naizhao/Pilot-Kit-Box-ESP32-P4/hardware/expansion-board-v4/SELECTIVE_PLACEMENT-zh_CN.md

# V4.5 选择性贴装 / 互斥件总表

英文版：[`SELECTIVE_PLACEMENT.md`](SELECTIVE_PLACEMENT.md)

> 这块板上有若干位号**不是照着 BOM 全贴就对**：有的分版本、有的三选一、
> 有的要看实测、有的平时贴但测天线时要取下。规则原先散在
> `VARIANTS.md`、`ASSEMBLY.md` 和原理图里，集中到这一份。
>
> 这些规则在生成制造文件时有断言把关，贴错会让构建直接失败。
> 文档会过时，断言不会。

本板当前配置：**带电源版（powered）**。

位号在板上的位置：[ASSEMBLY_MAP-V4.6.pdf](ASSEMBLY_MAP-V4.6.pdf)（公开版）、
`internal/装配图-本轮打板-V4.6-zh_CN.pdf`（多标本轮要自己补贴的件）。
两份都按本表的判据生成，与这张表同源。

---

## ① 电源变体 —— 两组逻辑相反 🔴 贴错会烧板

同一块 PCB 出两个版本，**这一组是全表唯一"贴错就烧板"的**：

| | 电源部分（28 个位号） | `R7` `R8`（5.1kΩ CC 下拉） |
|---|---|---|
| **带电源版**（本板） | ✅ 全贴 | ❌ **绝不能贴** |
| 不带电源版 | ❌ 全不贴 | ✅ 必须贴 |

**电源部分**：`U18` `U19` `U20` `L16` `L17` `J9` `RT1` `C70`~`C80` `R37`~`R46`

**为什么会烧**：USB-C 要被主机识别，CC 脚必须有 Rd。带电源版由 CH224K(`U18`)
内部提供；此时再并上外部 5.1k，**CC 阻值被拉低 → PD 协商误判 → 可能请求
9V/12V 灌进按 5V 设计的板子**。反过来，不带电源版没有 CH224K，
若 `R7`/`R8` 也不贴则 CC 悬空——**电脑完全不认，RP2040 固件刷不进去**。

> 板上 `R7`/`R8` 周围印了丝印框，标注 **`NO-PWR VER`** ——
> **框内的件只有不带电源版才贴**。

这一组里有两条选型/装配约束，配料和贴装时都要照顾到：

| 位号 | 约束 |
|---|---|
| `L16` `L17` | 功率电感，**只按电感值配料会拿到 Isat 不够的**——`L16` 要 ≥5A、`L17` 要 ≥4A |
| `J9` `RT1` | 在 **B 面**（`RT1` 是 NTC，必须贴到能测电池温度的位置）|

---

## ② 1090 天线通路 —— 三选一

信号从天线到接收链要经过一个二选一的切换点，有三种实现，**最多只能贴一个**：

| 位号 | 作用 | 贴了之后 |
|---|---|---|
| **`U16`** | 射频开关 SPDT（XA17-G4K）| 软件切换外接/板载，**默认方案** |
| `R24` | 0R 旁路 → 固定走**外接**天线 | 短接 `SW1_J2`↔`SW1_J1`，绕过开关 |
| `R25` | 0R 旁路 → 固定走**板载 IFA** | 短接 `SW1_J3`↔`SW1_J1`，绕过开关 |

```
                    ┌── SW1_J2 ──[C30]── ANT1090_EXT ── J6 / D2 / L14   外接
接收链 ──[C54]── SW1_J1 ──(U16)
                    └── SW1_J3 ──[C53]── IFA_MATCH ── ZS1/ZP2/J7 ── ANT1  板载
                         ↑R25 旁路        ↑R24 旁路接的是 SW1_J2
```

**同时贴的后果**：
- `R24` + `R25` → **外接天线和板载 IFA 直接短路并联**，阻抗全乱
- `U16` + 任一旁路 → 开关的一个端口被短接到公共端，切换失效且可能损坏开关

**默认方案：贴 `U16`，`R24`/`R25` 保持 DNP。**
两个旁路位是留给「不要开关、固定走某一路」的改法，正常不贴。

---

## ③ GNSS 天线通路 —— 只有开关，无旁路

| 位号 | 作用 |
|---|---|
| **`U17`** | 射频开关 SPDT，切换外接 / 内置 patch |
| `J2` | 外接口（经尾线转 SMA）|
| `J8` | 内置 patch 口 |

```
GNSS 前端 ──[C57]── SW2_J1 ──(U17)──┬── SW2_J2 ──[C58]── J2  外接
                                    └── SW2_J3 ──[C59]── J8  内置patch
```

**与 1090 侧的区别：GNSS 侧没有旁路电阻**，不贴 `U17` 就没有任何通路。
**`U17` 装配时必须贴上**，否则 GNSS 完全收不到信号。

**有源天线偏置：** 两路都是有源天线，各有一个偏置 Tee（开关 RF 口不能过直流）。PMOS 源极接模块的 `VCC_RF`(U7.14)，不是 3V3_GNSS LDO 轨——模块据此感知天线电流并输出 `ANTENNA OK/OPEN/SHORT`。

---

## ④ IFA π 型匹配网络 —— 调谐用，不是互斥

| 位号 | 位置 | 默认 | 说明 |
|---|---|---|---|
| `ZS1` | 串联 | **0R**（直通）| `ANT1090_IFA` ↔ `IFA_MATCH` |
| `ZP1` | 并联·天线侧 | **DNP** | `ANT1090_IFA` ↔ GND |
| `ZP2` | 并联·电台侧 | **DNP** | `IFA_MATCH` ↔ GND |

三个可任意组合成 L 型 / π 型，**值由实测定**，不存在互斥。
默认 `ZS1=0R` + `ZP1/ZP2=DNP` 只是一条直通线，**不代表已调谐**。

首轮扫描起点（来自六层 rev2 的 HFSS）：`ZS1=3.6nH`、`ZP2=3.3pF`、`ZP1=DNP`，
手头备 3.6/3.9pF，最终值由装壳后 VNA 定。

---

## ⑤ 经`J7`测量时的条件性后级隔离

`C53`（100pF）串在 `IFA_MATCH` ↔ `SW1_J3` 之间，是板载 IFA 通往射频开关的耦合电容。

必要条件是`C53`后方电气断路。V4.0实测板虽然已贴`C53`，但U17等后级元件未贴，
没有形成负载通路，所以不影响读数。只有后级已经贴通的板才需要拆`C53`或用其它方式隔离。

---

## ⑥ 0R 跳线 —— 默认贴，留作调试断点

| 位号 | 连接 | 用途 |
|---|---|---|
| `R21` | `AD8313_VOUT` ↔ `RF_DET_OUT` | 检波输出→分压网络，断开可单独测 AD8313 |
| `R22` | `ANT_SEL_1090_A` ↔ `V1` | 1090 开关控制线，断开可手动置位 |
| `R23` | `ANT_SEL_1090_B` ↔ `V2` | 同上 |

这三个**默认贴 0R**，不是 DNP，也不互斥。

---

## ⑦ 本来就没有器件的位号

| 位号 | 说明 |
|---|---|
| `ANT1` | 板载 IFA，就是 PCB 铜箔本身 |
| `SW2` | BOOTSEL 焊盘跳线，用镊子短接，**不占贴片面** |
| `H1`~`H4` | M2.5 安装孔（⌀2.7mm NPTH）|
| `FID1`~`FID3` | 光学基准点（简化贴装工艺用不上，保留给需要它的贴装线）|

---

## 这些规则有机器把关

上面每一条在生成制造文件时都有断言把关：变体贴错、互斥件同时贴上、分类
漏掉某个位号，构建直接失败而不是出一份看着正常的 BOM。`release/` 里的
BOM/CPL 是通过了这些检查才落盘的。

所以照这份表核对实物即可；表本身与制造文件同源，不会各说各话。
