naizhao/Pilot-Kit-Box-ESP32-P4/hardware/expansion-board-v4/VARIANTS-zh_CN.md

# V4.5 两个版本：带电源 / 不带电源

英文版：[`VARIANTS.md`](VARIANTS.md)

> 2026-08-23。本文件是**变体设计的唯一基准**，ASSEMBLY-zh_CN.md
> 的选贴规则也以这里为准。

## 1. 划分原则

不是「不贴几个件」，而是**两套各自完整的供电系统**：

| | F 面 | B 面 |
|---|---|---|
| **不带电源版** | 全部传感器 + RP2040 + CC1312R + 射频链 + 三颗 LDO | **零贴装件** |
| **带电源版** | 同上 | J4(USB-C PD) + CH224K + SY6970 + SY7069 + L16/L17 + J9 电池座 + 阻容 |

不带电源版**连电池座都不装**——供电、电量信息全部走微雪主板（`VCC_5V` 从 J1 pin1/pin3 进来，
喂 U1/U2/U3 三颗 LDO）。`VCC_5V` 这条网络是双向的，带电源版由 SY7069 输出反灌 J1，
不带电源版由 J1 输入，同一根走线两种方向，不需要任何跳线或改板。

## 2. 为什么要分：成本在 SMT 面数，不在元件费

嘉立创 SMT 在线计价实测（板 10.00×6.20 cm，5 片，2026-08-23）。
下表用**相对倍数**表示，绝对报价会随时间和批量变化，下单前请自行询价：

| 方案 | 贴片层 | 可选档位 | 相对成本 |
|---|---|---|---|
| 带电源版（697 焊点 / 38 种） | 双面 | **只能标准型** | **2.43×**（基准的 2.43 倍）|
| 不带电源版（598 焊点 / 32 种），**仍双面** | 双面 | 只能标准型 | 2.30× |
| 不带电源版（602 焊点 / 33 种），**单面** | 单面 | **经济型** | **1.00×（基准）** |
| 同上走标准型 | 单面 | 标准型 | 1.57× |

费用构成（这才是关键——差额几乎全在固定费，不在焊点数）：

```
                 双面标准型   单面经济型
工程费              高          低      ← 差额主要来源
钢网费              有          无      ← 单面免钢网费
贴片焊点费          ≈           ≈       ← 两者基本相同
换料费(整盘后)      ≈           ≈
```

**两条结论**：

1. **省钱全靠解锁经济型**——嘉立创的「双面贴片暂不支持经济型」是硬门槛。
   单面即使走标准型也只省一半，走经济型才吃到全部差额。
2. **不做到单面，分版本几乎白做**——双面的两个版本只差 5%，省下的焊点费
   被固定的工程费 + 钢网费吃掉了。

## 3. 什么算「一个贴装面」

判据是**这一面有没有需要机器贴装的器件**，不是「有没有铜」：

| | 占面数 | 说明 |
|---|---|---|
| SW2（SolderJumper 焊盘跳线） | **不占** | 不贴任何料，无工序、无钢网、无过炉 |
| 通孔件（若 J9 改弯针） | **不占** | 计在「插件」栏（手工焊点费 ¥2 + 手工工程费 ¥20，固定） |
| J4 (USB-C，16 个 SMD 触点) | **占** | 只要它在 B 面，这一面就是贴装面 |
| 电源那 28 个 SMD | 占 | 带电源版必然双面 |

所以 SW2 留 B 面对成本零影响，不必为它做任何调整。

## 4. 【已实施 2026-08-23】单面可用怎么做到的

产品原则：**单面可用是保底，双面更优**。所以不带电源版的 B 面必须**零贴装件**。

做了三件事：

| 改动 | 原因 |
|---|---|
| **J4 (USB-C) → F 面右板边** (144.63, 73.00) | 留 B 面的话不带电源版还是双面，只省 ¥35 等于白做。courtyard 右沿贴齐板边 150，开口仍朝 +X（与微雪 H1 同侧）。`USB_DP/DM` 连的 R9/R10 本来就在 F 面 x117，搬过去走线反而更短 |
| **新增 R7/R8（5.1k CC 下拉）→ F 面**，紧邻 J4 2.2mm | 不带电源版没有 CH224K，CC 悬空则主机根本不认设备（USB-C 规范要求 device 端呈现 Rd）。**与 CH224K 二选一**：带电源版不贴 |
| R37 从 (138.80,69.84) 挪到 (137.75,70.75) | J4 的通孔安装脚穿到 B 面，落进了 R37 的 courtyard。顺带把它到 CFG1 脚的距离从 2.97mm 缩到 2.56mm |

**验收：不带电源版的 B 面贴装件 = 0**（只剩 SW2 焊盘跳线和 TP 类不占面数的东西）。

代刷方案（原 §4 方案 A）已否决，理由见 §5——GPIO24/25 是 USB Serial/JTAG 不能做 host，
切换要烧不可逆 eFuse。不冒险，J4 保留。

## 5. 查证记录：为什么 GPIO24/25 不能用

**曾经的错误方案**：把 RP2040 的 USB 接到 J1 的 pin23/21，让 P4 做 host 代刷。
查 ESP32-P4 datasheet 后**否决**：

| USB 外设 | 默认引脚 | 能否 host | J3 是否引出 |
|---|---|---|---|
| **USB Serial/JTAG** | **GPIO24 / 25** | ❌ 纯 device | ✅ pin23/21 |
| USB 2.0 **Full-Speed OTG** | **GPIO26 / 27** | ✅ | ❌ **没引出** |
| USB 2.0 High-Speed OTG | 专用脚 49/50 | ✅ | ✅ pin27/25（与 H2 同网） |

- 微雪 J3-23/21 引出的 GPIO24/25 是 **USB Serial/JTAG**，固定 device，不能做 host
- OTG FS 默认在 GPIO26/27，**J3 上没有这两个脚**
- 要把 OTG FS 切到 GPIO24/25 得烧 eFuse `USB_PHY_SEL`——**一次性不可逆，且烧完 P4 的 USB-JTAG 就废了**，而微雪板已出厂，不是我们能控制的

**只剩 HS 那组（J3-27/25）**，但它与 H2 的 USB-C 口同网，且载板 USB-A（RTL-SDR 方案）
也走这条线，三方只能选一个。

## 6. 为什么 C6 要手工 UART 刷，而 RP2040 不用

这个问题决定了「代刷」到底靠不靠谱，答案是**两者的机制完全不同**：

**C6（见 `docs/hardware/c6_slave_firmware-zh_CN.md`）**要外接 USB-UART 接 P1 排针、
IO9 短地、esptool 写 flash。两个原因：

1. **硬件**：微雪把 C6 的 UART 引到独立的 P1 排针，没接到 P4 的 GPIO，P4 够不着
2. **鸡生蛋**：P4↔C6 走 ESP-Hosted over SDIO，而 SDIO 要通，前提是 C6 里已经跑着
   hosted 固件。空白 C6 没固件 → SDIO 不通 → 只能走 ROM 的 UART bootloader，
   而那需要外部工具握手。所以**首次**必须手工，之后才能 OTA。

**RP2040 没有这个问题**：BOOTSEL 固化在 ROM 里，空片上电（或短接 QSPI_SS）直接
变成一个 USB MSC U 盘，不需要预装任何固件、不需要握手协议。这是架构性差异，
不是配置问题。

## 7. 换主板后（如 RK3506）代刷还成立吗

代刷只依赖一条：**上级有 USB host + 能挂载 MSC**。

| 换成 | 能否代刷 |
|---|---|
| RK3506 等 ARM Linux SoC | ✅ 比 P4 还简单，`mount` + `cp x.uf2` |
| 树莓派 CM / 任何 Linux/Android 主板 | ✅ |
| 纯 MCU 且无 USB host | ❌ |

Pilot Kit 要跑 Flutter UI，主控只会越换越强，这条风险低。且 J1 是 2.54mm 排针，
**任何时候都能从排针飞两根线接 USB 转接头直连电脑**，不需要板上有 USB 座，
不占任何 SMT 面数——这是不依赖上级板的兜底路径。

## 8. R7/R8（5.1k CC 下拉）是必需的选贴件

一度以为不需要——那是建立在「不带电源版没有 J4」的假设上。但按 §4，J4 两个版本
都要贴（否则没法刷 RP2040 固件），所以 CC 就必须有 Rd：

| | R7/R8 | CH224K |
|---|---|---|
| 带电源版 | ❌ 不贴 | ✅ 贴，内部自带 Rd |
| 不带电源版 | ✅ **必贴** | ❌ 不贴 |

**两者互斥**：同时贴会让 CC 阻值错乱、干扰 PD 通信（CH224 手册 §6.1 的 Type-C
母口参考电路里 CC 就是直连芯片、没有外部下拉）。
