naizhao/Pilot-Kit-Box-ESP32-P4/docs/ux/box-4.3-ux-spec-zh_CN.md

# Pilot Kit Box · 4.3″ 触摸屏 UX 规格

英文版：[`box-4.3-ux-spec.md`](box-4.3-ux-spec.md)

**状态**：已定稿（2026-07-27）· **v2.1 修订 2026-08-02**
**适用固件分支**：`v4`
**视觉稿**：[`box-4.3-ux-spec.html`](box-4.3-ux-spec.html) —— 按真实毫米绘制，浏览器直接打开，
含显示器校准工具。**已同步到 v2.1**，两份说法一致；不一致时以本文件与代码为准。

版面真源在 `firmware/main/nav_grid_page.h` 的常量区——本文件描述意图，那边是数。

---

## 1. 背景

迁移前基线是 2.4″ 320×240 SPI 屏 + 四个物理按钮；当前硬件已经切换到
微雪 ESP32-P4-WIFI6-Touch-LCD-4.3（480×800 原生竖屏，PPA 逆时针
270°、等效顺时针 90° 后按 **800×480 横屏**使用，GT911 电容触摸）。
控制器支持五点，但当前固件只读取第一触点。

最终目标屏为 5″ 800×480 半反半透（同分辨率），本规格可 1:1 迁移。

### 产品定位（决定所有取舍）

一台设备服务两类用户：

| 用户 | 场景 |
|---|---|
| **爱好者** | 地面观测周边飞机 → 空中录制 + 看姿态 → 落地分享 |
| **飞行员** | 机载备份仪表（**应对 Garmin 高温死机**）+ 交通避撞 + TF 卡记录 + GDL90 喂 App |

共同主页面为「PFD + 下部雷达半透明 overlay」。

---

## 2. ⚠️ 物理尺寸约束（最高优先级）

| 屏 | 分辨率 | 物理尺寸 | 像素密度 | 16px 汉字实际高 |
|---|---|---|---|---|
| 旧 2.4″ | 320×240 | 48.8 × 36.6 mm | 6.56 px/mm · 167 PPI | 2.44 mm |
| **新 4.3″** | 800×480 | **93.7 × 56.2 mm** | **8.54 px/mm · 217 PPI** | 1.87 mm ⚠ |
| 终 5″ | 800×480 | 108.9 × 65.3 mm | 7.35 px/mm · 187 PPI | 2.18 mm |

**4.3″ 横屏物理尺寸约等于一张信用卡（85.6 × 54 mm）。**

> **分辨率提升只带来清晰度，不带来空间。**
> 新屏 217 PPI 比旧屏 167 PPI 还高 30% —— 同样像素数在新屏上**物理更小**。

### 字号阶梯（硬约束）

| 级别 | 物理 | 4.3″ | 5″ | 用途 |
|---|---|---|---|---|
| XL | 5.0 mm | 43 px | 37 px | PFD 当前值 |
| L | 3.5 mm | 30 px | 26 px | 页面标题 |
| **M** | **3.0 mm** | **26 px** | **22 px** | **正文主力** |
| S | 2.5 mm | 21 px | 18 px | 标签 / 单位（**顶栏状态栏走 M 档**，见 §5.1）|
| XS | 2.1 mm | 18 px | 16 px | **硬下限**，仅极次要 |

**低于 18 px（2.1 mm）的字号一律禁止出现。** 旧屏 8×8 汉字（1.22 mm）在新屏对应仅 10 px，永久废弃。

### 各页面容量（按 4.3″ 实测字高定）

| 页面 | 容量 |
|---|---|
| 空管看板 | **7 列 × 7 行**（机型、SQK 入详情） |
| 雷达右栏 | **4 张卡** |
| 诊断卡片 | **每卡 1 行核心值**（详情另开页） |
| 设置页 | **7 行满屏**，第 8 项需滚动 |

---

## 3. 交互模型

### 3.1 物理按键：全部取消

- deep sleep 功能取消（实测休眠功耗降不下来，无实用价值）
- 四个按钮（TARE/MODE/UP/DOWN）全部删除，`button_task.c` 退休
- 板载 POWER 键为**硬件电源开关**（接电源管理 IC，非 GPIO，软件不可读）
- **软件层面 100% 触摸输入**

释放 GPIO：外设需求从 10 根降至 6 根（IMU INT/RST ×2、BARO_INT ×1、GPS ×3）。

### 3.2 FAB + 全屏导航网格

| 一级页面 | 二级页面 |
|---|---|
| FAB = **☰** 点击打开全屏导航网格 | FAB = **←** 点击返回 |

#### 为什么不是横向 dock

一条从 FAB 那侧滑出的横向 dock（导航页签 ×94 px｜分隔线｜动作区「调平」）在
800×480 上**排不下**：

```
7 个页签 × 94 ＋ 分隔 8 ＋ 动作区 94 = 761 px
FAB 两侧留白之后的可用宽度          = 720 px      → 溢出 41 px
```

第 8 项进不来，而页签已经窄到 94 px——再缩就跌破 44 px 触摸下限，换行则宣告
这个形态不成立。因此采用**全屏导航网格**（版面真源 `sim/proto-navgrid/proto.c`）。
若有人再提议「点 FAB 弹一条横向工具条」，先把上面那三行宽度账算一遍。

#### 网格版面（`nav_grid_page.c`）

| 区 | 几何 | 内容 |
|---|---|---|
| 顶栏 | y 0–48，**不遮罩** | 露出**底页自己的**顶栏（底页是 PFD 时即 §5.1 那条状态栏：星数 / 目标数 / REC / 温度 / 蓝牙 / 电量，菜单期间也要能看状态）|
| 网格 | y 48–360，4 列 × 2 行，格 **200 × 156** | 每格：64 px 图标 + M 档标签 |
| 分页点 | y 368，12 px | 仅状态指示，**不可点** |
| 动作条 | y 392–480，高 **88 px**，三等分 | 调平（警示橙）｜屏幕亮度｜关闭 |

- **两页**：第 1 页 7 项（PFD / 交通 / 地图 / 列表 / 搜索 / 记录 / 工具）+ 1 格余量；
  第 2 页 3 项（诊断 / 设置 / 关于）。切分点是**常用度不是塞满**——飞行中最常按的
  几个不该为了凑满一页而往后挪。
- **格子位置钉死，末页不居中**：位置随项数浮动的话，同一功能在两页上落在不同
  坐标，手指记不住位置——而记得住位置正是网格相对列表的全部优势。
- **未实现的「记录」「工具」置灰占位**，不从版面拿掉：将来补上时版面一个数都不用改。
  点了不弹提示，置灰视觉本身就是信号。
- **底页压暗 9%**（不是纯黑遮罩）：地平线的明暗分界仍能隐约辨出，飞行员不会在
  菜单打开的这两秒里失去姿态参照；但白底黑字的高度带 / 速度带不再能读出内容。
- **打开即藏 FAB**：网格铺满全屏且命中判定排在 LVGL 之前，FAB 留着就是"自己点不动、
  又盖住底下的格"，而且它可拖动，挡住哪一格不可预测。出口写在屏上（动作条「关闭」）。

**三条退路**（无物理按键，任何一条失效都还剩两条）：
① 动作条「关闭」　② 第 1 页继续右滑　③ 6 s 无操作自动收起

> 初值沿用 dock 的 5 s（图的是不打破既有手感），2026-08-02 真机走查后调到 **6 s**：
> 网格两页十项比 dock 内容多，翻页才看得全，5 s 不够看完就被收走。
> 真源是 `nav_grid_page.c` 的 `NAV_IDLE_MS`，这个值只能上机试，不要在桌面上推。

**手势**：左右滑动翻页，阈值 60 px（≈7 mm）且横向位移须 > 2× 纵向；过阈值**当场翻**
不等松手；一次长滑可连续翻多页。「调平」沿用长按 1 s 才生效（短按只提示）。

#### FAB 可拖动 + 位置记忆（与 Pilot Kit App 手感一致）

- 长按 **200 ms** 进入拖动态（避免与点击冲突），FAB 半透明 + 亮边 + 阴影加重
  （**不能用 transform_scale**：会让 LVGL 走 TRANSFORM layer，64 KB 池分配不出整块
  buffer，单线程 LVGL 会死在忙等里）
- 拖动实时跟手，垂直位置自由
- 松手后**水平吸附至最近的左 / 右边缘**，不允许悬停中间遮挡内容
- 位置持久化至 NVS：`fab_side`(L/R) + `fab_y`(0~100%)
- 网格是全屏的，**不随 FAB 那一侧翻转**（dock 时代才需要反向铺开）
- 校准向导页不显示 FAB

### 3.3 手势

| 手势 | 作用 |
|---|---|
| 单指垂直滑动 | 列表滚动（雷达右栏、看板、设置、诊断详情） |
| 单指水平滑动 | 导航网格翻页（阈值 60 px 且横向 > 2× 纵向） |
| 右滑 | 二级页面返回；导航网格第 1 页则关闭 |
| 下滑 | 关闭详情抽屉 |

---

## 4. 导航结构与返回规则

> **无物理按键 = 没有系统级返回。** 二级页面若不设计返回，用户进去即出不来。
> 以下路径实现时必须逐条覆盖。

### 4.1 页面分类

| 类型 | 成员 | 特性 |
|---|---|---|
| **一级页面**（7） | PFD / 交通雷达 / 地图 / 空管看板 / 诊断 / 设置 / 关于 | 互相平级，仅通过 **FAB → 全屏导航网格**切换 |
| **模态层**（铺满全屏，压在某一页之上） | 导航网格 / 搜索 / 机场详情 / 键盘编辑器 | 不是 `pk_ui_mode_t` 的一站；打开即藏 FAB，出口写在自己屏上；优先级由 `pk_ui_modal_top()` 单点决定 |
| **二级页面**（全屏替换） | 诊断 → 子系统详情 ×8 | FAB 变 ←，顶栏出现「← 诊断」，此时 FAB 不再是菜单键 |
| **覆盖层**（不替换一级） | 目标详情抽屉 / 格式化确认 / 校准向导 / Toast | 各自带关闭 + 点外部关闭 |

> 一级页面从 6 涨到 7（地图页），并且还有「记录」「工具」两个占位——横向 dock
> 装不下这个数，正是 §3.2 换成网格的直接原因。网格再加项只是多一页，不再有
> 「排不下」这回事。

### 4.2 返回路径

| 所在位置 | 返回方式（任一可用） | 返回目标 |
|---|---|---|
| 一级页面 | —（顶层） | — |
| 子系统详情页 | ① 顶栏「← 诊断」② FAB（此时为 ←）③ 右滑 | 诊断总览 |
| 目标详情抽屉 | ① 「关闭」② 点上方列表区 ③ 下滑 | 看板页（保留选中行） |
| 格式化确认框 | ① 「取消」② 点遮罩 ③ **5 s 超时自动取消** | 设置页 |
| 校准向导 | ① 「稍后再说」② acc≥2 自动退出 | 进入前的页面 |

**特例**：目标详情抽屉的「绑定为本机」是**跨层跳转** —— 执行后关闭抽屉并**直接跳转 PFD**
（让飞行员立刻看到以新 own-ship 为基准的地平线），不返回看板页。

### 4.3 原则

- **层级最多 2 层，不做返回栈**。二级页面只能从诊断进入，返回目标唯一确定。
- **FAB 位置固定不变**，用户只需记住"右下角圆钮"一个位置。

---

## 5. 页面规格

### 5.1 PFD 主页

```
顶栏      48 px   HDG 082° ｜ (卫)17 (机)6 (●)REC (温)88°C ｜ (蓝) (电)100%
主区     292 px   速度带 100 ｜ 姿态区 600 ｜ 高度带 100
底部 HSI 140 px   罗盘 + 交通目标叠加
```

- 速度带下方换算区：km/h + mph（沿用现有设计）
- 高度带下方换算区：VS + m/s（GS/VS 不再单独占角落文字位）
- **姿态区刻意留空**，不加航迹矢量 / 坡度 / G 值等（半反半透屏元素越少越读得出）

#### 顶栏（状态栏）—— 真源 `pfd_statusbar.c` / `pfd_layout.h`

早期版式是 `HDG · ●GPS ●REC ●BLE 🔋 · ADSB 计数` 这样的圆点 + 字母缩写。
**已作废**：圆点只说得出"有/没有"，说不出"几颗星""几架飞机"，而
`ADSB`／`REC` 这类缩写在 26 px 上一项就吃掉 60~90 px。现在中段与右段全部
图标化，图标提供语义、数字提供读数（孤立的 `100%` 看不出是电量还是亮度）。

图标取自 **Material Symbols Rounded**（Google，Apache-2.0），经
`firmware/scripts/gen_pfd_icons.py` 生成 **30 × 30 px、4bpp 灰度**字形表
（`pfd_icon_font.h`），与文字**共用同一条 alpha 混合路径**（`pk_aa_blit_4bpp`），
边缘处理完全一致。FILL 轴按图标取舍：卫星 / 目标 / 录制 / 温度 / 蓝牙取实心
（小尺寸下比线框立得住），**电池取轮廓**（填成实心就看不出电量了）。

顶栏文字是 **M 档（26 px）**，不是 S 档。

| 段 | 槽位（自左向右） | 图标（Material 名） | 内容与颜色 | 数据来源 |
|---|---|---|---|---|
| **左**（常驻） | HDG | 无，青色 `HDG` 文字标签 | `082°` 绿；无航向 `---°` 灰 | `pk_own_heading_resolve()`：ADS-B 绑定机 > IMU yaw > GPS track（≥2 kt） |
| 中 | 卫星 | `satellite_alt` | 星数 绿；无 fix `NO FIX` **红** | `pk_gps_get()` |
| 中 | ADS-B 目标数 | `connecting_airports`（画的是**两架**飞机，要的是"周围有 N 架"的复数语义） | 计数 绿 | `aircraft_state_snapshot()`，60 s 新鲜窗 |
| 中 | 录制 | `fiber_manual_record` | `REC` 红，**仅正在写记录时出现** | `rec_active` |
| 中 | 温度 | `thermometer_alert`（温度计 + 感叹号，比通用三角贴切） | `88°C` 警示橙，**仅超温时出现** | `pk_soc_temp_get()`，见下 |
| **右**（常驻） | 蓝牙 | `bluetooth` | **只有图标、没有文字**（符号本身即可表意），青；未连接则整枚不画 | `ble_gatt_is_connected()` |
| **右**（常驻） | 电量 | `battery_android_*` | 百分比，见下 | `pk_batt_get()` |

几何（`pfd_layout.h`）：条高 48 · 左边距 12 · 右边距 16 · 图标与其数值间隙 2 ·
组内间隙 8（`PFD_BAR_GAP_LABEL`）· 词组之间 16（`PFD_BAR_GAP_WORD`）。

**降级规则**（不是"藏起来"，是整项丢弃）：

- 中段优先级 **GPS > ADSB > REC > TEMP**，依据是"不知道会出事"的程度；
  装不下就从最低优先级那端逐项丢，**GPS 永不丢**。320 屏中段只放得下一项、
  800 屏放得下四项，靠这套规则自适应，不为每种屏手算坐标。
- **左端 HDG 与右端蓝牙 / 电量不参与降级** —— 后两者是「设备自身」的状态而非
  「飞行」的状态。
- 右段按**最坏宽度**（两个图标 + `100%`）预留，蓝牙断开时中段不平移；
  但中段自身是在剩余空间里**居中**的，所以 REC / 温度出现或消失时中段会整体
  重新居中。

**全空态**（实拍 `images/empty-4.3-pfd.png`）：`HDG ---°`（灰）·
卫星图标 + `NO FIX`（红）· 目标图标 + `0`（绿）· **没有** REC / 温度 / 蓝牙 ·
电量照常显示（电池焊在板上，没有"没接"这一说）。

**电量的两个特殊态**：

- 图标是 `battery_android` 系列的 **alert → _0…_6 → full 九档连续刻度**，
  `step = (pct×8+50)/100` 一次线性映射，**形态本身就是读数**。此前的
  `battery_horiz_*` 只有三档，20% 与 4% 会渲染成同一个空壳、只能靠颜色区分。
  末档取 `full` 而不是 `_6`：`_6` 内部还留着一条黑，拿它当 100% 会一直显示成
  "还差一格"。
- 颜色：常态**白**（航电惯例白 = 正常/仅供参考，绿留给需要主动确认有效的读数：
  航向、星数、目标数）· `<25%` 警示橙 · **`≤6%` 红，并同时换成 alert 图标**
  （阈值正是九档刻度里 alert 那一档的覆盖范围，变红与换图标同时发生，
  不各走各的）。实拍 `images/ui-4.3-battery-low.png`。
- **充电**：改播 `battery_android_frame_1…6 → frame_full` 的**逐帧动画** ——
  静态闪电只说明"接了电"，动画才说明"电真的在进"。每帧 300 ms、整周期 2.1 s
  （座舱里任何接近 1 Hz 的动效都会被余光当成告警去抓一下注意力，而充电是最
  不需要被注意的状态）；相位由 `uptime_ms` 算而非数渲染帧，固件与模拟器帧率
  不同也快慢一致。充电时颜色**一律白**：正在回升的低电量不是需要处置的异常，
  涂红只会制造假警报。实拍 `images/ui-4.3-charging.png`。

**温度**：读的是 **SoC 结温**（`soc_temp.c`，1 Hz 采样），不是 BMP388 那颗测
座舱环境温度的传感器 —— 暴晒时二者能差二三十度，「设备自己在过热」是另一回事。
阈值 `CONFIG_PK_SOC_TEMP_WARN_C`，当前 **85 ℃ 触发 / 78 ℃ 解除**（7 ℃ 滞回，
免得那一格出现又消失、把飞行员训练成忽略它）。实拍里显示的 78 ℃ 是模拟器强制
点亮这一格的 mock 值（`sim/main.c`），不是真机的触发点。

**演示模式**：顶栏最右端常驻一枚 96 × 32 的 DEMO 徽标（画在 LVGL 控件层），
所有右对齐内容统一走 `pk_ui_topbar_right_limit()` 退让，中段跟着一起退 ——
顶栏本来就有一套"装不下就按优先级丢"的机制，把新的可用宽度告诉它就够了。
实拍 `images/demo-4.3-pfd.png`。

**这条状态栏只有 PFD 页有。** 其余整屏页面各画各的顶栏（同高 48 px、
标题同为 M 档）：交通 = 标题 + HDG + 目标数 + 朝向/量程；空管看板 = 标题 +
目标数 + 排序说明 + RESET（非默认排序才出现）；地图 = 标题 + 右上角瓦片层级 `Z12`；
设置 / 诊断 / 关于**只有左上角一个标题**；诊断子系统详情页顶上是 LVGL 的
`← 诊断` backbar，子系统名画在内容区第一行（`diag_page.c :: draw_detail_header`）；
罗盘校准向导是全屏页，**没有顶栏**。导航网格与 Toast 压在当前页之上，
露出的是**底页自己的**顶栏。

### 5.2 交通雷达页

- 左雷达 520 px（距离环 6/13/20 NM，本机居中），右栏 280 px 放 4 张卡片可滚动
- **本机符号：飞机俯视剪影**（黄色，6.5 mm）
  - 机头朝上模式：机头恒指屏幕上方
  - 正北朝上模式：按当前航向旋转
  - 由设置页「地图朝向」切换
- **目标符号：飞机俯视剪影**（3.8 mm），**按各自 ADS-B track 航向旋转**
  —— 一眼可辨迎面 / 同向，此信息三角形无法表达
- 右栏卡片：方位八向箭头 + 呼号 + 距离 + 高度（带升降率）+ 速度
- 量程由雷达右下角 +/− 两枚按钮切换（**不做双指捏合**：量程只有
  三四档，用不上捏合的连续性，而戴手套、颠簸时双指手势最容易做废）

### 5.3 空管看板页

7 列 × 7 行，行高 48 px，字号 21 px，可垂直滚动。

| 列 | 方位 | 呼号 | 距离 | 高度 | 升降 | 速度 | 航向 |

红底 = 威胁。点击行 → 详情抽屉（高 230 px，保留上方 2 行可见），
抽屉内补全被砍列：机型 / SQK / ICAO / 航司 / 国籍。

### 5.4 设置页

行高 64 px，控件按钮高 38 px。

| # | 项 | 控件 |
|---|---|---|
| 1 | 语言 | 分段（中文 / EN） |
| 2 | QNH | 步进器（− / 值 / +） |
| 3 | 地图朝向 | 分段（机头上 / 正北上） |
| 4 | 雷达量程 | 分段（10 / 20 / 40） |
| 5 | **屏幕亮度** | 分段（低 / 中 / 高 / 自动）**新增·必需**（原 UP/DOWN 键调节） |
| 6 | **日间/夜间配色** | 分段**新增**（为半反半透屏铺路） |
| 7 | 记录存储 | 分段（Flash / SD 卡） |
| 8 | 格式化 SD | 危险按钮（**需滚动可见**） |

格式化保留现有**两步确认状态机**：首次点击变「再点确认 5s」，超时复位；无卡 / 正写时置灰。

### 5.5 诊断页

2 × 4 卡片，每卡 10.8 mm 高，仅显示**标题 + 一行核心值**。
八格固定：IMU / BARO / GPS / SDR / BLE / LOG / CLK / **SYS**。

**SYS 卡为新增**，含芯片温度 —— 产品定位是"Garmin 高温死机时的备份"，
自身温度必须可见。超温时 **PFD 顶栏中段多出一格「温度计图标 + 结温」**
（警示橙，不是红；红在本项目里留给 `NO FIX` / `REC` / 低电这类"已经出事"）。
阈值 `CONFIG_PK_SOC_TEMP_WARN_C`：当前 **85 ℃ 触发 / 78 ℃ 解除**（见
`soc_temp.c`，7 ℃ 滞回）。

**点卡片进入子系统详情页**，详情必须保留 `diag_page.c` 现有全部深度，尤其：

- **GPS**：fix/HDOP、可见星、天线状态、经纬度、**每星座独立一行的 SNR 柱状图**
  （排查 no-fix 的命门 —— 不能只盯 `fix=0`，要看 SNR 和天线）
- **IMU**：cal N/3 + roll/pitch/yaw + 采样率
- **BARO**：hPa / alt / VS / 温度 / QNH / IIR 系数

### 5.6 关于页

**纯静态身份**：logo / 版本 / 构建时间 / 依赖版本（IDF、LVGL）/ 硬件**型号**（不带在线状态灯）+ 二维码。

所有 ✓ 状态、校准精度、实时数值**一律归诊断页**，两页零重复。

### 5.7 罗盘校准向导

自动进入（acc=0 持续）/ 自动退出（acc≥2 持续），沿用现有逻辑。

**新增「稍后再说」按钮** —— 原靠 MODE 键关闭，按键删除后若不补此按钮，
用户在磁干扰环境下会被**永久卡在本页**。点击后本次开机不再自动弹出（重启复位）。
本页不显示 FAB。

> 「稍后再说」关掉自动弹出之后，必须留一条**手动入口**，
> 否则用户后来想校准时无路可走（自动闸门要等 acc 真的上过 2 才复位）。
> 入口做在**设置页倒数第二行「罗盘校准」**：左边是项名，右边的值框显示当前
> 精度 `质量 n / 3`（一眼判断该不该点），点击进入本页。
> 走 `pk_ui_cal_wizard_enter()` 而不是通用的切页函数——它同时把自动弹出的闸门
> 重新武装，"用户主动来校准"这件事必须能覆盖之前那次「稍后再说」。
> **不进导航网格**：那张表列的是页面，校准是一次动作。

---

## 6. 术语：TARE → LEVEL / 调平

`TARE` 源自称重业"去皮"，飞行员不熟悉。该功能实为 **caging**
（即传统陀螺仪"把罗盘拨杆往外拔"的动作），现有实现也只 cage 横滚/俯仰、航向解耦。

**采用**：英文 `LEVEL`，中文「**调平**」（Dynon SkyView 即用 Level）。

### 四态交互

| 态 | 行为 |
|---|---|
| ① 待机 | 全屏导航网格的动作条左格显示「调平」（警示橙）|
| ② **短按** | **不执行动作**，弹 Toast「长按 1 秒调平地平仪」，1.5 s 后消失（`ui_state.c` 的 `UI_TOAST_DURATION_US`；实现是显示/隐藏，没有淡出动画） |
| ③ 按住 | 橙色填充从左向右走满 1 s，松手或滑出按钮即取消（填充同帧消失） |
| ④ 完成 | 那一格绿闪 200 ms（标签反白成底色）+ Toast 确认，闪完网格自动关闭 |

② 为必需 —— 否则用户点一下没反应会认为按钮失灵。

**③ 的填充色**是 `COL_ACT` 压到 35% 的同色底（`nav_grid_page.c` 的
`COL_ACT_FILL`），不是另一个色相：填充是背景、橙色标签是前景，同色系才读成
「这一格自己在充满」。这一档对标签 5.5:1、对动作条底色 2.0:1，是"字不被吃掉"
与"进度看得出来"两头夹出来的。**不做插值/缓动**——网格打开时约 6 FPS
（真机实测），1 s 只有 6 帧，每帧按当前时刻直接算宽度即可。

**④ 的 200 ms** 是这块屏上"至少能保住一帧、又不至于读成卡顿"的下限。绿档
（`COL_OK`）调色板里原本没有，座舱里绿 = 正常/确认，与 `COL_ACT` 的橙 = 需注意
必须拉开，所以不能拿现成色改亮度凑。关闭网格因此比执行调平晚 200 ms：
`nav_grid_page.c` 的既有规矩是「关闭一律等松手」（手指还按着就清 `s_active`
的话，剩余帧会落到底页，底页是地图时会被判成新按下并跳进机场详情页）；
绿闪把关闭再往后推到 `render()` 结算，手指此时已离屏，不与那条规矩冲突。

---

## 7. 技术架构：迁移至 LVGL v9

### 7.1 决策依据

新 UX 需要可滚动列表、详情抽屉、分段控件、步进器、FAB 展开动画、手势识别 —— 
纯自绘 framebuffer 需从零手写惯性滚动、动画插值、事件命中测试。

LVGL v9 全部内建，且 `esp_lvgl_adapter` 提供 PPA 旋转与防撕裂
（正是本次需重写的渲染管线）。微雪 BSP 与同类厂商例程均基于 LVGL v9。

### 7.2 现有代码复用情况

| 元素 | LVGL 实现 | 现有代码 |
|---|---|---|
| PFD 姿态仪 | `lv_canvas` | ✅ `pfd_attitude.c` |
| 速度带 / 高度带 | `lv_canvas` | ✅ `pfd_tape.c` / `pfd_speed_tape.c` |
| HSI + 交通叠加 | `lv_canvas` | ✅ `pfd_hsi.c` / `pfd_hsi_traffic.c` |
| 交通雷达 | `lv_canvas` | ✅ `traffic_page.c` / `traffic_geom.c` |
| GPS SNR 柱状图 | `lv_canvas` | ✅ `draw_snr_row()` |
| 校准 8 字动画 | `lv_canvas` + `lv_timer` | ✅ `cal_wizard.c` 双纽线 |
| QNH 步进 / 格式化确认 / 调平 / Toast | `lv_button` / `lv_msgbox` / `lv_bar` | ✅ 逻辑层全部复用 |
| 顶栏状态栏 | **不用 LVGL**，直接画 framebuffer | ✅ `pfd_statusbar.c` + `pfd_statusbar_icons.c` |
| FAB / 返回栏（← 诊断）/ Toast / DEMO 徽标 | LVGL 控件树 | 新增 |
| 导航网格 / 搜索 / 机场详情 / 键盘 | **不用 LVGL**，直接画 framebuffer | 新增（见下）|
| **字体** | `lv_font_conv` 子集，5 档字号 | ❌ **5 套自研字体（200 KB）退休** |

**核心 PFD 绘制资产零重写** —— 它们本就是"往 buffer 写像素"，改为写入 `lv_canvas` 的 buffer 即可。

> **全屏模态层为什么不用 LVGL 对象树**（2026-08-02 实测）：一层全屏需要
> 800×480×2 = 768 KB 的绘制表面，而 `CONFIG_LV_MEM_SIZE_KILOBYTES=64` —— LVGL 堆
> 总共只有 64 KB，分配不出这么大一块 layer；失败时 `lv_draw.c` 在 `LV_OS_NONE` 下
> 是**裸忙等**，单线程 LVGL 当场死锁（长按 FAB 死机那次就是同一个坑）。
> 所以导航网格 / 搜索 / 机场详情 / 键盘一律直接在 RGB565 framebuffer 上手绘，
> LVGL 只留给 FAB、返回栏、Toast、DEMO 标识这几个小控件。

### 7.3 字体系统

早期 320×240 时代曾有 5 套并存、共约 200 KB 的自研字体——这不是设计选择，
是小屏逼出的妥协（`pfd_font_aa.h` 注释即言明为规避 "gray antialiasing
fringes or TTF hinting artifacts"）。连同各自的生成脚本与渲染器，现已全部
删除，统一为两套：

- `pfd_font.c`（5×7 ASCII 位图）：仅用于 1~2 字符的极小标注
- `pfd_aa_font.c`（`gen_pfd_aa_font.py` 生成，TTF 派生）：中西文同一份、四档抗锯齿

- 统一 `lv_font_conv` 生成，按字号阶梯出 5 档
- **i18n catalog 子集机制保留**（`i18n_catalog.py` → `gen_i18n_assets.py`），
  新增中文词条必须走此流程，否则渲染为 `?`
- 本次新增待入表词条：`调平`、`长按 1 秒调平地平仪`、`稍后再说`、`屏幕亮度`、`配色`、`日间`、`夜间`

---

## 8. 硬件迁移要点

### 8.1 引脚映射（40PIN 排针）

微雪 4.3 官方 BSP 已确认与现有硬件的关键一致性：

| 功能 | 4.3 板 | 现有 P4-WIFI6 | |
|---|---|---|---|
| I2C | GPIO7/8 | GPIO7/8 | ✅ 相同 |
| C6 SDIO | GPIO14-19 | GPIO14-19 | ✅ 相同 |
| C6 reset | GPIO54 | GPIO54 | ✅ 相同 |
| microSD | GPIO39-44 | GPIO39-44 | ✅ 相同 |
| LCD 背光 / RST | GPIO26 / GPIO27 | （TARE 键 / BARO_INT） | ⚠️ **冲突** |

**外设改接方案**（排针实际引出 22 个自由 GPIO，需求 6 个，余量充足）：

```
I2C0（IMU/BMP388）   SCL/SDA 引脚      不变
IMU INT / RST        GPIO34 / GPIO28
BARO_INT             GPIO31           （原 GPIO27 被 LCD RST 占用）
GPS P4 RX / P4 TX / PPS  GPIO51 / 49 / 50 （P4 视角；均为 Rev1.2 4.3″ 迁移后值）
RTL-SDR              排针 DP/DM       = P4 专用 USB 2.0 HS PHY
```

### 8.2 扩展板

主板已含屏、触摸、电源管理、锂电接口、RTC、USB、microSD。
自绘 PCB 从"完整载板"降级为**外设扩展板**：GPS + IMU + BMP388 + 1090 MHz IFA 天线 + 40PIN 排母。

- 主板侧为**贴片排母**（2×20 / 2.54 mm / 塑高 3.5 mm）→ 扩展板用**公排针**
- 元件建议朝外布置（GPS 陶瓷天线与 IFA 天线不被主板与屏幕遮挡）
- **必须用 M2.5 铜柱锁固**：贴片排母机械强度有限，而设备处于持续振动环境
- 建议仅在实际使用的 pin 位装针，降低插拔力

---

## 9. 待办（不影响架构，实现阶段推进）

- **半反半透日间模式配色** —— 目标屏反射态对比度仅 7:1、色域 16.5%，红/黄可能难以分辨，
  威胁等级需改为「形状 + 亮度」编码，需出第二套配色，**等实物到手实测后定**
- Toast 样式细节 / 启动画面 / 爱好者「地面观测模式」入口
- 5″ 半反半透屏为 **TN 面板**（视角 θL60/θR50/θU60/θD60 @CR>2），
  整机安装角度必须正对飞行员，右侧视角仅 50°
- 目标屏工作温度上限 70 ℃，座舱暴晒存在超温风险，需评估宽温版本

---

## 附：预览校准

视觉稿 `box-4.3-ux-spec.html` 全部按**毫米**绘制。CSS 规范固定
`1 mm = 3.7795 CSS px`（96 px/inch），与真实显示器 DPI 无关 ——
**高分屏上不校准会显示为实际的 38%~75%**。

打开后首屏用信用卡（85.6 × 54.0 mm）实测校准，结果存 `localStorage`；
亦可用 URL 参数 `?cal=2.3` 或修改文件内 `DEFAULT_CAL` 固定。

**实施时以像素值为准**（26 px / 48 px / 56 px 等），毫米仅用于人眼校验尺度感。

> 设计者显示器：3008 × 1692 逻辑分辨率（2026-07-27 记录）
