naizhao/Pilot-Kit-Box-ESP32-P4/docs/configuration-zh_CN.md

# 配置参考

英文版：[`configuration.md`](configuration.md)

本文档列出 Pilot Kit Box 固件**所有用户可能需要调整的 sdkconfig 配置**，按主题分组，并解释每个选项的影响。如果你只是想"开机即可"，按 [`docs/BUILD.md`](BUILD.md) 走默认值即可——本文档是给想做定制的人看的。

> 📍 **改配置的入口**：
> ```bash
> cd firmware
> idf.py menuconfig
> ```
> 终端 UI 会出来，方向键导航，`/` 搜索，`?` 查每个选项的帮助。
>
> 改完保存退出后，重新 `idf.py build` 即可。
>
> **永久化默认值**：如果你想让某个改动跟着 git 提交（让所有协作者都用同一配置），把对应 `CONFIG_*=...` 行加到 `firmware/sdkconfig.defaults`。`sdkconfig` 文件**不进 git**（在 `.gitignore` 里），每个人本地可以自由覆盖。

---

## 目录

1. [**扩展板板系 (v3 / v4)**](#1-扩展板板系-v3--v4)
2. [硬件目标 (P4 silicon revision)](#2-硬件目标-p4-silicon-revision)
3. [分区表与 Flash](#3-分区表与-flash)
4. [ADS-B 接收链路（RP2040 扩展板）](#4-ads-b-接收链路rp2040-扩展板)
5. [蓝牙 / BLE / ESP-Hosted](#5-蓝牙--ble--esp-hosted)
6. [Own-ship 绑定](#6-own-ship-绑定)
7. [存储 / LittleFS / MicroSD](#7-存储--littlefs--microsd)
8. [显示 / ST7701 MIPI-DSI](#8-显示--st7701-mipi-dsi)
9. [IMU / BNO085](#9-imu--bno085)
10. [触摸与电源](#10-触摸与电源)
11. [日志输出](#11-日志输出)
12. [FreeRTOS 调度](#12-freertos-调度)
13. [编译优化](#13-编译优化)
14. [改完配置之后](#14-改完配置之后)
15. [想加新配置项](#15-想加新配置项)

---

## 1. 扩展板板系 (v3 / v4)

| 配置项 | 默认 | 说明 |
|---|---|---|
| `CONFIG_PK_BOARD_PROFILE_V4` | `y` | 为 **v4 板系**编译（当前默认） |
| `CONFIG_PK_BOARD_PROFILE_V3` | `n` | 为 **v3 板系**编译 |

> **选的是板系，不是修订号。** `v3` / `v4`（将来还有 `v5`）指扩展板板系；
> `V3.9` / `V4.3` 只是这两个板系当前的修订。修订滚动不需要改固件——
> V4.4 出来了照样用 `v4` 固件。下面的角度实测自 V3.9 与 V4.3，而
> `hardware/test_firmware_board_profile_contract.py` 会把固件里的角度表与
> 两个 `kicad_pcb` 现场对拍，哪天某个新修订转了传感器，它先变红。

两者互斥（Kconfig `choice`），必须且只能选一个。**没选任何一个不会静默走默认值，而是编译期直接报错**：

```
#error 没有选择扩展板板系：请在 menuconfig 的 Pilot Kit Box 里选
       PK_BOARD_PROFILE_V3 或 V4。板型不能在运行时靠探测猜。
```

> ⚠️ **这跟下一节的 P4 silicon revision 是两回事。**
> `CONFIG_ESP32P4_*` 说的是主控芯片的流片版本；这一节说的是**扩展板**的 PCB 版本。
> 两者互不相关，改错哪一个都不会提示另一个。

### 为什么必须手选，不能自动探测

v3 与 v4 两个板系把传感器**贴在不同的角度**上（实测自各自当前修订 V3.9 / V4.3）：

| 器件 | v3 | v4 |
|---|---:|---:|
| U4 BNO085（IMU） | 0° | **+90°** |
| U5 BMP388（气压） | 0° | -90° |
| U6 QMC5883P（磁力计） | 0° | -90° |
| U7 ATGM336H（GNSS） | 0° | 0° |

注意 U4 和 U5/U6 **转向相反**，所以这不是"整板转 90°"，两颗姿态相关的器件各有一套
board-to-body 变换。

选错板型的症状很坏：**PFD 照样有姿态、照样跟着动，只是横滚整体偏 90°**——地面上摆着看
不出来，飞起来才发现。所以固件宁可编译期报错，也不给"猜一个"的余地。

固件**不会**、也**不允许**用运行时探测来判板型。板上唯一随版本变化的 I²C 器件是 SY6970
PMIC，而它表达的是 powered / unpowered **变体**，不是板子版本：V3 和一块没装电源部分的
V4 都不会应答它。`hardware/test_firmware_board_profile_contract.py` 会在 `pk_board` 的代码里
出现 `SY6970` / `0x6A` / `PMIC` 时直接判红。

### 切到 v3

**方式一：menuconfig（推荐，交互式）**

```bash
cd firmware
./build.sh menuconfig
#   -> Pilot Kit Box
#     -> Expansion board profile (v4 (expansion-board-v4))  --->
#        ( ) v3 (expansion-board-v3, validated on V3.9)   <- 方向键选中，空格确认
#        (X) v4 (expansion-board-v4, validated on V4.3)
#   S 保存 -> Q 退出
./build.sh build
```

**方式二：直接改 sdkconfig（脚本 / CI 用，非交互）**

`sdkconfig` 在 `.gitignore` 里，改它只影响你本地：

```bash
cd firmware
sed -i '' 's/^# CONFIG_PK_BOARD_PROFILE_V3 is not set$/CONFIG_PK_BOARD_PROFILE_V3=y/' sdkconfig
sed -i '' 's/^CONFIG_PK_BOARD_PROFILE_V4=y$/# CONFIG_PK_BOARD_PROFILE_V4 is not set/' sdkconfig
./build.sh build
```

（Linux 上把 `sed -i ''` 换成 `sed -i`。）

**切回 v4** 就是把上面两条 `sed` 反过来，或在 menuconfig 里重新选 v4。

### 怎么确认这次编的是哪一版

**编译后、烧录前**——查生成的配置头，两行只会出现一行：

```bash
grep PK_BOARD_PROFILE firmware/build/config/sdkconfig.h
# v3 -> #define CONFIG_PK_BOARD_PROFILE_V3 1
# v4 -> #define CONFIG_PK_BOARD_PROFILE_V4 1
```

**烧录后**——开机串口日志里 `imu` 这一行直接把板型和安装四元数打出来：

```
I (xxxx) imu: board profile v3: q_body_fix = 0.7071068 0.0000000 0.7071068 0.0000000
I (xxxx) imu: board profile v4: q_body_fix = 0.5000000 0.5000000 0.5000000 -0.5000000
```

这两组数不一样，一眼就能看出烧进去的是哪一版。**换板子时先看这一行**，别靠记忆。

### 两版对称构建（发布 / CI 用）

不想动 `sdkconfig`、又要一次产出两个镜像时，用各自独立的 build 目录——
共用一个目录会留下上一版的 `.o`，症状是"改了却没生效"，很难查：

```bash
cd firmware
./build.sh -B build_v3 \
  -DSDKCONFIG_DEFAULTS="sdkconfig.defaults;sdkconfig.defaults.v3" \
  -DSDKCONFIG=build_v3/sdkconfig build

./build.sh -B build_v4 \
  -DSDKCONFIG_DEFAULTS="sdkconfig.defaults;sdkconfig.defaults.v4" \
  -DSDKCONFIG=build_v4/sdkconfig build
```

产物分别在 `build_v3/pilot_kit_box.bin` 和 `build_v4/pilot_kit_box.bin`。
烧录把 `build` 换成 `-p <端口> flash` 即可。

`sdkconfig.defaults` 本身**故意不写板型**，否则上面两个片段谁也覆盖不掉它；
`hardware/test_firmware_board_profile_contract.py` 会盯着这一点。

### 构建时也会打出来一次

configure 阶段（首次构建、以及每次 `menuconfig` / `sdkconfig` 变动后）会打印：

```
-- Pilot Kit: expansion board profile = v4 (expansion-board-v4)  (改：idf.py menuconfig -> ...)
```

加上开机日志那一行，人在场的两个时刻都能看见板型，不用靠"记得自己选过"。

### 想让某一版成为团队默认

把 `CONFIG_PK_BOARD_PROFILE_V3=y` 加进 `firmware/sdkconfig.defaults`（这个文件进 git），
然后删掉本地 `sdkconfig` 重新 `set-target`。当前 `sdkconfig.defaults` 里没写这一项，
所以走 Kconfig 的 `default`，也就是 **v4**。

---

## 2. 硬件目标 (P4 silicon revision)

| 配置项 | 默认 | 说明 |
|---|---|---|
| `CONFIG_IDF_TARGET` | `"esp32p4"` | 目标芯片，**绝对不要改** |
| `CONFIG_ESP32P4_SELECTS_REV_LESS_V3` | `y` | 选择支持 v0.x / v1.x silicon。当前 Waveshare ESP32-P4-WIFI6 出货的是 v1.3 silicon，必须 `y`。**如果未来你拿到了 ECO5 (v3.x) 的 Waveshare 板**，把这个改成 `n` 并把下面的 `REV_MIN_*` 改成 `300` 或 `301` |
| `CONFIG_ESP32P4_REV_MIN_100` | `y` | 最低支持 v1.0 silicon。配合上面那一项使用 |

### 二进制兼容性警告

**ESP32-P4 v1.x 和 v3.x 之间不二进制兼容**——硬件 bug 修复不同，启动序列不同。如果你的板子是 v3.x，必须改用 `CONFIG_ESP32P4_REV_MIN_300` 或 `_301`，并把 `SELECTS_REV_LESS_V3` 关掉，重新编译。

确认你的板子是哪个 revision：烧固件时 esptool 会打印：
```
Chip type:          ESP32-P4 (revision v1.3)
                                    ^^^^
```

---

## 3. 分区表与 Flash

| 配置项 | 默认 | 说明 |
|---|---|---|
| `CONFIG_ESPTOOLPY_FLASHSIZE_32MB` | `y` | Waveshare 板有 32 MB Nor flash |
| `CONFIG_ESPTOOLPY_FLASHSIZE` | `"32MB"` | 同上的字符串形式 |
| `CONFIG_PARTITION_TABLE_CUSTOM` | `y` | 用我们自己的 `partitions.csv` |
| `CONFIG_PARTITION_TABLE_CUSTOM_FILENAME` | `"partitions.csv"` | 文件名（相对 firmware 根目录） |

### partitions.csv 当前布局

```
# Name,    Type, SubType,  Offset,    Size,    Flags
nvs,       data, nvs,      0x9000,    0x6000,            ← 24 KiB Wi-Fi/BLE 配置
phy_init,  data, phy,      0xf000,    0x1000,            ← 4 KiB RF 校准
factory,   app,  factory,  0x10000,   0xc00000,          ← 12 MiB 主固件
storage,   data, spiffs,   ,          0xa00000,          ← 10 MiB LittleFS
```

总占用 ~22.5 MB / 32 MB，**剩余 ~9.5 MB 预留给未来 OTA pair**（A/B 分区双备份升级）。

12 MiB 的 `factory` 分区现在大半是余量：8 MB 的机型库已经搬到 microSD 卡上，app 镜像约 2.9 MB，只占分区的 23% 左右。

### 想加 OTA？

改 `firmware/partitions.csv`，把 `factory` 替换为 `ota_0` + `ota_1` + `otadata`，例：

```
nvs,       data, nvs,      0x9000,    0x6000,
otadata,   data, ota,      ,          0x2000,
phy_init,  data, phy,      ,          0x1000,
ota_0,     app,  ota_0,    ,          0x400000,
ota_1,     app,  ota_1,    ,          0x400000,
storage,   data, spiffs,   ,          0x800000,    ← 缩到 8 MiB 给 OTA 让位
```

---

## 4. ADS-B 接收链路（RP2040 扩展板）

1090 MHz 接收链位于 v3/v4 扩展板上：QPL9547 LNA + TA0970A SAW + AD8313
对数检波 + TLV3501 比较器把脉冲馈给板上 RP2040，RP2040 以 PIO+DMA 捕获
双沿、重建 56/112-bit Mode-S 帧，再经 UART2 以 921600 8N1 送 P4（P4 RX
GPIO46 ← RP2040 TXD @ J3-35，P4 TX GPIO32 → RP2040 RXD @ J3-31）。固件已
没有任何 RTL-SDR / USB host 接收配置：v1/v2 时代的 USB RTL-SDR 路径
（RTL2832U 驱动、IQ ring buffer、`PK_RTLSDR_*` 常量、`sdr`/`dsp` 任务对）
已从固件与组件树删除——退役任务的历史见
[`architecture-zh_CN.md`](architecture-zh_CN.md)。中心频率由板载 SAW 滤波
器固定；比较器门限与 RSSI 回读在 RP2040 侧（`firmware/rp2040/threshold_ctl.c`）。

---

## 5. 蓝牙 / BLE / ESP-Hosted

> ✅ **默认 `CONFIG_PK_BLE_ENABLED=y`，BLE 启动时初始化**。Bring-up 已经全链路打通，出厂状态固件会自动跑 `ble_gatt_init()`，板子上电就 advertising。
>
> **使用 BLE 的前提**：
> 1. 给 C6 烧 esp_hosted slave 固件（一次性，每块板做一次）— 见 [`docs/BUILD.md` §3](BUILD.md#3-新板首次设置烧-esp32-c6-hosted-slave-固件一次性) 或 [`docs/hardware/c6_slave_firmware.md`](hardware/c6_slave_firmware.md)
> 2. 编译 + 烧 P4 主固件
> 3. 上电
>
> **暂时不要 BLE？**（比如还没买 USB-UART 转接器、CI 跑、纯 ADS-B 数据路径开发）`idf.py menuconfig → Pilot Kit Box → [ ] Initialise BLE GATT server at boot`，或者直接改 `sdkconfig` 把 `CONFIG_PK_BLE_ENABLED` 设成 `n`。不关 BLE 又跳过 C6 烧录的话 P4 启动时会 `abort()`——vhci_drv.c 在 C6 不响应时硬 `ESP_ERROR_CHECK()`，没有 graceful degrade。
>
> **完全不要 BLE**？把 `CONFIG_BT_ENABLED` 也改成 `n` 可以再省 ~500 KiB flash。

| 配置项 | 默认 | 说明 |
|---|---|---|
| `CONFIG_PK_BLE_ENABLED` | `y` | **我们自己加的 Kconfig**。`y` 时 app_main 调 `ble_gatt_init()`（要求 C6 已经刷过 hosted slave 固件，见 BUILD.md §3）；`n` 时整条 NimBLE/hosted vhci 初始化跳过，固件在没烧 C6 的板子上也能稳定运行——但 BLE 功能不可用 |
| `CONFIG_BT_ENABLED` | `y` | 启用 BT 子系统（编进 NimBLE host）。即使 `PK_BLE_ENABLED=n` 也保持 `y`，因为关掉它会让 ble_gatt.c 编不过 |
| `CONFIG_BT_CONTROLLER_DISABLED` | `y` | P4 自身无原生 BT 控制器，要走 C6。**这个必须是 `y`** |
| `CONFIG_BT_NIMBLE_ENABLED` | `y` | 用 NimBLE host（不是 Bluedroid） |
| `CONFIG_BT_NIMBLE_TRANSPORT_UART` | **`n`** | **关键**：默认是 `y`，会让 NimBLE 在 GPIO 4/5 上找 UART HCI controller。我们要走 hosted VHCI 而不是 UART，所以必须显式 `n` |
| `CONFIG_BT_NIMBLE_ROLE_PERIPHERAL` | `y` | 我们做被连接端 |
| `CONFIG_BT_NIMBLE_ROLE_CENTRAL` | `y` | 启用 GATT client API（用来读 iOS 的 Current Time Service 同步时钟） |
| `CONFIG_BT_NIMBLE_ATT_PREFERRED_MTU` | `256` | 让 GDL90 traffic frame 一次发完不分片 |

### ESP-Hosted SDIO 引脚

针对 Waveshare ESP32-P4-WIFI6 的硬连线：

```
CONFIG_ESP_HOSTED_SDIO_HOST_INTERFACE=y
CONFIG_ESP_HOSTED_SDIO_SLOT_1=y
CONFIG_ESP_HOSTED_SDIO_4_BIT_BUS=y
CONFIG_ESP_HOSTED_SDIO_PIN_CLK=18
CONFIG_ESP_HOSTED_SDIO_PIN_CMD=19
CONFIG_ESP_HOSTED_SDIO_PIN_D0=14
CONFIG_ESP_HOSTED_SDIO_PIN_D1=15
CONFIG_ESP_HOSTED_SDIO_PIN_D2=16
CONFIG_ESP_HOSTED_SDIO_PIN_D3=17
CONFIG_ESP_HOSTED_SDIO_GPIO_RESET_SLAVE=54
CONFIG_ESP_HOSTED_SDIO_RESET_ACTIVE_HIGH=y
CONFIG_ESP_HOSTED_ENABLE_BT_NIMBLE=y
```

> ⚠️ **`RESET_ACTIVE_HIGH=y` 是 Waveshare 板的关键设置，不要随手改成 `ACTIVE_LOW`**。
> Waveshare ESP32-P4-WIFI6 PCB 上 P4-GPIO54 跟 C6-EN 之间有反相器/电平转换器，
> 从 P4 软件看 reset 是高有效（拉高时 C6 在 reset，拉低时 C6 在跑）。这点跟 C6 silicon
> 自身的低有效 EN 相反，也跟 Espressif 官方 ESP32-P4-Function-EV-Board 用的极性相反。
> 改错了 SDIO CMD5 会一直返回 `0x107 INVALID_RESPONSE`，C6 看起来 boot 了但其实
> 一直被 hold 在 reset 里。复位极性必须是高有效（`RESET_ACTIVE_HIGH`），不要改。

**改板子要换引脚**：menuconfig 里 Component config → ESP-Hosted config → SDIO Pin Configuration。

### ESP-Hosted 队列大小

默认 SDIO queue 是 20×1536 字节 per direction，约 47 KiB DMA-capable 内部 RAM per pool。在 ESP-Hosted constructor 早期启动阶段（在 `__libc_init_array()` 里跑、`main()` 之前），内部 RAM 还很碎片化，47 KiB 连续 64-byte aligned 块可能凑不出。

我们把队列缩到 **8**（我们只用 BLE 不用 Wi-Fi 远程，8 完全够）：

```
CONFIG_ESP_HOSTED_SDIO_TX_Q_SIZE=8
CONFIG_ESP_HOSTED_SDIO_RX_Q_SIZE=8
```

如果将来要走 Wi-Fi 高吞吐场景，可以试着提到 12 或 16，但需要同时增加 `CONFIG_SPIRAM_MALLOC_RESERVE_INTERNAL`。

### BLE 设备名

实际广播的名字在 `firmware/main/ble_gatt.c` 的 `on_sync()` 里运行时拼出来：

```c
#define BLE_DEVICE_NAME_PREFIX  "Pilot Kit Box"
/* 运行时拼成 "Pilot Kit Box-AABBCC"，AABBCC = C6 BLE MAC 后 3 字节大写 hex */
```

MAC 后缀来自 C6 模组的 efuse —— 同板跨重启稳定、跨板唯一。一个机库里多块板同时开机也能在 BLE scanner 里区分开。改名只需要改 prefix 一个宏，但要注意改完之后 adv packet 不能超 31 字节（flags 3 + name 总长 + 2 字节 header），prefix 自身建议 ≤ 22 字符。

### BLE GATT UUID

定义在 `firmware/main/ble_gatt.c` 顶部的 `s_svc_uuid` 等数组。**改 UUID 会让 Pilot Kit 移动 App 认不出来**，除非 App 也同步更新。详见 [`docs/ble_protocol.md`](ble_protocol.md) 第 3 节。

---

## 6. Own-ship 绑定

PFD 的 ALT / GS / VS 可以来自编译期配置的本机 ADS-B transponder，也可在
没有手动绑定时使用 GPS。本机 ICAO 通过 `CONFIG_PK_OWN_ICAO` 配置。
当前 4.3 寸触摸 UI 不提供旧 TARE 按钮的运行时绑定手势。需要固定本机
ICAO 时使用编译期 `CONFIG_PK_OWN_ICAO`；否则由 GPS 提供本机位置。

| 配置项 | 默认 | 说明 |
|---|---|---|
| `CONFIG_PK_OWN_ICAO` | `0x000000` | 24-bit ICAO 地址。非 0 时，PFD 会把匹配飞机的 ADS-B 高度、地速、垂直速度用于 ALT / GS / VS 显示。0 表示禁用编译期默认绑定 |
| `CONFIG_PK_OWN_STALE_AGE_MS` | `5000` | own-ship ADS-B 数据过期阈值。超过这个时间未收到匹配飞机的新数据后，PFD 对应读数回到 `---` |

### 演示模式（运行期开关，NVS）

设置页倒数第二行「演示模式」。**编译期没有对应的 Kconfig 选项**——它是纯运行期
状态，存在 NVS 里：

| 命名空间 | 键 | 类型 | 默认 |
|---|---|---|---|
| `pk_demo` | `demo_on` | `u8` | `0`（关） |

打开后，下面四个数据源 getter 直接返回 `demo_data.c` 的合成值，与硬件在不在
无关。接管点选在数据层而不是各页面，所以任何一页都不需要知道演示模式的存在：

| 入口 | 文件 |
|---|---|
| `pk_imu_sample_get()` | `imu_task.c` |
| `pk_gps_get()` | `gps_task.c`（本机解算 `pk_own_ship_resolve()` 因此一并被接管） |
| `pk_baro_get()` | `baro_task.c` |
| `aircraft_state_snapshot()` / `aircraft_state_get_own()` | `aircraft_state.c` |

合成目标**不进**真实融合表，因此不会流进 record_sink（落盘的 ts 日志仍然只有
真实报文），也不会污染 CPR 解码。GDL90 那一路在 `ble_gatt.c` 的发射任务里被
显式掐掉，理由见 [`ble_protocol-zh_CN.md`](ble_protocol-zh_CN.md) §6.5。

安全约束（三条，代码里都有对应断言性的注释）：默认关、只能从设置页显式打开、
开着时常驻标识不可关闭（顶栏红色 DEMO 徽标 + 整屏红框 + 开机横幅）。**不做
超时自动退出**——模式在用户不知情时自己变回去，比一直保持演示态更危险。

---

## 7. 存储 / LittleFS / MicroSD

文件后端在启动时读取 NVS 配置。选择 MicroSD 且卡已挂载时写
`/sdcard`，否则写 `/storage` LittleFS；选择了 MicroSD 但缺卡时会
回退 Flash。设置页 `LOG` 行切换后端，**重启后生效**。`FORMAT SD`
需要在 5 秒内再次按 UP 或 DOWN 确认，日志正在写卡时拒绝格式化。

定义在 `firmware/main/record_sink_file.c`：

```c
#define FILE_QUEUE_DEPTH    256                   /* 排队上限 */
#define FILE_ROTATE_BYTES   (1 * 1024 * 1024)    /* 每个文件 1 MiB */
#define FILE_KEEP_COUNT     12                   /* 文件数上限；实际受 10 MiB 分区限制 */
#define SD_ROTATE_BYTES     (16 * 1024 * 1024)   /* 每个文件 16 MiB */
#define SD_KEEP_COUNT       64                    /* 保留约 1 GiB */
```

调整后果：

| 改动 | 影响 |
|---|---|
| ↑ `FILE_QUEUE_DEPTH` | 短时高速写入时不丢数据，代价是 ~40B × N RAM |
| ↑ `FILE_ROTATE_BYTES` | 文件个数减少，每个文件更大；flash 擦除单位也更大 |
| ↑ `FILE_KEEP_COUNT` | 历史数据保留更久，总占用更大；实际保留量受 10 MiB 分区容量限制 |
| ↑ `SD_ROTATE_BYTES` / `SD_KEEP_COUNT` | MicroSD 单文件和总保留量增大；需要预留相应 FAT32 空间 |
| 改文件命名前缀 `FILE_NAME_PREFIX` | 要同步改 `Pilot-Kit/scripts/adsb_to_track.py` 的 glob，否则 Python 端找不到 |

MicroSD 使用 SDMMC Slot 0、4-bit 总线：

```text
CLK=GPIO43  CMD=GPIO44  D0..D3=GPIO39..42
```

板上没有独立 card-detect GPIO。`sd_detect` 任务在无卡时每 3 秒重试
挂载，挂载后每 2 秒探活并刷新容量。文件后端在一次启动内不会动态迁移：
日志写卡时拔卡后，需要重新插卡并重启，或把 LOG 改回 Flash 后重启。

---

## 8. 显示 / ST7701 MIPI-DSI

写死在 `firmware/main/display.h`：

```c
#define PK_DISPLAY_W                     800
#define PK_DISPLAY_H                     480
#define PK_LCD_PIN_RST                    27
#define PK_LCD_PIN_BL                     26
#define PK_LCD_PIN_BL_EN                  33
#define PK_LCD_DSI_LANE_COUNT             2
#define PK_LCD_DSI_LANE_BIT_RATE_MBPS     500
#define PK_LCD_DPI_CLOCK_MHZ              30
```

面板持续扫描原生 480×800 framebuffer。PPA 把应用侧 800×480
RGB565-swapped framebuffer 逆时针旋转 270°（等效顺时针 90°）、执行字节交换，并在 VSYNC
切换两个 DPI framebuffer。GPIO26 经反相 LEDC 注入 AP3032 FB 节点，
不能按普通正相背光处理。

---

## 9. IMU / BNO085

写死在 `firmware/main/imu_task.c`：

| 配置项 | 默认 | 说明 |
|---|---|---|
| `IMU_I2C_PORT` | `I2C_NUM_0` | 与 ES8311 codec 共享 I²C0 |
| `IMU_I2C_HZ` | `400000` | I²C fast mode (400 kHz) |
| `IMU_I2C_ADDR` | `0x4A` | 当前驱动只支持该地址；AD0 必须接 GND |
| `IMU_PIN_RST` | `28` | BNO085 RST 接 P4 GPIO28（J3 pin 16） |
| `IMU_PIN_INT` | `34` | J3 pin 28 = GPIO34（嘉立创 PCB 网络 IMU_INT）；当前轮询，未启用中断 |

### 报告速率

`bno_enable_rotation_vector()` 里：
```c
.report_interval_us  = 10000,    /* 100 Hz */
```

可以拉到 200 Hz (`5000` us) 或降到 30 Hz (`33333` us)。BNO085 内部 sensor fusion 最快约 400 Hz。

### 欧拉角约定

`quat_to_euler()` 实现的是 **ZYX Tait-Bryan**（航空标准），输出：
- `roll` (X 轴旋转): -180..+180，右翼下沉为正
- `pitch` (Y 轴旋转): -90..+90，机头上抬为正
- `yaw` (Z 轴旋转): 0..360，从上方看顺时针为正

### 安装变换 q_body_fix

**不再是 `imu_task.h` 里的一个写死常量**，而是按扩展板板系给出，见
[第 1 节](#1-扩展板板系-v3--v4)：

| 板型 | `q_body_fix` (w, x, y, z) | 芯片轴 → 机体轴 |
|---|---|---|
| v3（U4 贴 0°） | `0.7071068, 0, 0.7071068, 0` | +X→下、+Y→右、+Z→后 |
| v4（U4 贴 +90°） | `0.5, 0.5, 0.5, -0.5` | +X→右、+Y→上、+Z→后 |

机体系是航空 NED（+X 前 / +Y 右 / +Z 下）；两版都按盒子竖立、屏幕面向飞行员、
J1 排针边朝下安装。数值由 `firmware/main/pk_board.c` 从三段判据算出（原厂手册轴向、
PCB 实测封装角、装配朝向），不是手工标定值。

**别手改这两个值**。装配方式如果真的变了，改 `pk_board.c` 里对应的那一段判据，
然后跑 `firmware/test/test_pk_board_mount.c`——它从物理轴定义独立推导期望值，
改错会红。触摸“调平”只能笼住地平仪，不能代替轴向变换。

---

## 10. 触摸与电源

Rev1.2 只有 RESET、BOOT、POWER 三个板级按键，没有 MODE/TARE/UP/DOWN
应用按键。旧 `button_task.c` 只为 2.4 寸载板保留，且已从
`firmware/main/CMakeLists.txt` 移出、根本不参与编译——它写死的
GPIO26/GPIO23 在 Rev1.2 上是 LCD_BL_PWM 和 GT911 TP_RST。

当前 UI 使用 GT911 触摸：

- 点击 FAB 打开全屏导航网格（第 1 页：PFD、交通、地图、列表、搜索、记录、
  工具；第 2 页：诊断、设置、关于；记录/工具为置灰占位）；
- 长按并拖动 FAB 可改变位置，落点保存到 NVS；
- 长按网格动作条中“调平”一秒调用 `pk_imu_tare_persist()`；
- 详情页可用返回 FAB、标题栏返回或右滑。

Key3 POWER 短按开机、长按约两秒关机；Key1 RESET 重启 P4；Key2 BOOT
用于下载模式。当前触摸 UI 没有工厂重置 / DCD 擦除手势。

## 11. 日志输出

| 配置项 | 默认 | 说明 |
|---|---|---|
| `CONFIG_LOG_DEFAULT_LEVEL_INFO` | `y` | 默认输出 INFO 及以上 |
| `CONFIG_LOG_MAXIMUM_LEVEL_DEBUG` | `y` | 编译进 DEBUG 级别代码，运行时可动态开 |

### 关掉某模块 INFO 日志

代码里：
```c
esp_log_level_set("pfd", ESP_LOG_WARN);   /* 只看 W 以上 */
```

### 打开某模块 DEBUG 日志

```c
esp_log_level_set("adsb", ESP_LOG_DEBUG);
```

通常加在 `app_main()` 开头。

### TAG 列表（常用）

| TAG | 模块 |
|-----|---|
| `pilot_kit` | main.c 启动序列 |
| `sdr` | **已退役**（v1/v2 USB RTL-SDR 时代）：任务已删除，保留行作历史参考 |
| `dsp` | `adsb_link_task` 沿用的 TAG（日志检索连续）：RP2040 UART 链路 + 原 DSP 业务链 |
| `adsb` | adsb_link_task 每帧解码结果 |
| `rec_file` | LittleFS / MicroSD 文件 sink |
| `pk_sd` | MicroSD 挂载、插拔与格式化 |
| `gps` | GT-U8 NMEA/RMC 与卫星诊断；GPIO50 PPS 已被固件消费、用于 `time_locked` 判定（生产时间服务接线为后续任务） |
| `baro` | BMP388 压力、高度和升降率 |
| `record_sink` | sink 注册 |
| `ble_gatt` | NimBLE host + GATT |
| `display` | ST7701 MIPI-DSI + PPA 旋转 |
| `imu` | BNO085 驱动 |
| `pfd` | PFD 渲染 |

---

## 12. FreeRTOS 调度

| 配置项 | 默认 | 说明 |
|---|---|---|
| `CONFIG_FREERTOS_HZ` | `1000` | 1 ms tick |
| `CONFIG_ESP_MAIN_TASK_STACK_SIZE` | `4096` | `app_main()` 任务栈 |

### Task 优先级 (代码里硬编)

| Task | CPU | Prio | Stack | 文件 |
|---|-----|---|---|---|
| `usb_host_lib` | — | — | — | **已退役**（v1/v2 USB RTL-SDR 时代），保留行作历史参考 |
| `sdr_task` | — | — | — | **已退役**（v1/v2 USB RTL-SDR 时代）：RTL-SDR 控制 + IQ 生产者，保留行作历史参考 |
| `dsp_task` | — | — | — | **已退役**（v1/v2 USB RTL-SDR 时代）：职责移至 RP2040（`modes_edge`）+ `adsb_lnk` 链，保留行作历史参考 |
| `adsb_lnk` | 1 | 5 | 8 KiB | adsb_link_task.c（RP2040 UART 链路 921600 波特，承接原 DSP 业务链） |
| `imu_task` | 0 | 5 | 4 KiB | imu_task.c |
| `pfd_task` | 0 | 4 | 6 KiB | pfd.c |
| `rec_file_writer` | 0 | 3 | 4 KiB | record_sink_file.c |
| `gps` | 0 | 4 | 4 KiB | gps_task.c |
| `baro` | 0 | 4 | 4 KiB | baro_task.c |
| `sd_detect` | 0 | 2 | 4 KiB | pk_sdcard.c |
| `nimble_host` | 0 | 4 | 4 KiB | NimBLE 内部 |
| `ble_emit` | 0 | 3 | 6 KiB | ble_gatt.c |

详见 [`docs/architecture.md`](architecture.md) 任务表。

---

## 13. 编译优化

| 配置项 | 默认 | 说明 |
|---|---|---|
| `CONFIG_COMPILER_OPTIMIZATION_PERF` | `y` | -O2 优化（默认是 -Og debug 模式） |
| `CONFIG_COMPILER_WARN_WRITE_STRINGS` | `y` | `-Wwrite-strings` |

### Size-optimize 用于 release

如果你要塞 OTA 双分区，需要把固件大小压缩。试：

```
CONFIG_COMPILER_OPTIMIZATION_SIZE=y
# 取消 CONFIG_COMPILER_OPTIMIZATION_PERF
```

会用 -Os，固件大约小 10–15%，运行速度略慢但通常无感。

### 关 Bluetooth 省 ~500 KiB

如果你的板没有 C6，或者你不用 BLE：

```
CONFIG_BT_ENABLED=n
```

`pilot_kit_box.bin` 立即从 ~960 KiB 缩到 ~460 KiB，启动也快很多。代码里 `ble_gatt_init()` 会直接 `ESP_ERR_NOT_SUPPORTED` 返回，文件 + 串口 sink 照常工作。

### ccache 加速

```bash
brew install ccache    # macOS
sudo apt install ccache    # Linux
```

激活 ESP-IDF 后：
```bash
export IDF_CCACHE_ENABLE=1
```

加进 `~/.zshrc` 永久生效。改一两个文件后增量编译从 30 秒压到 5 秒。

---

## 14. 改完配置之后

任何 sdkconfig 改动后：

```bash
idf.py build              # 增量编译（多数情况）
# 如果 build 出错，强制重 configure：
idf.py reconfigure
idf.py build
```

对于影响**分区表**的改动（比如换 partitions.csv），第一次烧之前要：
```bash
idf.py -p <PORT> erase-flash   # 抹掉 flash
idf.py -p <PORT> flash
```

对于影响**bootloader**的改动（比如 silicon revision、flash size），同样需要 erase-flash + flash 完整序列。

---

## 15. 想加新配置项？

如果你写了一个新模块，希望让它的某个行为通过 menuconfig 配置：

1. 在 `firmware/main/` 建一个 `Kconfig.projbuild` 文件
2. 写 menuconfig 选项：
   ```
   menu "Pilot Kit Box"
       config PK_FOO_BAR
           int "Foo bar limit"
           default 42
           help
               Bla bla bla
   endmenu
   ```
3. 代码里用：
   ```c
   #include "sdkconfig.h"
   #if CONFIG_PK_FOO_BAR > 100
   ...
   #endif
   ```
4. 把推荐默认值加进 `sdkconfig.defaults`：
   ```
   CONFIG_PK_FOO_BAR=42
   ```

参考 ESP-IDF 任意 component 的 `Kconfig.projbuild` 即可。
