naizhao/Pilot-Kit-Box-ESP32-P4/docs/ux/box-4.3-ux-spec.html

# Pilot Kit Box · 4.3″ UX 设计稿

硬件：微雪 ESP32-P4-WIFI6-Touch-LCD-4.3（480×800 原生竖屏 → PPA 旋转 90° 为 800×480 横屏，GT911 五点电容触摸）
交互：无物理按键（deep sleep 取消 · 板载 POWER 为硬件开关）· 全触摸 · FAB 点击打开全屏导航网格
框架：LVGL v9 + esp_lvgl_adapter（PPA 旋转 / 防撕裂）· 最终目标屏 5″ 800×480 半反半透，同分辨率可 1:1 迁移
版本：v2（物理尺寸修订版）· 2026-07-27 · v2.1 修订 2026-08-02：① 横向 dock 在 800×480 上溢出 41 px， 改为全屏导航网格（§3 / §3.5 / §11 / §13 / §14 已重画，原委见 §3 的宽度账）； ② 顶栏按实现重画：●GPS ●REC ●BLE 🔋 那套圆点字符版式早已作废， 现在是图标化状态栏（新增 §2.1），且这条状态栏只有 PFD 页有，其余各页顶栏各画各的

#### ⚠️ 第一步：校准显示器（必做一次，结果自动保存）

拖动滑块 1.00× 重置

拿一张真实的信用卡 / 身份证贴到下面这个方框上，拖动滑块直到完全重合。 校准后本页所有设备图都是真实物理大小。
原因：CSS 的 mm 单位固定按 96 px/inch 换算， 而你的屏幕是 3008×1692 高分屏 —— 未校准时图会显示成实际的 38%~75%。

信用卡 / 身份证85.6 × 54.0 mm

本文件全部按真实毫米绘制，不是像素。 完成上方校准后，屏幕上看到的就是实际大小。
关键事实：4.3″ 横屏物理仅 93.7 × 56.2 mm（信用卡 85.6 × 54 mm）， 而 217 PPI 比旧 2.4″ 屏的 167 PPI 还高 30% —— 同样像素数在新屏上物理更小。分辨率提升只带来清晰度，不带来空间。

## 0 · 三块屏物理对照

屏 | 分辨率 | 物理尺寸 | 像素密度 | 16px 汉字实际
旧 2.4″（迁移前） | 320×240 | 48.8 × 36.6 mm | 6.56 px/mm · 167 PPI | 2.44 mm
新 4.3″（已下单） | 800×480 | 93.7 × 56.2 mm | 8.54 px/mm · 217 PPI | 1.87 mm ⚠
终 5″ 半反半透 | 800×480 | 108.9 × 65.3 mm | 7.35 px/mm · 187 PPI | 2.18 mm

## 1 · 字号阶梯（硬约束，实现时照抄）

级别 | 物理 | 4.3″ | 5″ | 用途 | 实样
XL | 5.0 mm | 43 px | 37 px | PFD 当前值 | 23225
L | 3.5 mm | 30 px | 26 px | 页面标题 | 交通雷达
M | 3.0 mm | 26 px | 22 px | 正文主力 | 呼号 CES5432
S | 2.5 mm | 21 px | 18 px | 标签 / 单位 / 状态栏 | HDG 359°
XS | 2.1 mm | 18 px | 16 px | 硬下限，仅极次要 | IIR coef15

参照：旧屏 16×16 汉字 = 2.44 mm → 新屏需 21 px 才等大； 旧屏 8×8 汉字 = 1.22 mm → 新屏仅 10 px，此尺寸永久禁用。
低于 18 px（2.1 mm）的字号一律不得出现在设计中。

## 2 · PFD 主页（默认 · 菜单未开）

HDG 359° 17 6 REC 88°C 87%

450400350 300

378

700 km/h

⊣ ▪ ⊢

236002340023200 23000

23225

VS +1408

☰

信用卡 85.6 × 54 mm

← 供尺寸对比

顶栏 5.6mm(48px) · 主区 25mm(214px)：速度带 11.7mm(100px) ｜ 姿态 70.3mm(600px) ｜ 高度带 11.7mm(100px) · 底部 HSI 16.4mm(140px)。姿态区刻意留空。

## 2.1 · 顶栏状态栏（真源 pfd_statusbar.c）

圆点字符版式（HDG · ●GPS ●REC ●BLE 🔋 · ADSB 计数）已作废，2026-08-02 按实现重画。
圆点只说得出"有 / 没有"，说不出"几颗星""几架飞机"；而 ADSB / REC 这类字母缩写在 26px 字号下一项就吃掉 60~90px。 实现早已改成图标 + 读数：图标提供语义（孤立的 100% 看不出是电量还是亮度），数字提供读数，二者同色成为一体。
图标取自 Material Symbols Rounded（Google，Apache-2.0），经 gen_pfd_icons.py 生成 30×30px / 4bpp 灰度字形表（pfd_icon_font.h），与文字共用同一条 alpha 混合路径（pk_aa_blit_4bpp），边缘处理完全一致。 本稿内为等尺寸近似示意。顶栏文字是 M 档 26px，不是 S 档。

### 满载态 —— 所有状态位同时点亮（实拍 images/ui-4.3-pfd.png）

HDG 082° 17 6 REC 88°C 100%

几何（pfd_layout.h）：条高 48px · 左边距 12px · 右边距 16px · 图标与自己的数值间隙 2px · 组内 8px（PFD_BAR_GAP_LABEL，蓝牙与电量同属"设备自身状态"，用近距不用词距）· 词组之间 16px（PFD_BAR_GAP_WORD）。
左端 HDG 与右端蓝牙 / 电量常驻，永不隐藏；右段按最坏宽度（两个图标 + 100%）预留，蓝牙一断开中段也不会整排平移 —— 顶栏元素位置必须稳定，否则每次扫视都要重新找目标在哪。
温度这一格只在超温时出现，色是警示橙不是红（红留给 NO FIX / REC / 低电这类"已经出事"）； 阈值 CONFIG_PK_SOC_TEMP_WARN_C 当前 85℃ 触发 / 78℃ 解除（7℃ 滞回，免得那一格出现又消失，把飞行员训练成忽略它）。 读的是 SoC 结温（soc_temp.c），不是 BMP388 那颗测座舱环境温度的传感器 —— 暴晒时二者能差二三十度。 实拍里显示 78℃ 是模拟器强制点亮的 mock 值。

### 全空态 —— 出厂开机、什么都还没连上（实拍 images/empty-4.3-pfd.png）

HDG ---° NO FIX 0 100%

无航向 → ---° 灰（灰是本项目里"数据失效"的专用色，有效读数绝不能用灰）· 无定位 → NO FIX 红 · 目标数 0 仍是绿（0 是个有效读数，不是失效）· REC / 温度 / 蓝牙整枚不画（不是画成灰的占位）· 电量照常显示 —— 电池焊在板上，没有"没接"这一说。
中段是在"左端 HDG 之后、右段之前"的剩余空间里居中的，所以 REC / 温度出现或消失时中段会整体重新居中（比较上下两图即可看出）。

### 演示模式 —— 右端常驻 DEMO 徽标（实拍 images/demo-4.3-pfd.png）

HDG 082° 17 6 REC 88°C 100% ⚠ 演示

徽标 96 × 32px，画在 LVGL 控件层、压在各页之上。高度取 32 而不是整条 48：它是浮在顶栏上的一枚 chip，铺满整条会读成"顶栏本身变红了"。
各页把自己右对齐内容的右界报给 pk_ui_topbar_right_limit() 统一裁，中段跟着一起退 —— 顶栏本来就有一套"装不下就按优先级丢"的机制，把新的可用宽度告诉它就够了，不必每页各写一个 if (demo) x -= 112。

### 电量的三个形态

100%

常态白（航电惯例 白 = 正常 / 仅供参考；绿留给需要主动确认有效的读数：航向、星数、目标数）
<25% 转警示橙

3%

≤6% 转红并同时换成 alert 图标（电池内嵌感叹号）—— 阈值正是九档刻度里 alert 那一档的覆盖范围，变红与换图标同时发生，不各走各的。实拍 ui-4.3-battery-low.png

45%

充电：frame_1…6 → frame_full 逐帧动画，300ms 一帧、整周期 2.1s；颜色一律白。实拍 ui-4.3-charging.png

为什么电池是九档连续刻度而不是三档空壳 —— battery_android 系列排成 alert → _0…_6 → full 九档， step = (pct×8+50)/100 一次线性映射，形态本身就是读数。此前的 battery_horiz_* 只有 000/050/075 三档， 20% 与 4% 渲染成同一个空壳、只能靠颜色区分。末档取 full 而不是 _6：_6 内部还留着一条黑， 拿它当 100% 会一直显示成"还差一格"，最容易被误当成故障。
为什么充电用动画而不是静态闪电 —— 闪电只说明"接了电"，动画才说明"电真的在进"。 每帧 300ms（整周期 2.1s）而不是手机上常见的 200ms：座舱里任何接近 1Hz 的动效都会被余光当成告警去抓一下注意力，而充电是最不需要被注意的状态。 相位由 uptime_ms 算而不是数渲染帧 —— 固件与模拟器帧率不同，数帧会让同一段动画快慢不一。

### 槽位与降级

段 | 槽位 | 图标（Material 名） | 内容与颜色 | 数据来源
左（常驻） | HDG | 无，青色 HDG 文字标签 | 082° 绿；无航向 ---° 灰 | pk_own_heading_resolve()：ADS-B 绑定机 > IMU yaw > GPS track(≥2kt)
中 ① | 卫星 | satellite_alt | 星数 绿；无 fix NO FIX 红 | pk_gps_get()
中 ② | ADS-B 目标数 | connecting_airports 画的是两架飞机：后面跟的是"周围有 N 架"，要的是复数语义 | 计数 绿 | aircraft_state_snapshot()，60s 新鲜窗
中 ③ | 录制 | fiber_manual_record | REC 红，仅正在写记录时出现 | rec_active
中 ④ | 温度 | thermometer_alert 温度计 + 感叹号，比通用三角贴切 | 88°C 警示橙，仅超温时出现 | pk_soc_temp_get()
右（常驻） | 蓝牙 | bluetooth | 只有图标、没有文字（符号本身即可表意），青；未连接则整枚不画 | ble_gatt_is_connected()
右（常驻） | 电量 | battery_android_*（唯一 FILL=0 的一枚） | 见上 | pk_batt_get()

中段优先级 GPS > ADSB > REC > TEMP，依据是"不知道会出事"的程度：定位丢失直接影响本机位置与授时；周围有几架飞机是本产品的核心输出； "以为在录、其实没录"是本产品最难受的失败；超温对应"Garmin 高温死机时的备份"这一定位。
装不下就从最低优先级那端整项丢弃（不是缩字号、不是截断），GPS 永不丢。中段能放多少完全取决于面板宽度 —— 320 屏只剩约 130px（一项），800 屏有 500px 上下（四项）；与其为每种屏手算一套坐标，不如声明优先级后让代码自己裁，以后新增状态位也不必重新推导布局。
左端 HDG 与右端蓝牙 / 电量不参与降级 —— 后两者是「设备自身」的状态而非「飞行」的状态。

这条状态栏只有 PFD 页有。其余整屏页面各画各的顶栏（同高 48px、标题同为 M 档）： 交通 = 标题 + HDG + 目标数 + 朝向 / 量程 · 空管看板 = 标题 + 目标数 + 排序说明 + RESET（非默认排序才出现）· 地图 = 标题 + 右上角瓦片层级 Z12 · 设置 / 诊断 / 关于只有左上角一个标题 · 诊断子系统详情页顶上是 LVGL 的 ← 诊断 backbar（一枚胶囊，不是整条顶栏），子系统名画在内容区第一行 · 罗盘校准向导是全屏页，没有顶栏。
导航网格与 Toast 压在当前页之上，露出的是底页自己的顶栏 —— 下面 §3 那两屏底页是 PFD，所以顶上是这条状态栏。

## 3 · PFD 主页（FAB 打开全屏导航网格 · 第 1 页）

HDG 359° 17 6 REC 88°C 87%

450400350 300

378

700 km/h

⊣ ▪ ⊢

236002340023200 23000

23225

VS +1408

PFD

交通

地图

列表

搜索

记录

工具

调平屏幕亮度关闭

顶栏 5.6mm(48px) 不遮罩，露出底页自己的顶栏（这里底页是 PFD，故仍是 §2.1 那条状态栏：星数 / 目标数 / REC / 温度 / 蓝牙 / 电量，菜单期间也要能看状态）· 网格 4 列 × 2 行，格 23.4 × 18.3mm(200 × 156px)， 远超 44px 触摸下限 · 每格 = 64px 图标 + 3.0mm(26px) 标签，整组在格内垂直居中 · 分页点 y=368、1.4mm(12px)，仅状态指示不可点 · 动作条 10.3mm(88px) 三等分：调平（警示橙，唯一会改变仪表状态的动作）｜屏幕亮度｜关闭。
底页压暗 232/255 → 保留 9.4% 原亮度：地平线的明暗分界仍隐约可辨，飞行员不会在菜单打开的这两秒里失去姿态参照， 但白底黑字的高度带 / 速度带不再能读出内容（初版 210 保留 18%，实测那些白框仍是抢眼的浅色矩形）。
打开即藏 FAB：网格铺满全屏且命中判定排在 LVGL 之前，FAB 留着就是"自己点不动、又盖住底下的格"，何况它可拖动、挡住哪一格不可预测。 出口写在屏上。三条退路：① 动作条「关闭」② 第 1 页继续右滑 ③ 6 s 无操作自动收起（真机走查后由 5 s 调大：网格内容比 dock 多，5 s 不够看完）。
三条动作文案复用现有 catalog 词条不另立（PK_TR_ACT_LEVEL / PK_TR_SETTINGS_BRIGHTNESS / PK_TR_SEARCH_CLOSE）； 图标为 Material Symbols Outlined 64px 墨迹（gen_nav_icons.py 生成，cell 68px），本稿内为等尺寸近似示意。

为什么不是横向 dock（2026-08-02 改版的由来，删掉这段下一个人就会重新提议做 dock）
初版这里是一条从 FAB 那侧滑出的横向 dock：N 个导航页签 × 94px｜分隔线｜动作区「调平」。它在 800×480 上排不下 —— 按已删除的 pk_ui_nav.c :: dock_width() 算：
7 个页签 × 94 ＋ 分隔 8 ＋ 分隔线 1 ＋ 动作区 94 = 761 px
FAB 吸右后可用宽度 = 800 − (16 边距 + 56 FAB + 8 呼吸) = 720 px
左侧溢出 41 px：真机截图里最左那个页签渲染出来是「FD」。 第 8 项（搜索）根本进不来，而页签已经窄到 94px；再缩窄就跌破 44px 触摸下限，换行则是"横向 dock"这个形态本身不成立。
一级页面已从 6 涨到 7（新增地图页），另有「记录」「工具」两个占位 —— 数量只会继续涨， 而网格再加项只是多一页，不再有"排不下"这回事。方案 A / C 两版全屏网格原型经评审，方案 C 拍板（4×2 + 底部动作条 + 分页）。

### 第 2 页（3 项 · 末页刻意不居中）

HDG 359° 17 6 REC 88°C 87%

450400350 300

378

700 km/h

⊣ ▪ ⊢

236002340023200 23000

23225

VS +1408

诊断

设置

关于

调平屏幕亮度关闭

切分点是常用度，不是塞满页面：第 1 页放飞行中会用的 7 项（PFD / 交通 / 地图 / 列表 / 搜索 / 记录 / 工具），第 8 格留作余量； 第 2 页放地面才碰的 3 项（诊断 / 设置 / 关于）—— 飞行中最常按的几个不该为了凑满一页而往后挪。
格子位置钉死，末页不居中：位置一旦随项数浮动，同一个功能在两页上就落在不同坐标，手指记不住位置 —— 而"记得住位置"正是网格相对列表的全部优势。空就空着。
「记录」「工具」置灰占位（页面尚未实现）：不从版面拿掉，将来补上时版面一个数都不用改。 点了不弹提示 —— 命中判定直接把它们排除，置灰视觉本身就是信号。
翻页只能滑（分页点不可点）：阈值 60px(≈7mm) 且横向位移须 > 2× 纵向；过阈值当场翻不等松手，一次长滑可连翻多页。 第 1 页继续右滑 = 关闭（延到松手才结算）；末页继续左滑不做事，也不循环回第 1 页。

### 亮度快调 pop（点动作条「屏幕亮度」弹出）

低中高

面板 46.9 × 9.8mm(400 × 84px)，按钮 14.1 × 7.5mm(120 × 64px)×3
四边留白同一个 pad = 10px（初版把面板底边钉死、按钮顶边从另一头反推，得到上 10 下 20 的不对称）
面板底边离动作条 12px，压在第 2 行格子上；档位真值取自 pk_backlight_step_get()，与设置页同源不分家
pop 打开期间网格再压一档（120/255）且整层不可点 —— 看得见的必须是点得中的；动作条不压暗（「屏幕亮度」正高亮着，压掉它等于抹去"是我弹出来的"这条线索）
点面板外 = 收起 pop，不关网格

## 3.5 · 导航结构与返回规则

无物理按键 = 没有系统级返回。 二级页面若不设计返回，用户进去就出不来。 本节定义全部转场与返回路径，实现时必须逐条覆盖。

##### 一级页面（7 个）

- PFD 主页
- 交通雷达
- 地图
- 空管看板
- 诊断
- 设置
- 关于

互相平级 · 只能通过 FAB → 全屏导航网格切换
FAB 图标 = ☰
（另有「记录」「工具」两格置灰占位）

##### 模态层（铺满全屏，压在某一页之上）

- 导航网格
- 搜索
- 机场详情
- 键盘编辑器

不是一级页面的一站，不改当前在哪一页
打开即藏 FAB，出口写在自己屏上
优先级由 pk_ui_modal_top() 单点决定

##### 二级页面（全屏，替换一级）

- 诊断 → 子系统详情 ×8 IMU/BARO/GPS/SDR/BLE/LOG/CLK/SYS

FAB 图标变 ←（返回）
顶栏左侧同时出现「← 诊断」按钮

##### 覆盖层（不替换一级）

- 看板 → 目标详情抽屉
- 设置 → 格式化确认框
- 任意页 → 校准向导（自动弹出）
- 任意页 → Toast（2s 自动消失）

各自带关闭按钮 + 点外部区域关闭

所在位置 | 返回方式（三选一，任一可用） | 返回目标
一级页面 | —（已是顶层，FAB 打开全屏导航网格切换） | —
全屏导航网格 | ① 动作条「关闭」 ② 第 1 页继续右滑 ③ 6s 无操作自动收起 | 打开它之前的那一页
子系统详情页 | ① 顶栏左侧「← 诊断」按钮 ② FAB（此时为 ←） ③ 右滑手势 | 诊断总览
目标详情抽屉 | ① 抽屉内「关闭」 ② 点抽屉上方列表区 ③ 下滑手势 | 看板页（保留选中行）
格式化确认框 | ① 「取消」 ② 点遮罩 ③ 5s 超时自动取消 | 设置页
校准向导 | ① 「稍后再说」 ② acc≥2 自动退出 | 进入前的页面
特例：目标详情抽屉的「绑定为本机」是跨层跳转 —— 执行后关闭抽屉并直接跳到 PFD（让飞行员立刻看到以新 own-ship 为基准的地平线），不返回看板页

设计原则：层级最多 2 层，不做返回栈 —— 二级页面只可能从诊断进入，返回目标唯一确定。
FAB 双重身份：一级页面 = ☰（打开全屏导航网格）；二级页面 = ←（返回）。位置固定不变， 用户只需记住"右下角那个圆钮"一个位置。二级页面不提供导航网格，要切主页面须先返回 —— 层级清晰， 也避免"在 GPS 详情页切到 PFD 再回来"的状态混乱。
网格打开期间 FAB 是隐藏的，所以它不承担"再点一次收起"这个角色（那是 dock 时代的收起方式）—— 出口一律走上表那三条。

## 4 · 交通雷达页

交通 HDG 359° 12 航向朝上 20NM

20

13

6

CES5432FL235▲

CCA1234FL180▼

CSN8801FL290—

JAL772FL310▲

↗CES54328.2nm

FL235 ▲1408450kt

←CCA123412.4nm

FL180 ▼800380kt

↓CSN880115.1nm

FL290 —460kt

↖JAL77218.7nm

FL310 ▲200480kt

☰

左雷达 60.9mm(520px) 圆直径约 44mm · 右栏 32.8mm(280px) 放 4 张卡片，可垂直滑动 · 双指捏合切量程 10/20/40 NM。

飞机图标（本次修订） —— 原三角形丢失了航向信息，改为飞机俯视剪影：
· 本机（黄色，6.5mm）：机头朝上模式下机头恒指向屏幕上方；正北朝上模式下按当前航向旋转。两种模式由设置页「地图朝向」切换。
· 目标（3.8mm）：按各自 ADS-B track 航向旋转 —— 一眼能看出对方是迎面而来还是同向飞行，这是三角形给不了的信息。图中四架分别为 212° / 85° / −8° / 135°。
· 颜色仍为 ■ 威胁 / ■ 一般；换半反半透屏后改用填充样式区分（见待办）。
· 罗盘刻度环随朝向模式旋转；本机符号始终位于圆心。

## 5 · 空管看板页（7 列 × 7 行）

航空器 12 排序 距离↑ RESET

向呼号距离高度 升降速度航向

↗CES54328.2 nmFL235▲1408450072°

←CCA123412.4 nmFL180▼800380265°

↓CSN880115.1 nmFL290—460188°

↖JAL77218.7 nmFL310▲200480315°

→HDA61522.3 nmFL270—442091°

↙CPA90325.8 nmFL350▲600495221°

↑CSZ924128.0 nmFL160▼1200340003°

☰

行高 5.6mm(48px)、字 2.5mm(21px)、一屏 7 行、可垂直滑动。已砍掉「机型」「SQK」两列（26px 字宽下 9 列会挤到每列 3 字符），二者移入详情抽屉。红底 = 威胁。

## 6 · 目标详情抽屉（点击行后滑入）

航空器 12 排序 距离↑ RESET

向呼号距离高度 升降速度航向

↗CES54328.2 nmFL235▲1408450072°

←CCA123412.4 nmFL180▼800380265°

#### CCA1234 · 中国国际航空

B737-800 · B-5432 · ICAO 780C1E · SQK 3216 · 中国

方位 / 距离← 265° / 12.4nm

气压高度FL180

垂直率▼800 fpm

地速380 kt

关闭绑定为本机

抽屉高 27mm(230px)，保留上方 2 行列表可见 · 机型 / SQK / ICAO / 航司 等被砍掉的列在此完整展示 · 「绑定为本机」沿用现有 own-ship 逻辑（绑定后自动跳回 PFD）。

## 7 · 设置页（7 行满屏 + 滚动）

设置

语言中文EN

QNH−1013.2+

地图朝向机头上正北上

雷达量程102040

屏幕亮度低中高自动

配色夜间日间

记录存储FlashSD卡

☰

行高 7.5mm(64px) · 控件按钮高 4.4mm(38px) · 第 8 项「格式化 SD」需滚动可见 · 格式化保留现有两步确认状态机（首次点击变「再点确认 5s」，超时复位；无卡 / 正写时置灰）。

## 8 · 诊断页（2×4，每卡一行核心值）

诊断

IMU

acc 3/3 · 100 Hz

BARO

23225 ft · +1408

GPS

3D · 17 星 · PPS ✓

SDR

12 目标 · 42 帧/s

BLE

已连 1 · ↑12.4 KB/s

LOG

SD 4.2 MB · 丢 0

CLK

GPS · −12 ms

SYS

68 ℃ · 堆 1.8 MB

☰

每卡 10.8mm 高，只放标题 + 一行核心值（物理空间不允许三行密排）· 点卡片进入该子系统详情页（下节）· SYS 卡含芯片温度（对应「Garmin 高温死机」的产品定位）： 超温时 PFD 顶栏中段多出「温度计 + 结温」一格，警示橙、不是红，阈值 CONFIG_PK_SOC_TEMP_WARN_C 当前 85℃ 触发 / 78℃ 解除（见 §2.1；本稿早先写的 ">75℃ 弹红色警告" 与实现不符，已订正）。

## 8.1 · GPS 详情页（点卡片进入）

诊断详情必须保留现有全部深度。 现有 diag_page.c 的 GPS 段做得很细 —— fix/HDOP、可见星、天线状态、经纬度、以及每个星座单独一行的 SNR 柱状图。 这正是排查 no-fix 的关键（不能只盯 fix=0，要看 SNR 和天线）。 800×480 下这些内容不再需要挤，反而能全部同屏。

←诊断

GPS · ATGM336H

定位状态3D FIX

可见卫星17 颗

HDOP0.9

天线OK

PPS 秒脉冲✓ 1 Hz

授时偏差−12 ms

纬度+22.54321°

经度+114.05678°

GNSS 高度128 ft

各星座信噪比（SNR dB-Hz）· ≥40 好 25~39 中 <25 弱

GPS 8 颗

BDS 6 颗

GLO 2 颗

GAL 1 颗

←

星座名 + SNR 柱状图完整保留（draw_snr_row() 的逻辑直接搬进 lv_canvas）· 柱高按 SNR 值、颜色按强弱分档 · 星座多时本页可垂直滚动 · 左上「←」返回诊断总览。IMU 详情页同理展示 cal N/3 + roll/pitch/yaw + 四元数 + 采样率； BARO 详情页展示 hPa / alt / VS / 温度 / QNH / IIR 系数。

## 9 · 关于页（纯静态身份）

关于

✈

Pilot Kit Box

v0.9.0 · a1b2c3d

air.club

构建2026-07-27 18:42

ESP-IDFv6.0.1

LVGLv9.2

主板ESP32-P4-WIFI6-4.3

主控ESP32-P4NRW32 32MB

无线ESP32-C6-MINI

传感器BNO085·BMP388·ATGM336H

☰

纯静态身份：logo / 版本 / 构建 / 依赖 / 硬件型号（不带在线状态灯）+ 二维码。所有 ✓ 状态、校准精度、实时数值全在诊断页，两页零重复。

## 10 · 罗盘校准向导（自动进入 / 自动退出）

罗盘校准

缓慢画 ∞ 字，约 10 秒

质量 2/3

稍后再说

acc=0 持续触发自动进入、acc≥2 持续自动退出（沿用现有逻辑）· 「稍后再说」为新增 —— 原靠 MODE 键关闭，按键删除后若不补此按钮，用户在磁干扰环境下会被永久卡在本页 · 点击后本次开机不再自动弹出（重启复位）· 本页刻意不放 FAB · 本页是全屏页，没有顶栏（cal_wizard.c 自己清整屏、标题居中）。

## 11 · 调平 LEVEL 四态（全屏导航网格的动作条最左一格）

下面四格为实际尺寸：动作条三等分，每格 31.2 × 10.3mm(266 × 88px)。 调平与导航格物理分离（隔着分页点那一条），误触把地平线归零的路被堵死 —— 飞行中那是要命的。

调平

① 待机（警示橙）

调平

② 短按 → 只弹提示
按钮本身不变，见下图

0.6s

③ 按住，橙色填充走满 1s
松手 / 滑出即取消

✓ 已调平

④ 绿闪 + toast
随即收起网格

### 短按提示（防止用户误以为按钮失灵）

HDG 359° 17 6 REC 88°C 87%

450400350 300

378

700 km/h

⊣ ▪ ⊢

236002340023200 23000

23225

VS +1408

PFD

交通

地图

列表

搜索

记录

工具

调平屏幕亮度关闭

长按 1 秒调平地平仪

短按不执行动作，只弹 toast 说明用法 —— 否则用户点一下没反应会认为按钮坏了。 toast 停留 2 秒淡出，屏幕正中、画在控件层最前面（菜单打开时弹出的提示也必须看得见，不能被网格盖住）。 文案随语言切换（中「长按 1 秒调平地平仪」/ 英「Hold 1 s to level the horizon」），已入 i18n_catalog.py。
长按满 1 s 当场执行（提示随即弹出），网格留到松手才收起 —— 手指还按着就把网格关掉的话， 这一次按压的剩余帧会落到底下那一页上（底页是地图时，手一松就跳进机场详情页）。

## 12 · 设计 token

天空渐变（近→远） | rgb(35,145,235) → rgb(15,70,140) 经 pk_pfd_rgb565_dither() 4×4 抖动消色阶
地面渐变（近→远） | rgb(170,125,80) → rgb(95,65,35) 褐色。早期依据实物照片推测为蓝紫有误，已按 pfd_attitude.c 源码校正
本机符号 | #ffe14d
青（标签/分隔/方位） | #5ee0e8
威胁 / 一般目标 | #ff5555 · #ffd23f
上升 / 下降 | #3fe08a · #ff9b5a
选中 / FAB · HSI 指针 · 警告 | #2e6df0 · #ff3fd0 · #ffb43f
选中格底 / 置灰项 | #122244（--sel 压到约 20% 明度）· #3d4d6b（比 --dim 再暗一档）
顶栏 / HSI / 网格动作条 / FAB | 5.6mm(48px) / 16.4mm(140px) / 10.3mm(88px) / 6.6mm(56px)⌀
顶栏文字 / 状态位图标 cell / 词组间距 | 3.0mm(26px，M 档) / 3.51mm(30px，墨迹 27px) / 1.87mm(16px)，图标↔自己的数值 0.23mm(2px)
状态位配色 | #00dc3c 有效在线 · #ff503c NO FIX/REC/低电 · #ffb43f 超温/<25% 电量 · #46dcfa 标签与蓝牙 · #ffffff 电量常态 · #646464 数据失效（灰是失效专用色，有效读数绝不用灰）
网格格 / 格内图标 / 分页点 | 23.4 × 18.3mm(200 × 156px) / 7.5mm(64px) / 1.4mm(12px)，点距 3.0mm(26px)
菜单遮罩 / pop 二次遮罩 | 232/255（保留 9.4%）/ 120/255（保留 53%）· 顶栏与动作条不遮
速度带 / 高度带 / 姿态区 | 11.7mm(100px) / 11.7mm(100px) / 70.3mm(600px)
看板行高 / 设置行高 / 触摸下限 | 5.6mm(48px) / 7.5mm(64px) / ≥5.2mm(44px)

## 13 · LVGL 落点（现有代码复用情况）

设计元素 | LVGL 实现 | 现有代码
PFD 姿态仪 | lv_canvas | ✅ pfd_attitude.c
速度带 / 高度带 | lv_canvas | ✅ pfd_tape.c / pfd_speed_tape.c
HSI + 交通叠加 | lv_canvas | ✅ pfd_hsi.c / pfd_hsi_traffic.c
交通雷达 | lv_canvas | ✅ traffic_page.c / traffic_geom.c
顶部状态栏 | 不用 LVGL，直接在 RGB565 framebuffer 上手绘 | ✅ pfd_statusbar.c / pfd_statusbar_icons.c 图标与文字共用 pk_aa_blit_4bpp 这一条 alpha 混合路径，走 LVGL 控件树就得让二者各走各的渲染器
FAB / 返回栏（← 诊断）/ DEMO 徽标 | lv_button + lv_anim · lv_obj | 新增（pk_ui_nav.c）
全屏导航网格 | 不用 LVGL 对象树，直接在 RGB565 framebuffer 上手绘 | 新增 nav_grid_page.c 一层全屏 = 800×480×2 = 768 KB 绘制表面，而 CONFIG_LV_MEM_SIZE_KILOBYTES=64 —— 分配不出这么大一块 layer，失败时 LV_OS_NONE 下是裸忙等，单线程 LVGL 当场死锁
雷达右栏 / 看板 / 抽屉 | flex + 内建滚动 · lv_anim | 数据层复用 aircraft_state.c / adsb_list.c
分段控件 / 步进器 | lv_buttonmatrix · lv_button×2 | ✅ settings_page.c / config_qnh.c
格式化两步确认 | lv_msgbox | ✅ pk_settings_format_action()
TARE 长按进度 | LV_EVENT_LONG_PRESSED_REPEAT + lv_bar | ✅ pk_imu_tare_yaw()
校准 8 字动画 / 质量条 | lv_canvas + lv_timer · lv_bar | ✅ cal_wizard.c 双纽线
Toast | lv_obj + lv_anim | ✅ pk_ui_toast_show/get
雷达双指缩放 | LV_EVENT_GESTURE / 自定义 indev | 新增（GT911 五点）
字体 | lv_font_conv 子集，5 档字号 | 5 套自研字体（200KB）全部退休 i18n catalog 机制保留

## 14 · FAB 可拖动 + 位置记忆

与 Pilot Kit App 的可拖动悬浮按钮保持一致的操作手感。四个吸附位示意（同一屏，仅 FAB 位置不同）：

PFD拖动前

☰

交互规则
· 长按 200 ms 进入拖动态（避免与点击冲突），FAB 半透明 + 亮边 + 阴影加重
不能用 transform_scale 做"微放大"：那会让 LVGL 走 TRANSFORM layer，64 KB 池分配不出整块 buffer，单线程 LVGL 死在忙等里
· 拖动中实时跟手，垂直位置自由
· 松手后水平吸附到最近的左 / 右边缘（不允许悬在中间遮挡内容）
· 位置存 NVS：fab_side(L/R) + fab_y(0~100%)，重启保留
· 导航网格是全屏的，不随 FAB 那一侧翻转（"展开方向跟着 FAB 反向铺开"是 dock 时代才需要的规则，已作废）
· 打开网格即隐藏 FAB：它可拖动，挡住哪一格不可预测
· 校准页不显示 FAB，避免误导

## 15 · 术语：TARE → LEVEL / 调平（已定）

你的类比很准 —— 「上飞机后把罗盘物理拨杆往外拔」，那个动作在航空术语里叫 caging（笼锁）。 而 TARE 来自称重行业的「去皮」，飞行员并不熟悉。现有实现也确实是 cage 语义 （pfd_attitude.c 只 cage 横滚 / 俯仰，航向解耦）。

方案 | 英文 | 中文 | 说明
✅ A（已采用） | LEVEL | 调平 | 现代 EFIS 通用叫法（Dynon SkyView 即为 Level）；「调平」直观、2 字，动作条一格放得下
B | CAGE | 锁定 / 笼锁 | 最贴合传统陀螺仪，老飞行员一看就懂；但年轻用户可能陌生，中文「锁定」易误解为锁死
C | ZERO | 归零 | 最直白；但「归零」在航向语境下有歧义（本功能不动航向）
D | TARE | 校零 | 维持现状，代码零改动；但术语与航空语境脱节

✅ 已采用方案 A，本稿动作条与四态图均已替换为「调平」。 涉及改动：i18n_catalog.py 加词条 → 重跑 gen_i18n_assets.py 生成字形 （否则中文渲染成 ?）· 动作条一格 800/3 = 266px 宽度按最终字数复核： 最长的一条是「屏幕亮度」中文 4 字 × 32 = 128px、英文 BRIGHTNESS 10 字 × 21 = 210px，都摆得下。

## 16 · 预览校准说明（防止实施时吃不准）

本稿绘制单位 | 毫米（mm），非像素。所有 .scr 容器 = 93.7 × 56.2 mm
换算基准 | 800 px = 93.7 mm → 1 px = 0.1171 mm · 8.54 px/mm · 217 PPI
为何需要校准 | CSS 规范固定 1mm = 3.7795 CSS px（96 px/inch），与真实显示器 DPI 无关。 高分屏上不校准会显示成实际的 38%~75%
设计者显示器 | 3008 × 1692 逻辑分辨率（2026-07-27 记录）
对应缩放系数 | 14″ 约 2.64× · 16″ 约 2.31× · 24″ 约 1.50× · 27″ 约 1.33×
校准方法 | 页首滑块 + 信用卡实测（85.6 × 54.0 mm），结果存 localStorage['pkbox-cal']
实施时以什么为准 | 以像素值为准（表格中括号内数字），mm 仅用于人眼校验尺度感。 例：正文 26 px、看板行高 48 px、网格格 200 × 156 px、动作条高 88 px

## 17 · 待办（未定稿）

· 半反半透日间模式配色 —— 目标屏反射态对比度仅 7:1、色域 16.5%，红/黄可能难分辨， 威胁等级需改为「形状 + 亮度」编码，本稿纯色方案届时出第二套
· 诊断页 2×4 八卡（每卡一行）vs 2×3 六卡（每卡两行）—— 待定
· Toast 样式 / 启动画面 / 爱好者「地面观测模式」入口 —— 不影响架构，实现阶段边做边定
· 5″ 半反半透屏的 TN 视角（θL60/θR50/θU60/θD60 @CR>2）→ 整机安装角度必须正对飞行员
