naizhao/Pilot-Kit-Box-ESP32-P4/images/README-zh_CN.md

# 图片资源

英文版：[`README.md`](README.md)

## 4.3″ 触摸屏 UI（`ui-4.3-*.png`）

由模拟器渲染，**与真机逐像素一致** —— 模拟器编译的就是固件里那批绘制模块
（`firmware/main/pfd_*.c`、`pk_ui_nav.c`），不是另画一份效果图。

全部 800×480，与面板逻辑分辨率相同，可直接用于 README 与官网。

| 图 | 场景 |
|---|---|
| PFD 主页 | **PFD 主页**。姿态仪、左右速度/高度带、底部 HSI 罗盘与交通目标叠加、左右各三行信息 |
| 二级页面 | **二级页面**：顶栏「← 诊断」，FAB 同时变 ← |
| Toast | **Toast** 提示，压在所有控件之上 |
| 低电量 | **低电量**：电池图标转 alert 并与数值一同变红 |
| 充电中 | **充电中**：电池播放逐帧动画 |
| 交通页 | **交通页正常态**：360° 雷达 + 右侧目标列表 |
| 看板 | **看板正常态**：八列表格，含威胁行高亮与徽章 |
| 诊断 | **诊断总览正常态**：八张子系统卡片全绿 |
| 设置 | **设置页底部**：演示模式那一行（关） |
| 开机画面 | **开机画面**（演示模式关） |

## 演示模式（`demo-4.3-*.png`）

演示模式把四路数据源整体换成合成值，用于没接外设时在真机上核对正常态。
它的安全底线是「开着就一定看得见」，而标识画在控件层、与各页的绘制代码互不
相干 —— **唯一能证明「每一页都在」的办法就是每一页都截一张**。少截一页，就是
那一页可能没有标识而没人知道。中英各一版：徽标挤在顶栏右端，各页要给它让出
宽度，而英文文案比中文长得多。

| 图 | 场景 |
|---|---|
| PFD PFD 英文 | **PFD**：顶栏右端红底 ⚠ 演示徽标 + 整屏红框；状态位整组左移让位 |
| 交通 交通英文 | **交通页**：朝向/量程左移 |
| 看板 看板英文 | **看板**：排序说明与 RESET 左移 |
| 诊断 诊断英文 | **诊断**：顶栏只有左上角标题，无需让位 |
| 设置 设置英文 | **设置页**：演示模式开关处于「开」，小字提示转红 |
| 开机 开机英文 | **开机画面**：底部红色横幅。真机上这一屏早于 LVGL，只有横幅没有徽标；模拟器把两者一起画出来了 |

### 重新生成

```bash
python3 sim/capture.py            # 全部
python3 sim/capture.py --only dock  # 只出 dock 相关
```

UI 改动后重跑一次，再用 `git diff --stat images/` 看哪些场景受影响 —— 没变的
图 git 不会记录，变了的一眼可见，等于一套轻量的视觉回归。

场景定义在 `sim/capture.py` 的 `SCENES` 表里，每一项就是一组模拟器环境变量。

> **PFD 主页没有中英两版**：那一屏全是国际通用的符号、数字与固定缩写
> （HDG / KM/H / ALT / VS），一个 i18n 词条都没有，两种语言渲染逐字节相同。
> 这与 ICAO 标准仪表不做本地化一致 —— 语言只影响导航与设置这类文字界面。

## 2.4″ 版本与硬件（其余文件）

`PFD.jpg` / `radar-traffic.jpg` / `adsb-list.jpg` 是 2.4″ 版本的**实拍**照片；
`pcb-*` / `3d-case-*` / `assemble*` 是硬件与装配图。
