naizhao/Pilot-Kit-Box-ESP32-P4/hardware/expansion-board-v3/CHECKLIST.md

# V3.11 BOM Verification Checklist (reference-designator order)

Chinese companion: [`CHECKLIST-zh_CN.md`](CHECKLIST-zh_CN.md)

> Generated from the authoritative schematic and PCB coordinates. Do not hand-edit.
> `Not placed` is authoritative: DNP parts, test pads, solder bridges, mounting holes, and PCB antennas do not receive components.

178 designators in total.

| ✓ | Designator | Value / Model | Footprint | Position (x, y) | Stage | Notes |
|---|---|---|---|---|---|---|
| ☐ | **C1** | 10uF | C_0805_2012Metric | (78.6, 93.3) | A Power |  |
| ☐ | **C2** | 1uF | C_0603_1608Metric | (62.0, 98.3) | A Power |  |
| ☐ | **C3** | 1uF | C_0603_1608Metric | (66.5, 98.3) | A Power |  |
| ☐ | **C4** | 1uF | C_0603_1608Metric | (71.0, 98.3) | A Power |  |
| ☐ | **C5** | 1uF | C_0402_1005Metric | (109.6, 79.2) | A Power |  |
| ☐ | **C6** | 1uF | C_0603_1608Metric | (78.6, 67.0) | A Power | Board silkscreen reads C18; use coordinates |
| ☐ | **C10** | 100nF | C_0603_1608Metric | (66.4, 84.5) | C Sensors + GNSS |  |
| ☐ | **C11** | 100nF | C_0603_1608Metric | (70.6, 84.5) | C Sensors + GNSS |  |
| ☐ | **C12** | 100nF | C_0603_1608Metric | (74.8, 84.5) | C Sensors + GNSS |  |
| ☐ | **C13** | 100nF | C_0603_1608Metric | (79.1, 84.5) | C Sensors + GNSS |  |
| ☐ | **C14** | 100nF | C_0603_1608Metric | (61.8, 87.2) | C Sensors + GNSS |  |
| ☐ | **C15** | 4.7uF | C_0603_1608Metric | (66.1, 87.2) | C Sensors + GNSS |  |
| ☐ | **C16** | 100nF | C_0603_1608Metric | (70.4, 87.2) | C Sensors + GNSS |  |
| ☐ | **C17** | 100nF | C_0603_1608Metric | (78.5, 61.4) | C Sensors + GNSS |  |
| ☐ | **C18** | 10uF | C_0805_2012Metric | (78.9, 64.6) | C Sensors + GNSS | Board silkscreen reads C6; use coordinates |
| ☐ | **C19** | 15pF C0G | C_0603_1608Metric | (104.6, 87.7) | B MCU + Flash |  |
| ☐ | **C20** | 15pF C0G | C_0603_1608Metric | (107.6, 87.7) | B MCU + Flash |  |
| ☐ | **C21** | 100pF | C_0402_1005Metric | (101.0, 67.5) | E 1090 Receive Chain |  |
| ☐ | **C22** | 100nF | C_0603_1608Metric | (95.7, 95.2) | B MCU + Flash |  |
| ☐ | **C23** | 100nF | C_0603_1608Metric | (99.8, 95.2) | B MCU + Flash |  |
| ☐ | **C24** | 100nF | C_0603_1608Metric | (103.8, 95.2) | B MCU + Flash |  |
| ☐ | **C25** | 100nF | C_0603_1608Metric | (109.2, 77.4) | B MCU + Flash | Board silkscreen reads R33; use coordinates |
| ☐ | **C26** | 100nF | C_0603_1608Metric | (107.8, 95.2) | B MCU + Flash |  |
| ☐ | **C27** | 100nF | C_0603_1608Metric | (111.9, 95.2) | B MCU + Flash |  |
| ☐ | **C28** | 1uF | C_0603_1608Metric | (86.5, 87.7) | B MCU + Flash |  |
| ☐ | **C29** | 1uF | C_0603_1608Metric | (89.5, 87.7) | B MCU + Flash |  |
| ☐ | **C30** | 100pF | C_0402_1005Metric | (120.4, 62.1) | E 1090 Receive Chain | Board silkscreen reads L14; use coordinates |
| ☐ | **C31** | 100pF C0G | C_0402_1005Metric | (106.0, 71.2) | E 1090 Receive Chain |  |
| ☐ | **C32** | 100pF C0G | C_0402_1005Metric | (114.5, 71.2) | E 1090 Receive Chain |  |
| ☐ | **C33** | 100pF C0G | C_0402_1005Metric | (120.9, 71.2) | E 1090 Receive Chain |  |
| ☐ | **C34** | 100pF C0G | C_0402_1005Metric | (129.4, 71.2) | E 1090 Receive Chain |  |
| ☐ | **C35** | 100pF C0G | C_0402_1005Metric | (141.2, 71.2) | E 1090 Receive Chain |  |
| ☐ | **C36** | 100pF | C_0402_1005Metric | (103.0, 66.5) | E 1090 Receive Chain |  |
| ☐ | **C37** | 100nF | C_0402_1005Metric | (109.6, 85.0) | E 1090 Receive Chain |  |
| ☐ | **C38** | 100pF | C_0402_1005Metric | (137.3, 69.2) | E 1090 Receive Chain |  |
| ☐ | **C39** | 100pF | C_0402_1005Metric | (140.0, 83.6) | D 978 Transceiver |  |
| ☐ | **C40** | 3.6pF | C_0402_1005Metric | (123.6, 76.3) | D 978 Transceiver |  |
| ☐ | **C41** | 2.7pF | C_0402_1005Metric | (126.9, 76.3) | D 978 Transceiver |  |
| ☐ | **C42** | 6.2pF | C_0402_1005Metric | (130.2, 76.3) | D 978 Transceiver |  |
| ☐ | **C43** | 3pF | C_0402_1005Metric | (137.6, 78.3) | D 978 Transceiver |  |
| ☐ | **C44** | 3.6pF | C_0402_1005Metric | (121.7, 78.0) | D 978 Transceiver |  |
| ☐ | **C45** | 100pF | C_0402_1005Metric | (119.2, 84.3) | D 978 Transceiver |  |
| ☐ | **C46** | 3pF | C_0603_1608Metric | (118.7, 86.2) | E 1090 Receive Chain | Board silkscreen reads C47; use coordinates |
| ☐ | **C47** | 200pF | C_0603_1608Metric | (118.7, 88.4) | E 1090 Receive Chain | Board silkscreen reads C46; use coordinates |
| ☐ | **C48** | 1uF | C_0402_1005Metric | (99.6, 65.5) | E 1090 Receive Chain |  |
| ☐ | **C49** | 100nF | C_0603_1608Metric | (55.6, 80.1) | E 1090 Receive Chain |  |
| ☐ | **C51** | 1nF | C_0603_1608Metric | (55.6, 85.2) | E 1090 Receive Chain |  |
| ☐ | **C52** | 100nF | C_0402_1005Metric | (60.4, 96.2) | E 1090 Receive Chain |  |
| ☐ | **C53** | 100pF | C_0402_1005Metric | (110.2, 61.2) | E 1090 Receive Chain |  |
| ☐ | **C54** | 100pF | C_0402_1005Metric | (105.3, 68.1) | E 1090 Receive Chain |  |
| ☐ | **C55** | 100pF | C_0603_1608Metric | (90.2, 74.0) | E 1090 Receive Chain |  |
| ☐ | **C56** | 100pF | C_0603_1608Metric | (85.1, 74.0) | E 1090 Receive Chain |  |
| ☐ | **C57** | 100pF | C_0402_1005Metric | (63.4, 63.3) | C Sensors + GNSS |  |
| ☐ | **C58** | 100pF | C_0402_1005Metric | (56.5, 64.6) | C Sensors + GNSS |  |
| ☐ | **C59** | 100pF | C_0402_1005Metric | (56.3, 62.4) | C Sensors + GNSS |  |
| ☐ | **C60** | 22uF | C_0805_2012Metric | (136.2, 93.1) | D 978 Transceiver |  |
| ☐ | **C61** | 100nF | C_0603_1608Metric | (121.2, 97.0) | D 978 Transceiver |  |
| ☐ | **C62** | 100nF | C_0603_1608Metric | (125.1, 97.0) | D 978 Transceiver |  |
| ☐ | **C63** | 100nF | C_0603_1608Metric | (129.0, 97.0) | D 978 Transceiver |  |
| ☐ | **C64** | 100nF | C_0603_1608Metric | (132.9, 97.0) | D 978 Transceiver |  |
| ☐ | **C65** | 100nF | C_0603_1608Metric | (136.8, 97.0) | D 978 Transceiver |  |
| ☐ | **C66** | 22uF | C_0805_2012Metric | (123.2, 100.5) | D 978 Transceiver |  |
| ☐ | **C67** | 1uF | C_0603_1608Metric | (126.9, 93.1) | D 978 Transceiver |  |
| ☐ | **C68** | 18pF | C_0603_1608Metric | (123.1, 93.8) | D 978 Transceiver |  |
| ☐ | **C69** | 18pF | C_0603_1608Metric | (127.7, 100.5) | D 978 Transceiver |  |
| ☐ | **C81** | 470pF C0G | C_0402_1005Metric | (118.6, 73.5) | E 1090 Receive Chain |  |
| ☐ | **C82** | 100nF | C_0402_1005Metric | (83.0, 84.5) | B MCU + Flash |  |
| ☐ | **C83** | 100nF | C_0402_1005Metric | (93.6, 79.5) | B MCU + Flash |  |
| ☐ | **C84** | 1uF | C_0402_1005Metric | (93.6, 82.0) | B MCU + Flash |  |
| ☐ | **C85** | 100nF | C_0402_1005Metric | (96.0, 79.5) | B MCU + Flash |  |
| ☐ | **C86** | 100nF | C_0402_1005Metric | (96.0, 82.0) | B MCU + Flash |  |
| ☐ | **C87** | 10nF C0G | C_0603_1608Metric | (97.8, 84.4) | B MCU + Flash |  |
| ☐ | **R1** | 10k | R_0603_1608Metric | (79.0, 87.2) | C Sensors + GNSS |  |
| ☐ | **R2** | 4.7k | R_0603_1608Metric | (61.4, 106.1) | C Sensors + GNSS |  |
| ☐ | **R3** | 4.7k | R_0603_1608Metric | (61.4, 108.7) | C Sensors + GNSS |  |
| ☐ | **R4** | 1k | R_0603_1608Metric | (110.6, 87.7) | B MCU + Flash |  |
| ☐ | **R5** | 10k | R_0603_1608Metric | (95.7, 98.3) | B MCU + Flash |  |
| ☐ | **R6** | 10k | R_0603_1608Metric | (99.8, 98.3) | B MCU + Flash |  |
| ☐ | **R7** | 5.1k | R_0603_1608Metric | (103.8, 98.3) | B MCU + Flash |  |
| ☐ | **R8** | 5.1k | R_0603_1608Metric | (107.8, 98.3) | B MCU + Flash |  |
| ☐ | **R9** | 27R | R_0603_1608Metric | (92.5, 87.7) | B MCU + Flash |  |
| ☐ | **R10** | 27R | R_0603_1608Metric | (95.6, 87.7) | B MCU + Flash |  |
| ☐ | **R11** | 3.32k | R_0402_1005Metric | (98.8, 68.0) | E 1090 Receive Chain |  |
| ☐ | **R17** | 10k | R_0603_1608Metric | (121.4, 105.2) | D 978 Transceiver |  |
| ☐ | **R18** | 10k | R_0603_1608Metric | (136.2, 62.1) | E 1090 Receive Chain |  |
| ☐ | **R19** | 52.3R | R_0402_1005Metric | (138.5, 71.2) | E 1090 Receive Chain |  |
| ☐ | **R21** | 0R | R_0603_1608Metric | (115.2, 85.0) | E 1090 Receive Chain |  |
| ☐ | **R22** | 0R | R_0603_1608Metric | (87.5, 71.2) | E 1090 Receive Chain |  |
| ☐ | **R23** | 0R | R_0603_1608Metric | (91.4, 71.2) | E 1090 Receive Chain |  |
| — | **R24** | 0R DNP(旁路外接) | R_0402_1005Metric | (112.7, 66.0) | **Not placed** (DNP) |  |
| — | **R25** | 0R DNP(旁路板载) | R_0402_1005Metric | (114.8, 66.0) | **Not placed** (DNP) |  |
| ☐ | **R26** | 10k | R_0603_1608Metric | (58.8, 76.4) | C Sensors + GNSS |  |
| ☐ | **R27** | 10k | R_0603_1608Metric | (61.8, 73.3) | C Sensors + GNSS |  |
| — | **R30** | 1k DNP | R_0402_1005Metric | (108.0, 66.6) | **Not placed** (DNP) |  |
| ☐ | **R31** | 1k | R_0603_1608Metric | (115.0, 87.3) | E 1090 Receive Chain |  |
| ☐ | **R32** | 10k | R_0603_1608Metric | (112.5, 75.2) | E 1090 Receive Chain |  |
| ☐ | **R33** | 100k | R_0603_1608Metric | (108.7, 75.2) | E 1090 Receive Chain | Board silkscreen reads C25; use coordinates |
| ☐ | **R34** | 10k | R_0603_1608Metric | (55.6, 77.5) | E 1090 Receive Chain |  |
| ☐ | **R35** | 10k | R_0603_1608Metric | (55.6, 82.6) | E 1090 Receive Chain |  |
| — | **R36** | 1k DNP | R_0603_1608Metric | (61.4, 103.5) | **Not placed** (DNP) |  |
| ☐ | **R47** | 10k | R_0603_1608Metric | (132.5, 85.0) | D 978 Transceiver |  |
| ☐ | **R50** | 10k | R_0603_1608Metric | (94.0, 85.2) | B MCU + Flash |  |
| ☐ | **R51** | 10k | R_0603_1608Metric | (96.0, 85.2) | B MCU + Flash |  |
| ☐ | **R52** | 10k | R_0402_1005Metric | (60.0, 83.0) | C Sensors + GNSS |  |
| ☐ | **R53** | 10k | R_0402_1005Metric | (63.0, 84.4) | C Sensors + GNSS |  |
| ☐ | **R54** | 10R | R_0402_1005Metric | (109.6, 82.1) | E 1090 Receive Chain |  |
| ☐ | **R55** | 10k | R_0603_1608Metric | (59.1, 80.3) | C Sensors + GNSS |  |
| ☐ | **R56** | 10k | R_0603_1608Metric | (132.3, 89.7) | D 978 Transceiver |  |
| ☐ | **R57** | 33R | R_0603_1608Metric | (85.7, 95.3) | E 1090 Receive Chain |  |
| ☐ | **L1** | 18nH 0402CS-18NXGRW | L_0402_1005Metric | (105.5, 69.8) | E 1090 Receive Chain |  |
| ☐ | **L2** | 33nH | L_0402_1005Metric | (61.8, 64.8) | C Sensors + GNSS |  |
| ☐ | **L7** | 6.8uH | L_0805_2012Metric | (131.5, 93.1) | D 978 Transceiver |  |
| ☐ | **L8** | 100nH | L_0402_1005Metric | (142.6, 87.0) | D 978 Transceiver |  |
| ☐ | **L9** | 7.5nH | L_0402_1005Metric | (124.2, 78.0) | D 978 Transceiver |  |
| ☐ | **L10** | 27nH | L_0402_1005Metric | (120.8, 76.3) | D 978 Transceiver |  |
| ☐ | **L11** | 6.8nH | L_0402_1005Metric | (134.2, 76.3) | D 978 Transceiver |  |
| ☐ | **L12** | 6.8nH | L_0402_1005Metric | (137.6, 76.3) | D 978 Transceiver |  |
| ☐ | **L13** | 7.5nH | L_0402_1005Metric | (119.2, 83.2) | D 978 Transceiver |  |
| ☐ | **L14** | 100nH | L_0402_1005Metric | (120.4, 63.3) | E 1090 Receive Chain | Board silkscreen reads C30; use coordinates |
| ☐ | **L15** | 33nH | L_0402_1005Metric | (58.0, 67.6) | C Sensors + GNSS |  |
| ☐ | **D1** | B5819W | D_SOD-123 | (97.8, 91.3) | B MCU + Flash | Polarized; follow the cathode marking |
| ☐ | **D2** | TPESD8L3.3 0.3pFtyp 0.5pFmax | D_0402_1005Metric | (128.3, 62.1) | E 1090 Receive Chain | Polarized; follow the cathode marking |
| ☐ | **D3** | TPESD8L3.3 0.3pFtyp 0.5pFmax | D_0402_1005Metric | (140.0, 86.9) | D 978 Transceiver | Polarized; follow the cathode marking |
| ☐ | **D4** | TPESD8L3.3 0.3pFtyp 0.5pFmax | D_0402_1005Metric | (60.0, 90.4) | B MCU + Flash | Bidirectional low-capacitance USB ESD protector; no polarity |
| ☐ | **D5** | TPESD8L3.3 0.3pFtyp 0.5pFmax | D_0402_1005Metric | (60.0, 93.6) | B MCU + Flash | Bidirectional low-capacitance USB ESD protector; no polarity |
| ☐ | **F2** | 6V/200mA | Fuse_0805_2012Metric | (129.8, 105.2) | D 978 Transceiver |  |
| ☐ | **F3** | 6V/200mA | Fuse_0805_2012Metric | (140.2, 62.1) | E 1090 Receive Chain |  |
| ☐ | **F4** | 6V/200mA | Fuse_0805_2012Metric | (61.8, 67.4) | C Sensors + GNSS |  |
| ☐ | **F5** | 6V/200mA | Fuse_0805_2012Metric | (56.4, 69.7) | C Sensors + GNSS |  |
| ☐ | **Q2** | AO3401A | SOT-23 | (125.1, 105.2) | D 978 Transceiver |  |
| ☐ | **Q3** | AO3401A | SOT-23 | (132.0, 62.1) | E 1090 Receive Chain |  |
| ☐ | **Q4** | AO3401A | SOT-23 | (61.8, 70.2) | C Sensors + GNSS |  |
| ☐ | **Q5** | AO3401A | SOT-23 | (57.8, 72.6) | C Sensors + GNSS |  |
| ☐ | **U1** | ME6211C33M5 | SOT-23-5 | (69.4, 93.3) | A Power | Observe pin 1 / signal direction |
| ☐ | **U2** | TPS7A2033PDBVR | SOT-23-5 | (63.1, 93.3) | A Power | Observe pin 1 / signal direction |
| ☐ | **U3** | TPS7A2033PDBVR | SOT-23-5 | (74.3, 93.3) | A Power | Observe pin 1 / signal direction |
| ☐ | **U4** | BNO085 | BNO085_LGA-28 | (63.7, 78.3) | C Sensors + GNSS | Observe pin 1 / signal direction |
| ☐ | **U5** | BMP388 | BMP388_LGA-10 | (71.3, 81.2) | C Sensors + GNSS | Observe pin 1 / signal direction |
| ☐ | **U6** | QMC5883P | LGA-16_3x3mm_P0.5mm | (71.3, 77.0) | C Sensors + GNSS | Observe pin 1 / signal direction |
| ☐ | **U7** | ATGM336H-6N-74 | ATGM336H_LCC-18 | (70.4, 66.4) | C Sensors + GNSS | Observe pin 1 / signal direction |
| ☐ | **U8** | RP2040 | QFN-56-1EP_7x7mm_P0.4m | (88.4, 80.5) | B MCU + Flash | Observe pin 1 / signal direction |
| ☐ | **U9** | W25Q128JVSIQ | SOIC-8_5.3x5.3mm_P1.27 | (103.4, 82.1) | B MCU + Flash | Observe pin 1 / signal direction |
| ☐ | **U10** | CC1312R1F3RGZR | QFN-48-1EP_7x7mm_P0.5m | (126.2, 85.0) | D 978 Transceiver | Observe pin 1 / signal direction |
| ☐ | **U11** | QPL9547TR7 | DFN-8-1EP_2x2mm_P0.5mm | (101.6, 71.2) | E 1090 Receive Chain | Observe pin 1 / signal direction |
| ☐ | **U12** | BGA2817 | SOT-363_SC-70-6 | (117.7, 71.2) | E 1090 Receive Chain | Observe pin 1 / signal direction |
| ☐ | **U14** | AD8313ARMZ | MSOP-8_3x3mm_P0.65mm | (114.1, 82.1) | E 1090 Receive Chain | Observe pin 1 / signal direction |
| ☐ | **U15** | TLV3501(TOKMAS) | SOT-23-6 | (83.1, 91.3) | E 1090 Receive Chain | Observe pin 1 / signal direction |
| ☐ | **U16** | XA17-G4K | SOT-363_SC-70-6 | (114.6, 62.1) | E 1090 Receive Chain | Observe pin 1 / signal direction |
| ☐ | **U17** | XA17-G4K | SOT-363_SC-70-6 | (58.8, 63.3) | C Sensors + GNSS | Observe pin 1 / signal direction |
| ☐ | **FL1** | TA0970A | TA0970A_SMD3838-6 | (110.2, 71.2) | E 1090 Receive Chain | See the Chinese companion for the detailed engineering note |
| ☐ | **FL2** | TA0970A | TA0970A_SMD3838-6 | (125.1, 71.2) | E 1090 Receive Chain | See the Chinese companion for the detailed engineering note |
| ☐ | **Y1** | 12MHz CL=10pF ABM8-272-T3 | Crystal_SMD_3225-4Pin_ | (100.4, 87.7) | B MCU + Flash | Passive crystal; 180-degree rotation is electrically equivalent |
| ☐ | **Y2** | 48MHz ABM8W-7pF | Crystal_SMD_3225-4Pin_ | (133.8, 81.7) | D 978 Transceiver | Passive crystal; 180-degree rotation is electrically equivalent |
| ☐ | **Y3** | 32.768kHz FC-135 | Crystal_SMD_3215-2Pin_ | (122.7, 91.3) | D 978 Transceiver |  |
| ☐ | **J1** | J3_HAT_2x20_SMD排针 | PinHeader_2x20_P2.54mm | (92.6, 106.3) | F External Interface |  |
| ☐ | **J2** | U.FL_GNSS_EXT(经尾线转SMA) | U.FL_Hirose_U.FL-R-SMT | (52.9, 74.1) | C Sensors + GNSS |  |
| ☐ | **J4** | USB-C_16P | USB_C_Receptacle_HRO_T | (53.5, 92.0) | B MCU + Flash |  |
| ☐ | **J5** | U.FL_978 | U.FL_Hirose_U.FL-R-SMT | (145.5, 83.5) | D 978 Transceiver |  |
| ☐ | **J6** | U.FL_1090_EXT(经尾线转SMA) | U.FL_Hirose_U.FL-R-SMT | (124.3, 62.1) | E 1090 Receive Chain |  |
| ☐ | **J7** | U.FL_IFA_TEST(π后调试口) | U.FL_Hirose_U.FL-R-SMT | (103.1, 61.3) | E 1090 Receive Chain |  |
| ☐ | **J8** | U.FL→内置patch | U.FL_Hirose_U.FL-R-SMT | (52.9, 64.4) | C Sensors + GNSS |  |
| — | **ANT1** | IFA_1090 | ANT_IFA_1090MHz | (85.5, 57.8) | **Not placed** (on-board antenna; per-cut measured 50.0mm outer envelope / 48.5mm centerline span) | Per-cut measured 50.0mm outer envelope / 48.5mm centerline span |
| — | **ZP1** | DNP 并-天线侧 | C_0603_1608Metric | (85.5, 63.6) | **Not placed** (DNP) |  |
| — | **ZP2** | DNP 并-电台侧 | C_0603_1608Metric | (90.5, 63.6) | **Not placed** (DNP) |  |
| ☐ | **ZS1** | 0R 串 | L_0603_1608Metric | (88.0, 62.9) | E 1090 Receive Chain |  |
| — | **SW1** | RESET短接焊盘 | SolderJumper-2_P1.3mm_ | (88.7, 91.3) | **Not placed** (solder-bridge pad) |  |
| — | **SW2** | BOOTSEL短接焊盘 | SolderJumper-2_P1.3mm_ | (92.9, 91.3) | **Not placed** (solder-bridge pad) |  |
| — | **TP1** | TestPoint | TestPoint_Pad_1.0x1.0m | (102.0, 91.3) | **Not placed** (test-point pad) |  |
| — | **TP2** | TestPoint | TestPoint_Pad_1.0x1.0m | (104.9, 91.3) | **Not placed** (test-point pad) |  |
| — | **TP3** | TestPoint | TestPoint_Pad_1.0x1.0m | (107.8, 91.3) | **Not placed** (test-point pad) |  |
| — | **TP4** | TestPoint | TestPoint_Pad_1.0x1.0m | (110.7, 91.3) | **Not placed** (test-point pad) |  |
| — | **TP5** | TestPoint | TestPoint_Pad_1.0x1.0m | (113.5, 91.3) | **Not placed** (test-point pad) |  |
| — | **TP6** | TestPoint | TestPoint_Pad_1.0x1.0m | (116.4, 91.3) | **Not placed** (test-point pad) |  |
| — | **TP7** | TestPoint | TestPoint_Pad_1.0x1.0m | (80.7, 78.7) | **Not placed** (test-point pad) |  |
| — | **H1** | — | MountingHole_2.7mm_M2. | (54.0, 56.0) | **Not placed** (mounting hole) |  |
| — | **H2** | — | MountingHole_2.7mm_M2. | (146.0, 56.0) | **Not placed** (mounting hole) |  |
| — | **H3** | — | MountingHole_2.7mm_M2. | (54.0, 106.0) | **Not placed** (mounting hole) |  |
| — | **H4** | — | MountingHole_2.7mm_M2. | (146.0, 106.0) | **Not placed** (mounting hole) |  |
