naizhao/Pilot-Kit-Box-ESP32-P4/docs/ux/preview-800x480-font.png

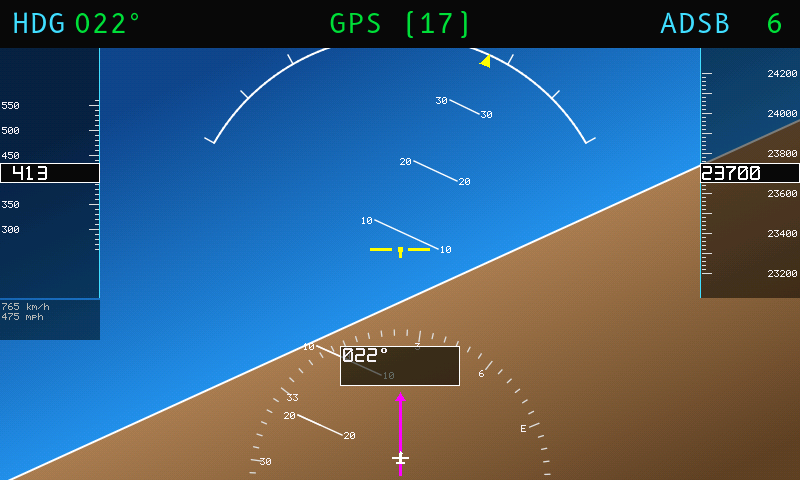
docs/ux/preview-800x480-font.png
