naizhao/Pilot-Kit-Box-ESP32-P4/docs/ux/preview-font-weight.png

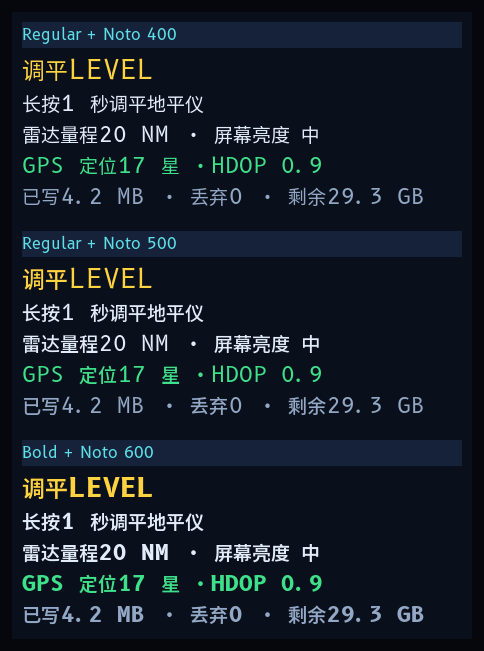
docs/ux/preview-font-weight.png
