naizhao/Pilot-Kit-Box-ESP32-P4/images/3d-case-back.png

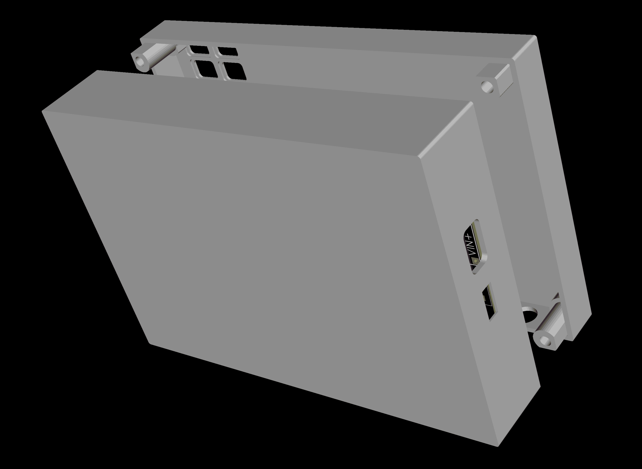
images/3d-case-back.png
