naizhao/Pilot-Kit-Box-ESP32-P4/images/empty-4.3-diag-imu.png

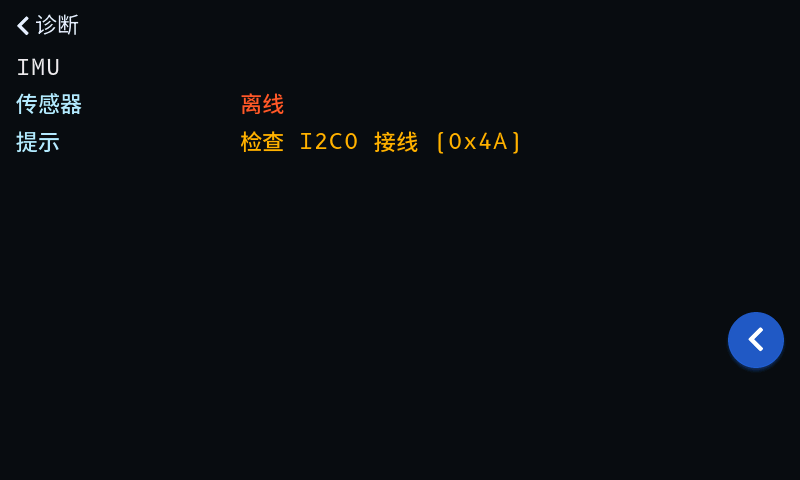
images/empty-4.3-diag-imu.png
