naizhao/Pilot-Kit-Box-ESP32-P4/images/empty-4.3-list.png

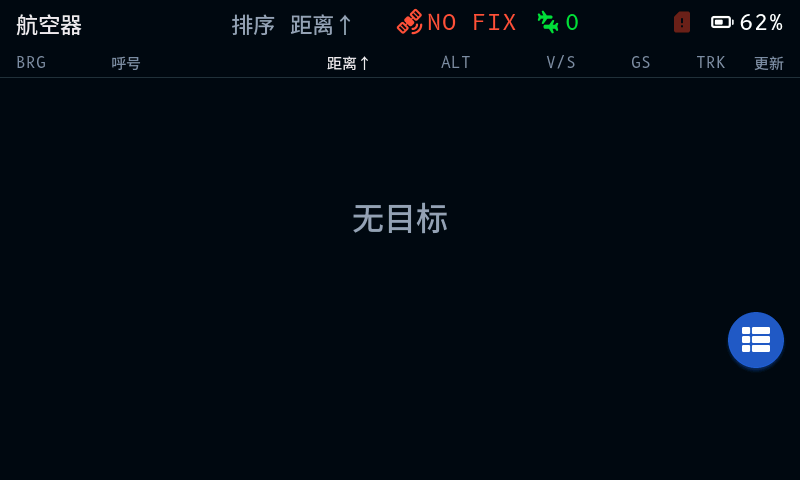
images/empty-4.3-list.png
