naizhao/Pilot-Kit-Box-ESP32-P4/images/empty-4.3-traffic-en.png

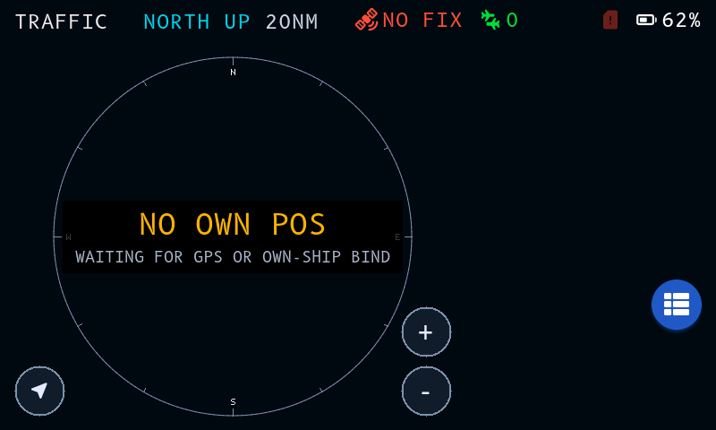
images/empty-4.3-traffic-en.png
