naizhao/Pilot-Kit-Box-ESP32-P4/images/ui-4.3-cal-acc1.png

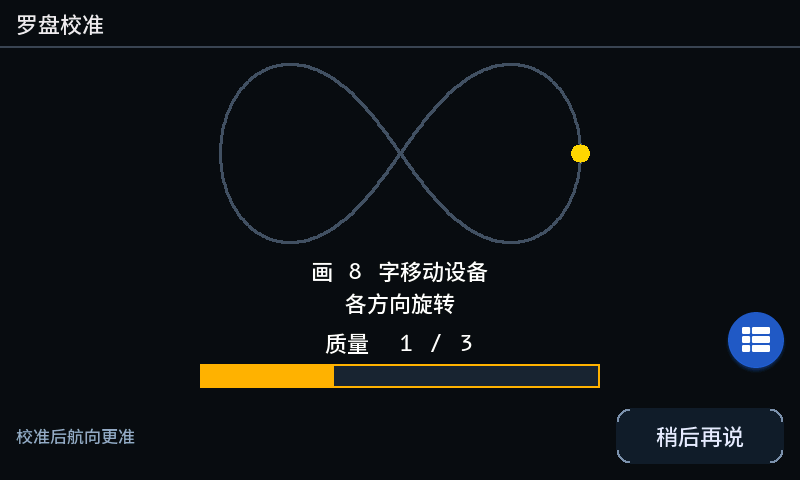
images/ui-4.3-cal-acc1.png
