naizhao/Pilot-Kit-Box-ESP32-P4/images/ui-4.3-diag-imu-jam.png

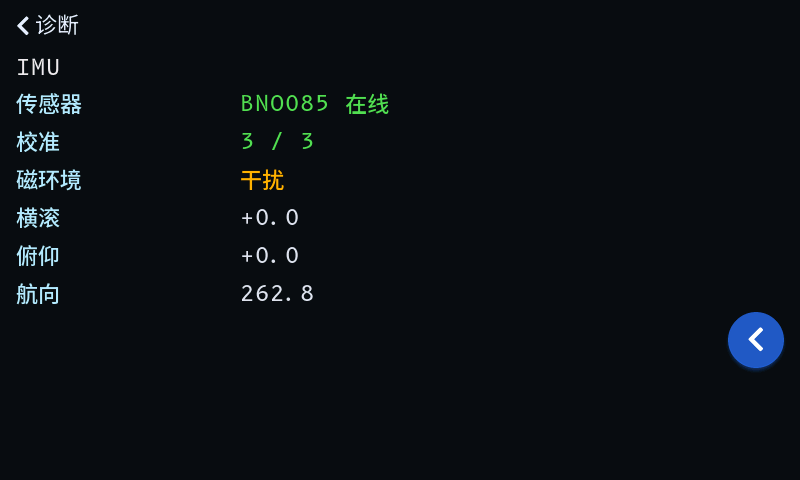
images/ui-4.3-diag-imu-jam.png
