naizhao/Pilot-Kit-Box-ESP32-P4/images/ui-4.3-map-headingup.png

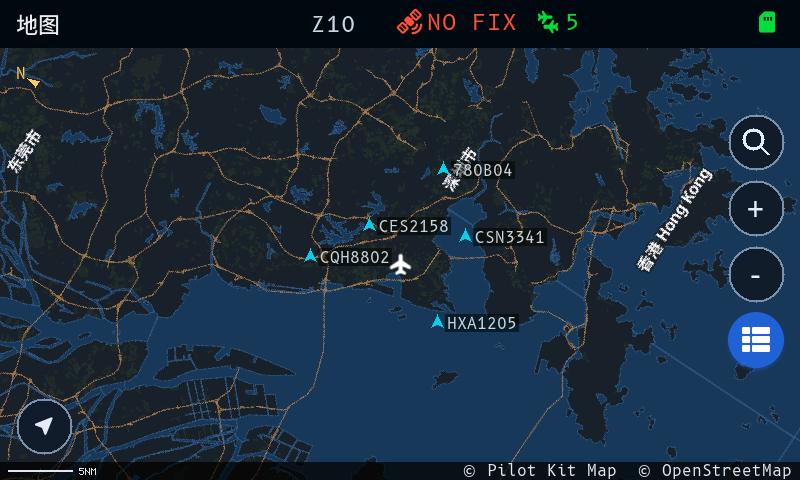
images/ui-4.3-map-headingup.png
