naizhao/Pilot-Kit-Box-ESP32-P4/images/ui-4.3-map-no-gps.png

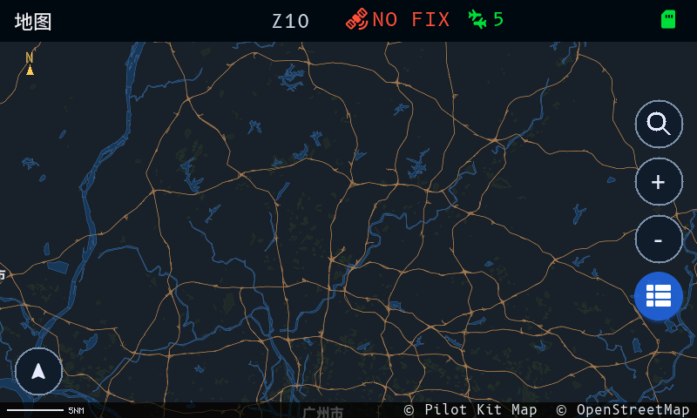
images/ui-4.3-map-no-gps.png
