naizhao/Pilot-Kit-Box-ESP32-P4/images/ui-4.3-map-no-pack.png

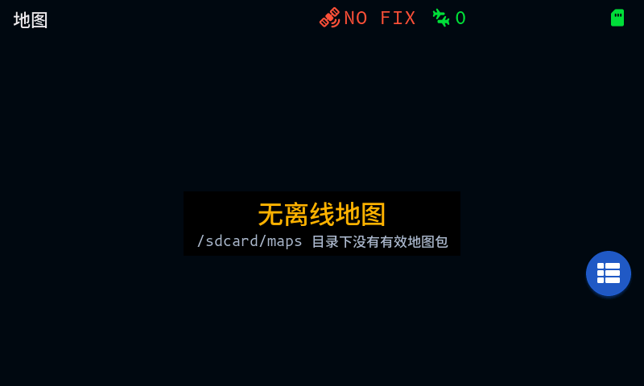
images/ui-4.3-map-no-pack.png
