naizhao/Pilot-Kit-Box-ESP32-P4/images/ui-4.3-menu-bright.png

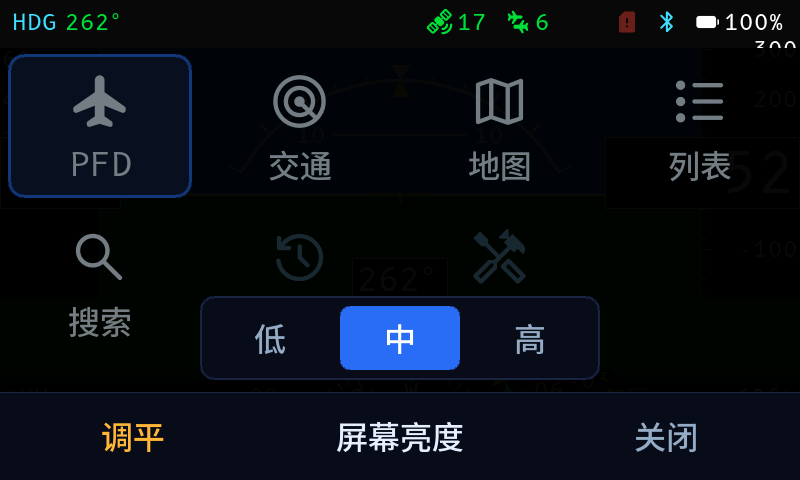
images/ui-4.3-menu-bright.png
