naizhao/Pilot-Kit-Box-ESP32-P4/images/ui-4.3-menu-level-done.png

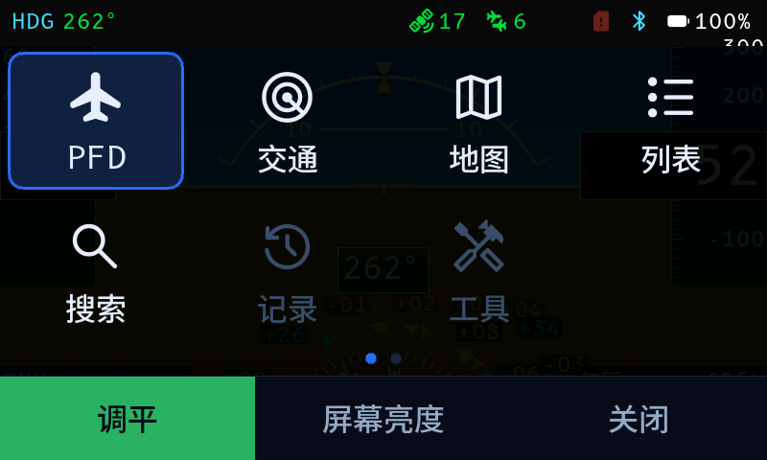
images/ui-4.3-menu-level-done.png
