naizhao/Pilot-Kit-Box-ESP32-P4/images/ui-4.3-menu-page2.png

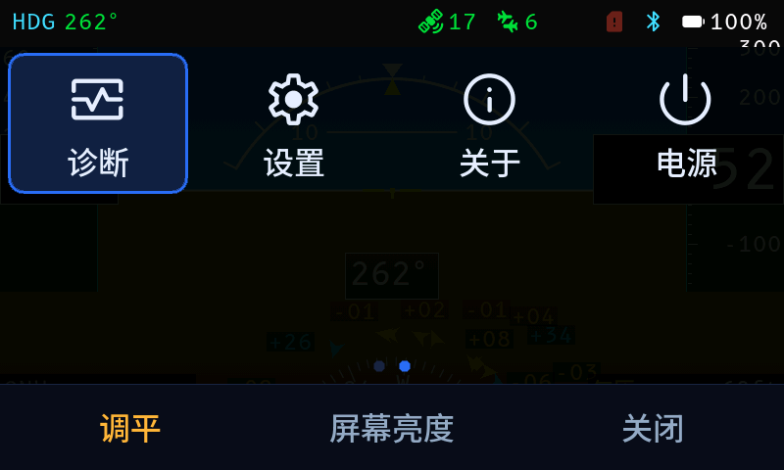
images/ui-4.3-menu-page2.png
