naizhao/Pilot-Kit-Box-ESP32-P4/hardware/expansion-board-v4/BOM_V4.6_AIRBAND-zh_CN.md

# V4.6 AIRBAND 采购补充清单（手写；airband 尚未进网表）

> 约束（用户 2026-09-11）：**尽量 0603**；**尽量复用已采购元件**（新增 SMT 料每项 ¥50 上机费）。
> **已逐件核对 `~/Downloads/BOM_采购清单 (2).xlsx`（V4.5 采购）与本仓 V4.5 `BOM_PURCHASE-zh_CN.md`。**
> 结论：**新增 BOM 仅 3 颗芯片，无源全部复用**。

## 一、新增 BOM（仅 3 项）

| 采购 | 类别 | 值/规格 | 封装 | 数量 | 位号 | 推荐型号 | 立创料号 | 说明 |
|---|---|---|---|---|---|---|---|---|
| 🔴必买指定 | 主芯片-航空射频 | BK4819QN32SC | QFN-32-1EP_4x4mm | 2 | U21 | BK4819QN32SC（博通 Beken） | 淘宝 | 18–660MHz 收发器，只用接收；PAOUT 不接。备损 1 颗 |
| 🔴必买指定 | 音频 ADC | PCM1808PWR | TSSOP-14 | 2 | U22 | PCM1808PWR（TI） | **C55513** | 24bit/96kHz 立体声 ADC，无 I²C（避免与载板 ES7210 0x40 冲突）。备损 1 颗 |
| 🔴必买指定 | 晶振-航空参考 | 26MHz TCXO **≤±2.5ppm** | **TCXO_2520** | 2 | Y4 | **Epson TG-5006CG-12H（±2.0ppm，2520，订货号 X1G004211000300）** | 淘宝 | BK4819 要求参考 ≤±2.5ppm（datasheet §1.2.3）。**输出为削峰正弦，需交流耦合进 XI**。备损 1 颗 |

## 二、无源全部复用（对照你的现有清单，逐件列出）

| 采购 | 类别 | 值/规格 | 封装 | 位号 | 你的来源 |
|---|---|---|---|---|---|
| ✅已有 | 隔直 | 100pF | C_0603 | C88 | V4.5 0603 电容本 |
| ✅已有 | 匹配-串联 | 100nH | L_0402 | L18 | **V4.5 已有：C18221115（DDY WI0402IFR10KST-HF，绕线 SRF1.4GHz）** |
| ✅已有 | 匹配-并联 | 18pF | C_0603 | C89 | V4.5 0603 电容本（配 FC-135 的 C68/C69 同值） |
| ✅已有 | 音频耦合 | 10uF | C_0805 | C91, C92 | **V4.5 只有 0805/1206 的 10µF，无 0603** |
| ✅已有 | 音频偏置 | 10k | R_0603 | R58, R59 | V4.5 0603 电阻本 |
| ✅已有 | AVCC 串阻 | 0R | R_0603 | R60 | V4.5 0603 电阻本 |
| ✅已有 | 去耦 | 10uF | C_0805 | C93 | **同上，用 0805** |
| ✅已有 | 去耦 | 100nF | C_0603 | C94, C95, C96, C98 | V4.5 0603 电容本（C14663） |
| ✅已有 | 去耦 | 1uF | C_0603 | C97 | V4.5 0603 电容本 |
| ✅已有 | 低电容 ESD | TPESD8L3.3 | D_0402 | D6 | 你已有 100 颗（C2830293）——射频专用，保持 0402 |
| ✅已有 | U.FL 座 | IPEX1 3-pad | U.FL | J10 | 你有一大堆（C41432122） |
| ✅已有 | 尾线/天线 | U.FL→SMA + 航空天线 | — | — | 你都有 |

## 三、匹配调谐（用你现有值，不新增）

> 匹配值待上板 VNA 调，从**你现有的值**里取：
> - 电感（0402 绕线）：`18nH / 27nH / 33nH / 100nH`（对应 C18221115、C113111、C6807986 等）
> - 电容（0603 C0G）：`5.6 / 6.8 / 8.2 / 10 / 12 / 15 / 18pF`
>
> **不需要新买任何调谐件。**

## 四、结论

- **新增 BOM：只有 3 颗芯片**（BK4819、PCM1808、TCXO）。
- **无源 0 新增**：匹配电感复用你的 0402 100nH，匹配电容复用 0603 18pF，其余全复用。
- **调谐 0 新增**：从现有 18/27/33/100nH + 5.6–18pF 里试值。
- 板上 airband 共 **19 件**（3 芯片 + 16 复用）。
