naizhao/Pilot-Kit-Box-ESP32-P4/hardware/expansion-board-v3/ASSEMBLY-zh_CN.md

# V3.11 手工贴片点位清单
> 由 `tools/gen_assembly.py` 从原理图分页 + PCB 坐标自动生成，改板后重跑。

配套看图：板上位置 `render/top.png`，丝印和 pin1 `render/silk.svg`。

---

# ⚠️ 手上是 V3.2 那批板的话，先看这个

**V3.2 实物板上有 4 对位号丝印是对调的。**
源文件已在 V3.9 修好，但 V3.2 那批已经印出来了，改不了——
贴这几个位置时**只认下表的坐标，不要看板上的字**。

阴在于：每个元件旁边都有位号，排版看着完全正常，只是内容张冠李戴，
不像缺字漏字那样一眼能发现。目检、DRC、Gerber 预览全都发现不了。

| 位号 | 值 | 元件实际在 | 板上那个位置印的却是 | 会不会真贴错 |
|---|---|---|---|---|
| **C46** | 3pF | (118.7, 86.2) | `C47` | 🔴 **会**，两者尺寸相同，塞得进对方位置 |
| **C47** | 200pF | (118.7, 88.4) | `C46` | 🔴 **会**，两者尺寸相同，塞得进对方位置 |
| **L14** | 100nH | (120.4, 63.3) | `C30` | 🔴 **会**，两者尺寸相同，塞得进对方位置 |
| **C30** | 100pF | (120.4, 62.1) | `L14` | 🔴 **会**，两者尺寸相同，塞得进对方位置 |
| **R33** | 100k | (108.7, 75.2) | `C25` | 🔴 **会**，两者尺寸相同，塞得进对方位置 |
| **C25** | 100nF | (109.2, 77.4) | `R33` | 🔴 **会**，两者尺寸相同，塞得进对方位置 |
| **C18** | 10uF | (78.9, 64.6) | `C6` | 🟢 不会，尺寸不同塞不进去 |
| **C6** | 1uF | (78.6, 67.0) | `C18` | 🟢 不会，尺寸不同塞不进去 |

> **当前源文件检测结果：0 对互换**（已全部修复 ✅）

> 判据是「站在元件旁边，最近的那个位号文字是不是它自己的」。
反过来按「文字找最近元件」会漏——被大芯片挡住的那几个就是这么漏掉的。

---

## 开工前

**先做完 `BOARD_TEST.md` 的阶段 1、2。** 裸板的电源对地绝缘和内层连通性
一旦贴了片就测不了了——去耦电容和芯片会并联在电源地之间，读数不再是开路。

### 顺序原则：先大后小，先中间后外围

不管整板回流还是逐个热风吹，结论一样：

- **整板回流**——大件对位要反复调整，周围先摆了 0402 会被镊子碰歪

- **逐个热风**——吹外围时热风会掀翻已贴好的小件；大件热容大，反过来不怕

所以下面每个阶段内部**按封装面积从大到小排**，照着表从上往下贴就行。

### 几个容易吃亏的点

- **BNO085 / BMP388 / CC1312R 这类塑封件怕潮**。拆封超过一周的，贴之前 125°C 烘 4 小时，不然回流时内部水汽汽化会把封装顶裂（爆米花效应），外观完全看不出来，表现是芯片直接不工作
- **底部焊盘的件（★★★）烙铁够不着**，吹歪了只能拆下来重来，所以对位要在加热前反复确认，别指望后期补救
- **0402 风量一定调小**，标称的风量吹 0402 会直接把件吹飞，而且飞走的件常常落在别的焊盘上造成短路
- **pin1 方向以板上丝印为准**（缺角/圆点），下表的「旋转」只是参考。这块板的元件朝向前期出过错——曾经有 25 个两脚件的 pin1/pin2 方向是反的

---

## 阶段 A：电源（9 件）
3 个 LDO 加各路的输入输出电容，**这 9 件自成闭环**，贴完就能上电量电压，不用碰任何贵件。

| 位号 | 型号 | 封装 | 板上位置 | 旋转 | 手工难度 |
|---|---|---|---|---|---|
| **U3** | TPS7A2033PDBVR | SOT-23-5 | (74.3, 93.3) | 180° | ★ 引脚在外，烙铁可补焊 |
| **U1** | ME6211C33M5 | SOT-23-5 | (69.4, 93.3) | 180° | ★ 引脚在外，烙铁可补焊 |
| **U2** | TPS7A2033PDBVR | SOT-23-5 | (63.1, 93.3) | 180° | ★ 引脚在外，烙铁可补焊 |
| **C1** | 10uF | C_0805_2012Metric | (78.6, 93.3) | -90° | ★ 常规 |
| **C2** | 1uF | C_0603_1608Metric | (62.0, 98.3) | 180° | ★ 常规 |
| **C4** | 1uF | C_0603_1608Metric | (71.0, 98.3) | 0° | ★ 常规 |
| **C3** | 1uF | C_0603_1608Metric | (66.5, 98.3) | 0° | ★ 常规 |
| **C6** | 1uF | C_0603_1608Metric | (78.6, 67.0) | 0° | ★ 常规 |
| **C5** | 1uF | C_0402_1005Metric | (109.6, 79.2) | 0° | ★★  0402，热风易吹跑，风量调小 |

**贴完验证**：实验电源限流 100mA，5V 正极夹 `J1.1`、负极夹 `U10.49`（CC1312R 的 EP 大焊盘，此时还没贴件，焊盘是空的正好夹）。
  - 空载电流应该只有几 mA；一上电顶到限流就断电查 U1/U2/U3 有没有连锡
  - `U9.8` 量 3V3_DIG = 3.3V ±5%
  - `U14.1` 量 3V3_RF = 3.3V ±5%
  - `Q2.2` 量 3V3_GNSS = 3.3V ±5%
  三路都对了才往下走。这一步没过，后面贴什么都是白贴。

## 阶段 B：MCU + Flash（32 件）
RP2040 + QSPI Flash + 12MHz 晶振 + USB-C 座。

| 位号 | 型号 | 封装 | 板上位置 | 旋转 | 手工难度 |
|---|---|---|---|---|---|
| **J4** | USB-C_16P | USB_C_Receptacle_HRO_TYPE- | (53.5, 92.0) | -90° | ★ 常规 |
| **U8** | RP2040 | QFN-56-1EP_7x7mm_P0.4mm_EP | (88.4, 80.5) | -90° | ★★★ 底部焊盘，只能热风，烙铁够不着 |
| **U9** | W25Q128JVSIQ | SOIC-8_5.3x5.3mm_P1.27mm | (103.4, 82.1) | 0° | ★ 引脚在外，烙铁可补焊 |
| **D1** | B5819W | D_SOD-123 | (97.8, 91.3) | 0° | ★ 引脚在外，烙铁可补焊 |
| **Y1** | 12MHz CL=10pF ABM8-272-T3 | Crystal_SMD_3225-4Pin_3.2x | (100.4, 87.7) | 0° | ★ 常规 |
| **R51** | 10k | R_0603_1608Metric | (96.0, 85.2) | -90° | ★ 常规 |
| **R5** | 10k | R_0603_1608Metric | (95.7, 98.3) | 180° | ★ 常规 |
| **R8** | 5.1k | R_0603_1608Metric | (107.8, 98.3) | 0° | ★ 常规 |
| **R6** | 10k | R_0603_1608Metric | (99.8, 98.3) | 180° | ★ 常规 |
| **R7** | 5.1k | R_0603_1608Metric | (103.8, 98.3) | 0° | ★ 常规 |
| **C22** | 100nF | C_0603_1608Metric | (95.7, 95.2) | 0° | ★ 常规 |
| **C26** | 100nF | C_0603_1608Metric | (107.8, 95.2) | 0° | ★ 常规 |
| **C24** | 100nF | C_0603_1608Metric | (103.8, 95.2) | 0° | ★ 常规 |
| **C27** | 100nF | C_0603_1608Metric | (111.9, 95.2) | 0° | ★ 常规 |
| **C23** | 100nF | C_0603_1608Metric | (99.8, 95.2) | 0° | ★ 常规 |
| **C28** | 1uF | C_0603_1608Metric | (86.5, 87.7) | 0° | ★ 常规 |
| **C29** | 1uF | C_0603_1608Metric | (89.5, 87.7) | 0° | ★ 常规 |
| **R10** | 27R | R_0603_1608Metric | (95.6, 87.7) | 180° | ★ 常规 |
| **R9** | 27R | R_0603_1608Metric | (92.5, 87.7) | 180° | ★ 常规 |
| **R50** | 10k | R_0603_1608Metric | (94.0, 85.2) | 90° | ★ 常规 |
| **C87** | 10nF C0G | C_0603_1608Metric | (97.8, 84.4) | 90° | ★ 常规 |
| **C20** | 15pF C0G | C_0603_1608Metric | (107.6, 87.7) | 180° | ★ 常规 |
| **R4** | 1k | R_0603_1608Metric | (110.6, 87.7) | 0° | ★ 常规 |
| **C19** | 15pF C0G | C_0603_1608Metric | (104.6, 87.7) | 0° | ★ 常规 |
| **C25** | 100nF | C_0603_1608Metric | (109.2, 77.4) | 0° | ★ 常规 |
| **C83** | 100nF | C_0402_1005Metric | (93.6, 79.5) | -90° | ★★  0402，热风易吹跑，风量调小 |
| **C85** | 100nF | C_0402_1005Metric | (96.0, 79.5) | 0° | ★★  0402，热风易吹跑，风量调小 |
| **C86** | 100nF | C_0402_1005Metric | (96.0, 82.0) | 0° | ★★  0402，热风易吹跑，风量调小 |
| **C84** | 1uF | C_0402_1005Metric | (93.6, 82.0) | 0° | ★★  0402，热风易吹跑，风量调小 |
| **C82** | 100nF | C_0402_1005Metric | (83.0, 84.5) | -90° | ★★  0402，热风易吹跑，风量调小 |
| **D5** | TPESD8L3.3 0.3pFtyp 0.5pFmax | D_0402_1005Metric | (60.0, 93.6) | 180° | ★★  0402，热风易吹跑，风量调小 |
| **D4** | TPESD8L3.3 0.3pFtyp 0.5pFmax | D_0402_1005Metric | (60.0, 90.4) | 180° | ★★  0402，热风易吹跑，风量调小 |

**贴完验证**：USB-C 插电脑，镊子短接 `SW2`(BOOTSEL) 再上电 → 电脑应出现 **RPI-RP2** U 盘。
  - 认不到 U 盘：先量 `C28.1` 上的 RP_1V1 有没有 1.1V（RP2040 内部 LDO 出的）
  - 认到了但 Flash 不识别：查 U9 的四条 QSPI 线，SOIC-8 引脚在外，烙铁能补

## 阶段 C：传感器 + GNSS（33 件）
IMU / 气压 / 磁力计 / GNSS，都是 I2C 和 UART 慢速接口。

| 位号 | 型号 | 封装 | 板上位置 | 旋转 | 手工难度 |
|---|---|---|---|---|---|
| **U7** | ATGM336H-6N-74 | ATGM336H_LCC-18 | (70.4, 66.4) | 0° | ★★★ 底部焊盘，只能热风，烙铁够不着 |
| **U4** | BNO085 | BNO085_LGA-28 | (63.7, 78.3) | 0° | ★★★ 底部焊盘，只能热风，烙铁够不着 |
| **J2** | U.FL_GNSS_EXT(经尾线转SMA) | U.FL_Hirose_U.FL-R-SMT-1_V | (52.9, 74.1) | 180° | ★ 常规 |
| **J8** | U.FL→内置patch | U.FL_Hirose_U.FL-R-SMT-1_V | (52.9, 64.4) | 180° | ★ 常规 |
| **U6** | QMC5883P | LGA-16_3x3mm_P0.5mm | (71.3, 77.0) | 0° | ★★★ 底部焊盘，只能热风，烙铁够不着 |
| **Q5** | AO3401A | SOT-23 | (57.8, 72.6) | 0° | ★ 引脚在外，烙铁可补焊 |
| **Q4** | AO3401A | SOT-23 | (61.8, 70.2) | 0° | ★ 引脚在外，烙铁可补焊 |
| **U5** | BMP388 | BMP388_LGA-10 | (71.3, 81.2) | 0° | ★★★ 底部焊盘，只能热风，烙铁够不着 |
| **C18** | 10uF | C_0805_2012Metric | (78.9, 64.6) | 180° | ★ 常规 |
| **U17** | XA17-G4K | SOT-363_SC-70-6 | (58.8, 63.3) | 0° | ★★  0.65mm 间距，引脚在外但很密 |
| **F5** | 6V/200mA | Fuse_0805_2012Metric | (56.4, 69.7) | 0° | ★ 常规 |
| **F4** | 6V/200mA | Fuse_0805_2012Metric | (61.8, 67.4) | 0° | ★ 常规 |
| **R27** | 10k | R_0603_1608Metric | (61.8, 73.3) | 0° | ★ 常规 |
| **C57** | 100pF | C_0402_1005Metric | (63.4, 63.3) | -90° | ★★  0402，热风易吹跑，风量调小 |
| **R55** | 10k | R_0603_1608Metric | (59.1, 80.3) | 90° | ★ 常规 |
| **C17** | 100nF | C_0603_1608Metric | (78.5, 61.4) | 0° | ★ 常规 |
| **R3** | 4.7k | R_0603_1608Metric | (61.4, 108.7) | 0° | ★ 常规 |
| **C14** | 100nF | C_0603_1608Metric | (61.8, 87.2) | 0° | ★ 常规 |
| **C15** | 4.7uF | C_0603_1608Metric | (66.1, 87.2) | 180° | ★ 常规 |
| **R1** | 10k | R_0603_1608Metric | (79.0, 87.2) | 180° | ★ 常规 |
| **C16** | 100nF | C_0603_1608Metric | (70.4, 87.2) | 0° | ★ 常规 |
| **C11** | 100nF | C_0603_1608Metric | (70.6, 84.5) | 0° | ★ 常规 |
| **C13** | 100nF | C_0603_1608Metric | (79.1, 84.5) | 0° | ★ 常规 |
| **C12** | 100nF | C_0603_1608Metric | (74.8, 84.5) | 0° | ★ 常规 |
| **C10** | 100nF | C_0603_1608Metric | (66.4, 84.5) | 0° | ★ 常规 |
| **R2** | 4.7k | R_0603_1608Metric | (61.4, 106.1) | 0° | ★ 常规 |
| **R26** | 10k | R_0603_1608Metric | (58.8, 76.4) | 0° | ★ 常规 |
| **L15** | 33nH | L_0402_1005Metric | (58.0, 67.6) | 90° | ★★  0402，热风易吹跑，风量调小 |
| **R52** | 10k | R_0402_1005Metric | (60.0, 83.0) | 0° | ★★  0402，热风易吹跑，风量调小 |
| **R53** | 10k | R_0402_1005Metric | (63.0, 84.4) | 180° | ★★  0402，热风易吹跑，风量调小 |
| **C59** | 100pF | C_0402_1005Metric | (56.3, 62.4) | 0° | ★★  0402，热风易吹跑，风量调小 |
| **C58** | 100pF | C_0402_1005Metric | (56.5, 64.6) | 90° | ★★  0402，热风易吹跑，风量调小 |
| **L2** | 33nH | L_0402_1005Metric | (61.8, 64.8) | 90° | ★★  0402，热风易吹跑，风量调小 |

**贴完验证**：刷个扫描固件，I2C 上逐个点名：BNO085、BMP388、QMC5883P 应各自应答。
  - GNSS 看 `U7.2`(GNSS_TXD) 有没有 NMEA 输出，**室内收不到星是正常的**，有 `$GPTXT` 和 `$GPGSV` 输出就说明模块活着
  - 有源天线检测：`$GPTXT` 应报 `ANTENNA OK`；报 `OPEN` 说明该路天线没接/没贴，报 `SHORT` 说明馈电短路。U7.14(VCC_RF) 是检测电流的来源，量它应约 3.3V

## 阶段 D：978 收发（34 件）
CC1312R 和它的 48MHz / 32.768kHz 两颗晶振。

| 位号 | 型号 | 封装 | 板上位置 | 旋转 | 手工难度 |
|---|---|---|---|---|---|
| **U10** | CC1312R1F3RGZR | QFN-48-1EP_7x7mm_P0.5mm_EP | (126.2, 85.0) | 0° | ★★★ 底部焊盘，只能热风，烙铁够不着 |
| **J5** | U.FL_978 | U.FL_Hirose_U.FL-R-SMT-1_V | (145.5, 83.5) | 0° | ★ 常规 |
| **Y3** | 32.768kHz FC-135 | Crystal_SMD_3215-2Pin_3.2x | (122.7, 91.3) | 0° | ★ 常规 |
| **Y2** | 48MHz ABM8W-7pF | Crystal_SMD_3225-4Pin_3.2x | (133.8, 81.7) | 90° | ★ 常规 |
| **Q2** | AO3401A | SOT-23 | (125.1, 105.2) | 0° | ★ 引脚在外，烙铁可补焊 |
| **F2** | 6V/200mA | Fuse_0805_2012Metric | (129.8, 105.2) | -90° | ★ 常规 |
| **C66** | 22uF | C_0805_2012Metric | (123.2, 100.5) | 0° | ★ 常规 |
| **C60** | 22uF | C_0805_2012Metric | (136.2, 93.1) | 0° | ★ 常规 |
| **L7** | 6.8uH | L_0805_2012Metric | (131.5, 93.1) | 0° | ★ 常规 |
| **R17** | 10k | R_0603_1608Metric | (121.4, 105.2) | 90° | ★ 常规 |
| **C69** | 18pF | C_0603_1608Metric | (127.7, 100.5) | 0° | ★ 常规 |
| **C68** | 18pF | C_0603_1608Metric | (123.1, 93.8) | 0° | ★ 常规 |
| **R47** | 10k | R_0603_1608Metric | (132.5, 85.0) | 0° | ★ 常规 |
| **R56** | 10k | R_0603_1608Metric | (132.3, 89.7) | 0° | ★ 常规 |
| **C65** | 100nF | C_0603_1608Metric | (136.8, 97.0) | 0° | ★ 常规 |
| **C63** | 100nF | C_0603_1608Metric | (129.0, 97.0) | 0° | ★ 常规 |
| **C64** | 100nF | C_0603_1608Metric | (132.9, 97.0) | 0° | ★ 常规 |
| **C62** | 100nF | C_0603_1608Metric | (125.1, 97.0) | 0° | ★ 常规 |
| **C61** | 100nF | C_0603_1608Metric | (121.2, 97.0) | 180° | ★ 常规 |
| **C67** | 1uF | C_0603_1608Metric | (126.9, 93.1) | 180° | ★ 常规 |
| **C39** | 100pF | C_0402_1005Metric | (140.0, 83.6) | -90° | ★★  0402，热风易吹跑，风量调小 |
| **C40** | 3.6pF | C_0402_1005Metric | (123.6, 76.3) | 0° | ★★  0402，热风易吹跑，风量调小 |
| **C41** | 2.7pF | C_0402_1005Metric | (126.9, 76.3) | 0° | ★★  0402，热风易吹跑，风量调小 |
| **C42** | 6.2pF | C_0402_1005Metric | (130.2, 76.3) | 180° | ★★  0402，热风易吹跑，风量调小 |
| **C45** | 100pF | C_0402_1005Metric | (119.2, 84.3) | 180° | ★★  0402，热风易吹跑，风量调小 |
| **C43** | 3pF | C_0402_1005Metric | (137.6, 78.3) | 180° | ★★  0402，热风易吹跑，风量调小 |
| **L13** | 7.5nH | L_0402_1005Metric | (119.2, 83.2) | 0° | ★★  0402，热风易吹跑，风量调小 |
| **L12** | 6.8nH | L_0402_1005Metric | (137.6, 76.3) | 0° | ★★  0402，热风易吹跑，风量调小 |
| **L11** | 6.8nH | L_0402_1005Metric | (134.2, 76.3) | 0° | ★★  0402，热风易吹跑，风量调小 |
| **L10** | 27nH | L_0402_1005Metric | (120.8, 76.3) | 0° | ★★  0402，热风易吹跑，风量调小 |
| **C44** | 3.6pF | C_0402_1005Metric | (121.7, 78.0) | 0° | ★★  0402，热风易吹跑，风量调小 |
| **L8** | 100nH | L_0402_1005Metric | (142.6, 87.0) | 90° | ★★  0402，热风易吹跑，风量调小 |
| **D3** | TPESD8L3.3 0.3pFtyp 0.5pFmax | D_0402_1005Metric | (140.0, 86.9) | -90° | ★★  0402，热风易吹跑，风量调小 |
| **L9** | 7.5nH | L_0402_1005Metric | (124.2, 78.0) | 0° | ★★  0402，热风易吹跑，风量调小 |

**贴完验证**：接调试器到 `TP1`(SWCLK) / `TP2`(SWDIO)，能读到 CC1312R 的 ID 就算通。
  - 起不来先量 `C60.1` 的 SUBG_VDDR（内部 DC/DC 输出，约 1.7V）和 `C67.1` 的 SUBG_DCOUPL（约 1.28V）

## 阶段 E：1090 接收链（49 件）
**全板最贵的一段**（QPL9547 ¥8.5 / TA0970A ¥7.5×2 / AD8313 ¥71），排最后——前面四级都验过了才让它们上板。

| 位号 | 型号 | 封装 | 板上位置 | 旋转 | 手工难度 |
|---|---|---|---|---|---|
| **U14** | AD8313ARMZ | MSOP-8_3x3mm_P0.65mm | (114.1, 82.1) | 0° | ★ 引脚在外，烙铁可补焊 |
| **FL2** | TA0970A | TA0970A_SMD3838-6 | (125.1, 71.2) | 0° | ★★★ 底部焊盘，只能热风，烙铁够不着 |
| **FL1** | TA0970A | TA0970A_SMD3838-6 | (110.2, 71.2) | 0° | ★★★ 底部焊盘，只能热风，烙铁够不着 |
| **J6** | U.FL_1090_EXT(经尾线转SMA) | U.FL_Hirose_U.FL-R-SMT-1_V | (124.3, 62.1) | 0° | ★ 常规 |
| **J7** | U.FL_IFA_TEST(π后调试口) | U.FL_Hirose_U.FL-R-SMT-1_V | (103.1, 61.3) | 90° | ★ 常规 |
| **U15** | TLV3501(TOKMAS) | SOT-23-6 | (83.1, 91.3) | 0° | ★ 引脚在外，烙铁可补焊 |
| **Q3** | AO3401A | SOT-23 | (132.0, 62.1) | 180° | ★ 引脚在外，烙铁可补焊 |
| **U11** | QPL9547TR7 | DFN-8-1EP_2x2mm_P0.5mm_EP0 | (101.6, 71.2) | 0° | ★★★ 底部焊盘，只能热风，烙铁够不着 |
| **U12** | BGA2817 | SOT-363_SC-70-6 | (117.7, 71.2) | 180° | ★★  0.65mm 间距，引脚在外但很密 |
| **U16** | XA17-G4K | SOT-363_SC-70-6 | (114.6, 62.1) | 0° | ★★  0.65mm 间距，引脚在外但很密 |
| **F3** | 6V/200mA | Fuse_0805_2012Metric | (140.2, 62.1) | 0° | ★ 常规 |
| **R18** | 10k | R_0603_1608Metric | (136.2, 62.1) | 0° | ★ 常规 |
| **R57** | 33R | R_0603_1608Metric | (85.7, 95.3) | -90° | ★ 常规 |
| **C51** | 1nF | C_0603_1608Metric | (55.6, 85.2) | 180° | ★ 常规 |
| **ZS1** | 0R 串 | L_0603_1608Metric | (88.0, 62.9) | 0° | ★ 常规 |
| **C49** | 100nF | C_0603_1608Metric | (55.6, 80.1) | 180° | ★ 常规 |
| **R34** | 10k | R_0603_1608Metric | (55.6, 77.5) | 0° | ★ 常规 |
| **R35** | 10k | R_0603_1608Metric | (55.6, 82.6) | 0° | ★ 常规 |
| **R21** | 0R | R_0603_1608Metric | (115.2, 85.0) | 180° | ★ 常规 |
| **R32** | 10k | R_0603_1608Metric | (112.5, 75.2) | 0° | ★ 常规 |
| **R33** | 100k | R_0603_1608Metric | (108.7, 75.2) | 180° | ★ 常规 |
| **C46** | 3pF | C_0603_1608Metric | (118.7, 86.2) | 180° | ★ 常规 |
| **C47** | 200pF | C_0603_1608Metric | (118.7, 88.4) | 0° | ★ 常规 |
| **C55** | 100pF | C_0603_1608Metric | (90.2, 74.0) | 0° | ★ 常规 |
| **C56** | 100pF | C_0603_1608Metric | (85.1, 74.0) | 180° | ★ 常规 |
| **R22** | 0R | R_0603_1608Metric | (87.5, 71.2) | 0° | ★ 常规 |
| **R23** | 0R | R_0603_1608Metric | (91.4, 71.2) | 180° | ★ 常规 |
| **R31** | 1k | R_0603_1608Metric | (115.0, 87.3) | 0° | ★ 常规 |
| **C81** | 470pF C0G | C_0402_1005Metric | (118.6, 73.5) | 90° | ★★  0402，热风易吹跑，风量调小 |
| **C38** | 100pF | C_0402_1005Metric | (137.3, 69.2) | 0° | ★★  0402，热风易吹跑，风量调小 |
| **C31** | 100pF C0G | C_0402_1005Metric | (106.0, 71.2) | 0° | ★★  0402，热风易吹跑，风量调小 |
| **R54** | 10R | R_0402_1005Metric | (109.6, 82.1) | 90° | ★★  0402，热风易吹跑，风量调小 |
| **C53** | 100pF | C_0402_1005Metric | (110.2, 61.2) | 0° | ★★  0402，热风易吹跑，风量调小 |
| **C30** | 100pF | C_0402_1005Metric | (120.4, 62.1) | 180° | ★★  0402，热风易吹跑，风量调小 |
| **C54** | 100pF | C_0402_1005Metric | (105.3, 68.1) | 180° | ★★  0402，热风易吹跑，风量调小 |
| **R11** | 3.32k | R_0402_1005Metric | (98.8, 68.0) | 90° | ★★  0402，热风易吹跑，风量调小 |
| **R19** | 52.3R | R_0402_1005Metric | (138.5, 71.2) | 0° | ★★  0402，热风易吹跑，风量调小 |
| **C52** | 100nF | C_0402_1005Metric | (60.4, 96.2) | 0° | ★★  0402，热风易吹跑，风量调小 |
| **C21** | 100pF | C_0402_1005Metric | (101.0, 67.5) | 90° | ★★  0402，热风易吹跑，风量调小 |
| **C35** | 100pF C0G | C_0402_1005Metric | (141.2, 71.2) | 0° | ★★  0402，热风易吹跑，风量调小 |
| **C34** | 100pF C0G | C_0402_1005Metric | (129.4, 71.2) | 0° | ★★  0402，热风易吹跑，风量调小 |
| **C33** | 100pF C0G | C_0402_1005Metric | (120.9, 71.2) | 0° | ★★  0402，热风易吹跑，风量调小 |
| **C32** | 100pF C0G | C_0402_1005Metric | (114.5, 71.2) | 0° | ★★  0402，热风易吹跑，风量调小 |
| **C36** | 100pF | C_0402_1005Metric | (103.0, 66.5) | 0° | ★★  0402，热风易吹跑，风量调小 |
| **C48** | 1uF | C_0402_1005Metric | (99.6, 65.5) | 90° | ★★  0402，热风易吹跑，风量调小 |
| **C37** | 100nF | C_0402_1005Metric | (109.6, 85.0) | 0° | ★★  0402，热风易吹跑，风量调小 |
| **L14** | 100nH | L_0402_1005Metric | (120.4, 63.3) | 0° | ★★  0402，热风易吹跑，风量调小 |
| **L1** | 18nH 0402CS-18NXGRW | L_0402_1005Metric | (105.5, 69.8) | 90° | ★★  0402，热风易吹跑，风量调小 |
| **D2** | TPESD8L3.3 0.3pFtyp 0.5pFmax | D_0402_1005Metric | (128.3, 62.1) | 0° | ★★  0402，热风易吹跑，风量调小 |

**贴完验证**：`TP3`~`TP6`(DEMOD0-3) 和 `TP7`(RECOVERED_CLK) 接示波器。
  - 射频件方向错了很难看出来，贴之前对着 `render/silk.svg` 核一遍 pin1

## 阶段 F：对外接口（1 件）
2×20 排针，热容量大。

| 位号 | 型号 | 封装 | 板上位置 | 旋转 | 手工难度 |
|---|---|---|---|---|---|
| **J1** | J3_HAT_2x20_SMD排针 | PinHeader_2x20_P2.54mm_Ver | (92.6, 106.3) | 90° | ★ 常规 |

**贴完验证**：跟主板对插，量 5V 和 GND 通断。**放最后**：先贴上它，前面几阶段板子就没法平放在加热台上了。

## 不贴的 20 个位置

| 位号 | 为什么不贴 |
|---|---|
| **ANT1** | 板载天线，PCB铜箔本身，无器件；V3.10已回灌50.0mm外包络/48.5mm中心线 |
| **H1** | M2.5 安装孔（⌀2.7mm NPTH），不是元件 |
| **H2** | M2.5 安装孔（⌀2.7mm NPTH），不是元件 |
| **H3** | M2.5 安装孔（⌀2.7mm NPTH），不是元件 |
| **H4** | M2.5 安装孔（⌀2.7mm NPTH），不是元件 |
| **R24** | DNP，设计上默认不贴（0R DNP(旁路外接)） |
| **R25** | DNP，设计上默认不贴（0R DNP(旁路板载)） |
| **R30** | DNP，设计上默认不贴（1k DNP） |
| **R36** | DNP，设计上默认不贴（1k DNP） |
| **SW1** | 短接焊盘，用镊子短接，不贴件 |
| **SW2** | 短接焊盘，用镊子短接，不贴件 |
| **TP1** | 测试点焊盘，探针/飞线用，不贴件 |
| **TP2** | 测试点焊盘，探针/飞线用，不贴件 |
| **TP3** | 测试点焊盘，探针/飞线用，不贴件 |
| **TP4** | 测试点焊盘，探针/飞线用，不贴件 |
| **TP5** | 测试点焊盘，探针/飞线用，不贴件 |
| **TP6** | 测试点焊盘，探针/飞线用，不贴件 |
| **TP7** | 测试点焊盘，探针/飞线用，不贴件 |
| **ZP1** | DNP，设计上默认不贴（DNP 并-天线侧） |
| **ZP2** | DNP，设计上默认不贴（DNP 并-电台侧） |
