naizhao/Pilot-Kit-Box-ESP32-P4/hardware/expansion-board-v4/ASSEMBLY_MAP-V4.4.pdf

# Pilot Kit Expansion Board V4.4 Assembly Map — Powered Variant (Top View)

A

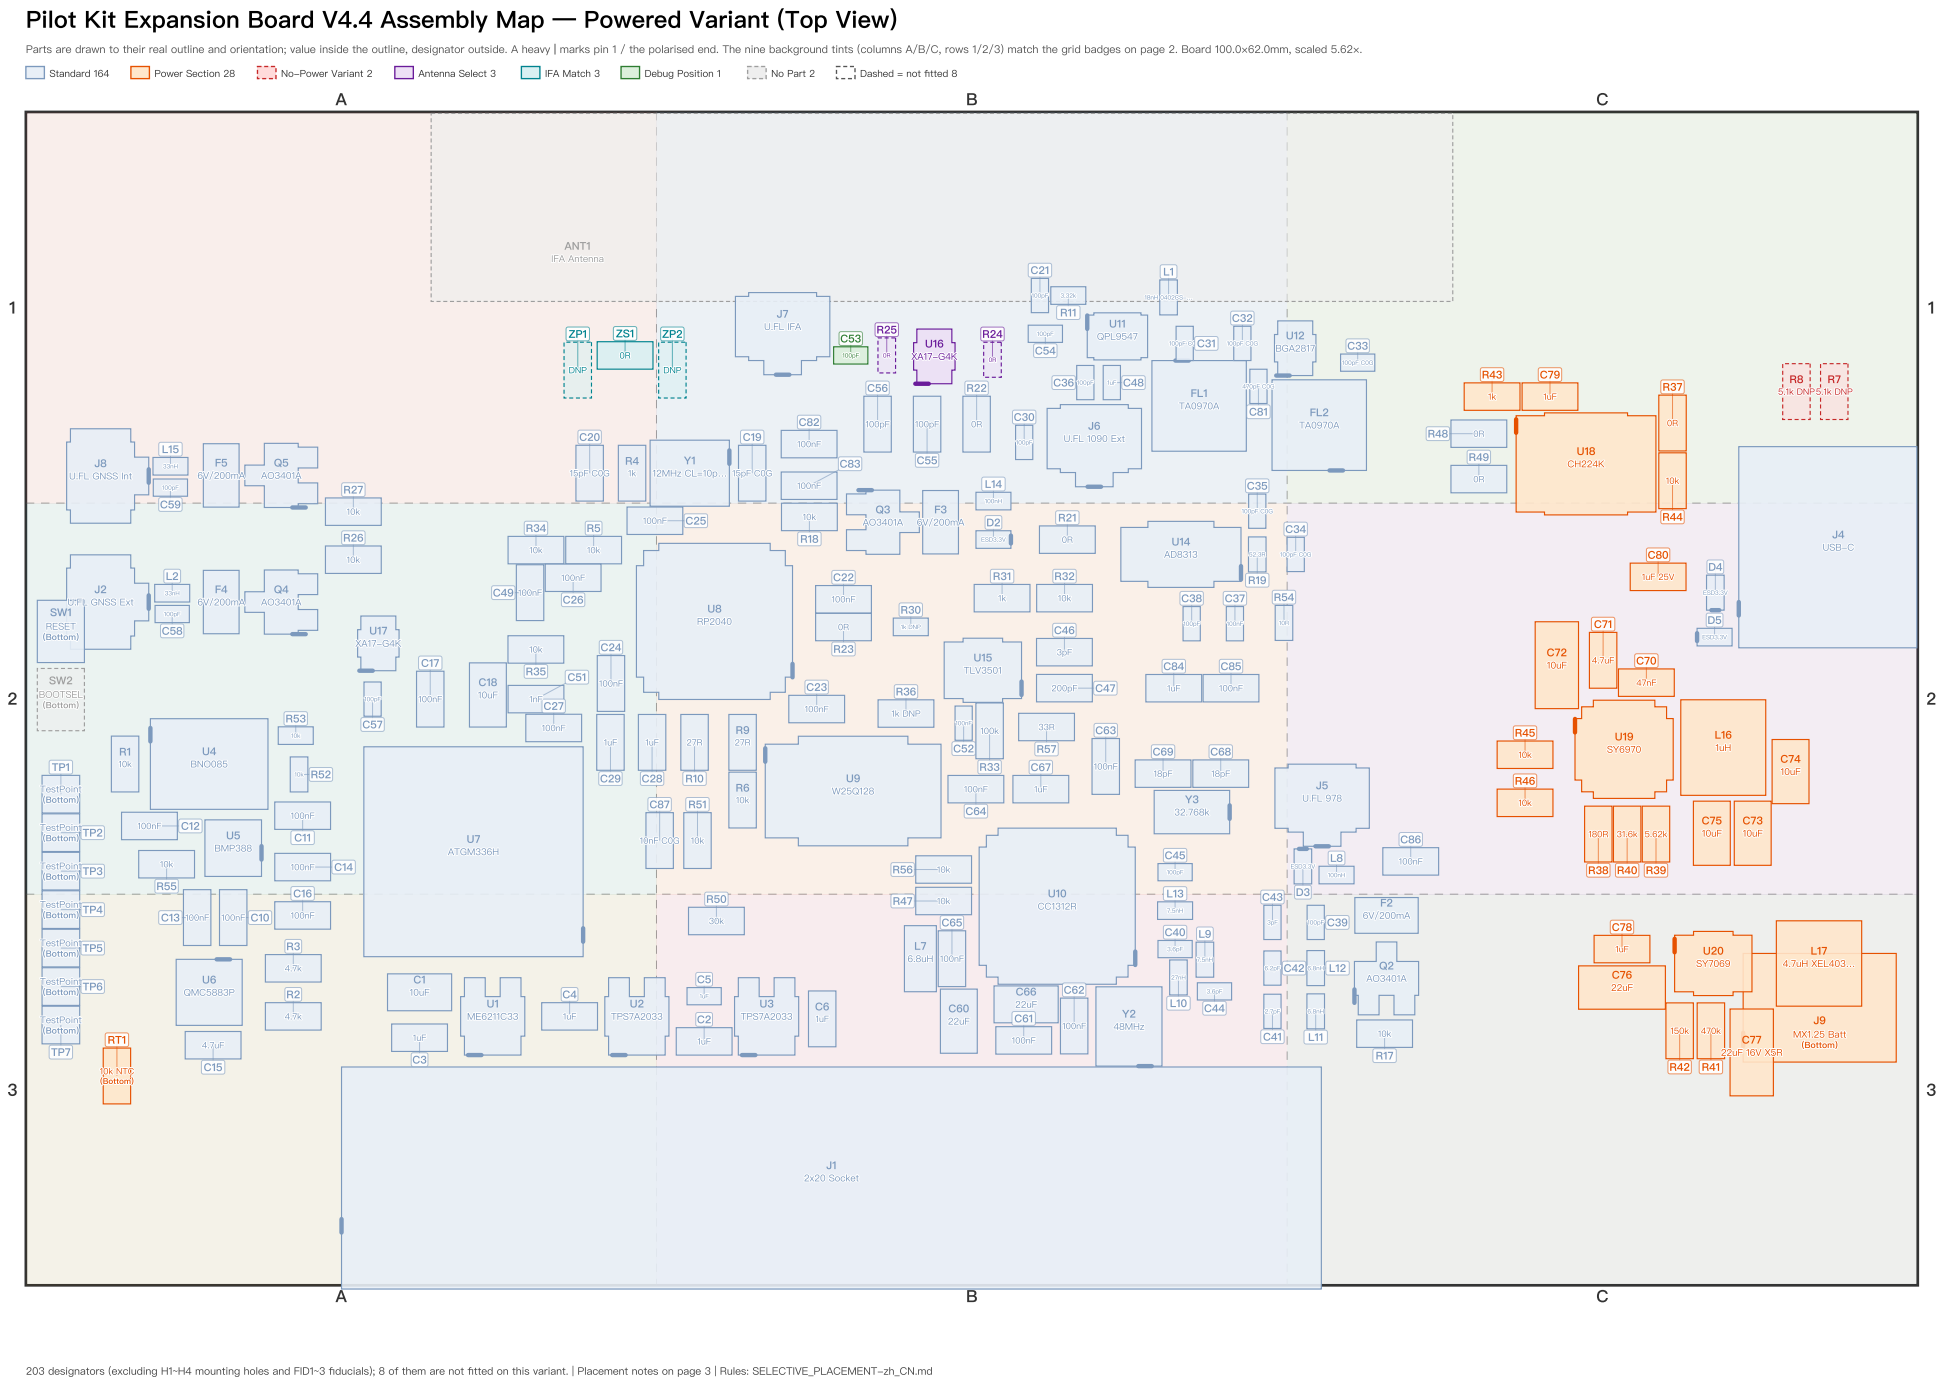
[picture p76: page 1]

Parts are drawn to their real outline and orientation; value inside the outline, designator outside. A heavy | marks pin 1 / the polarised end. The nine background tints (columns A/B/C, rows 1/2/3) match the grid badges on page 2. Board 100.0×62.0mm, scaled 5.62×.

U.FL GNSS Int

203 designators (excluding H1~H4 mounting holes and FID1~3 fiducials); 8 of them are not fitted on this variant. | Placement notes on page 3 | Rules: SELECTIVE_PLACEMENT-zh_CN.md

# Pilot Kit Expansion Board V4.4 Designator Index — Grid Reference

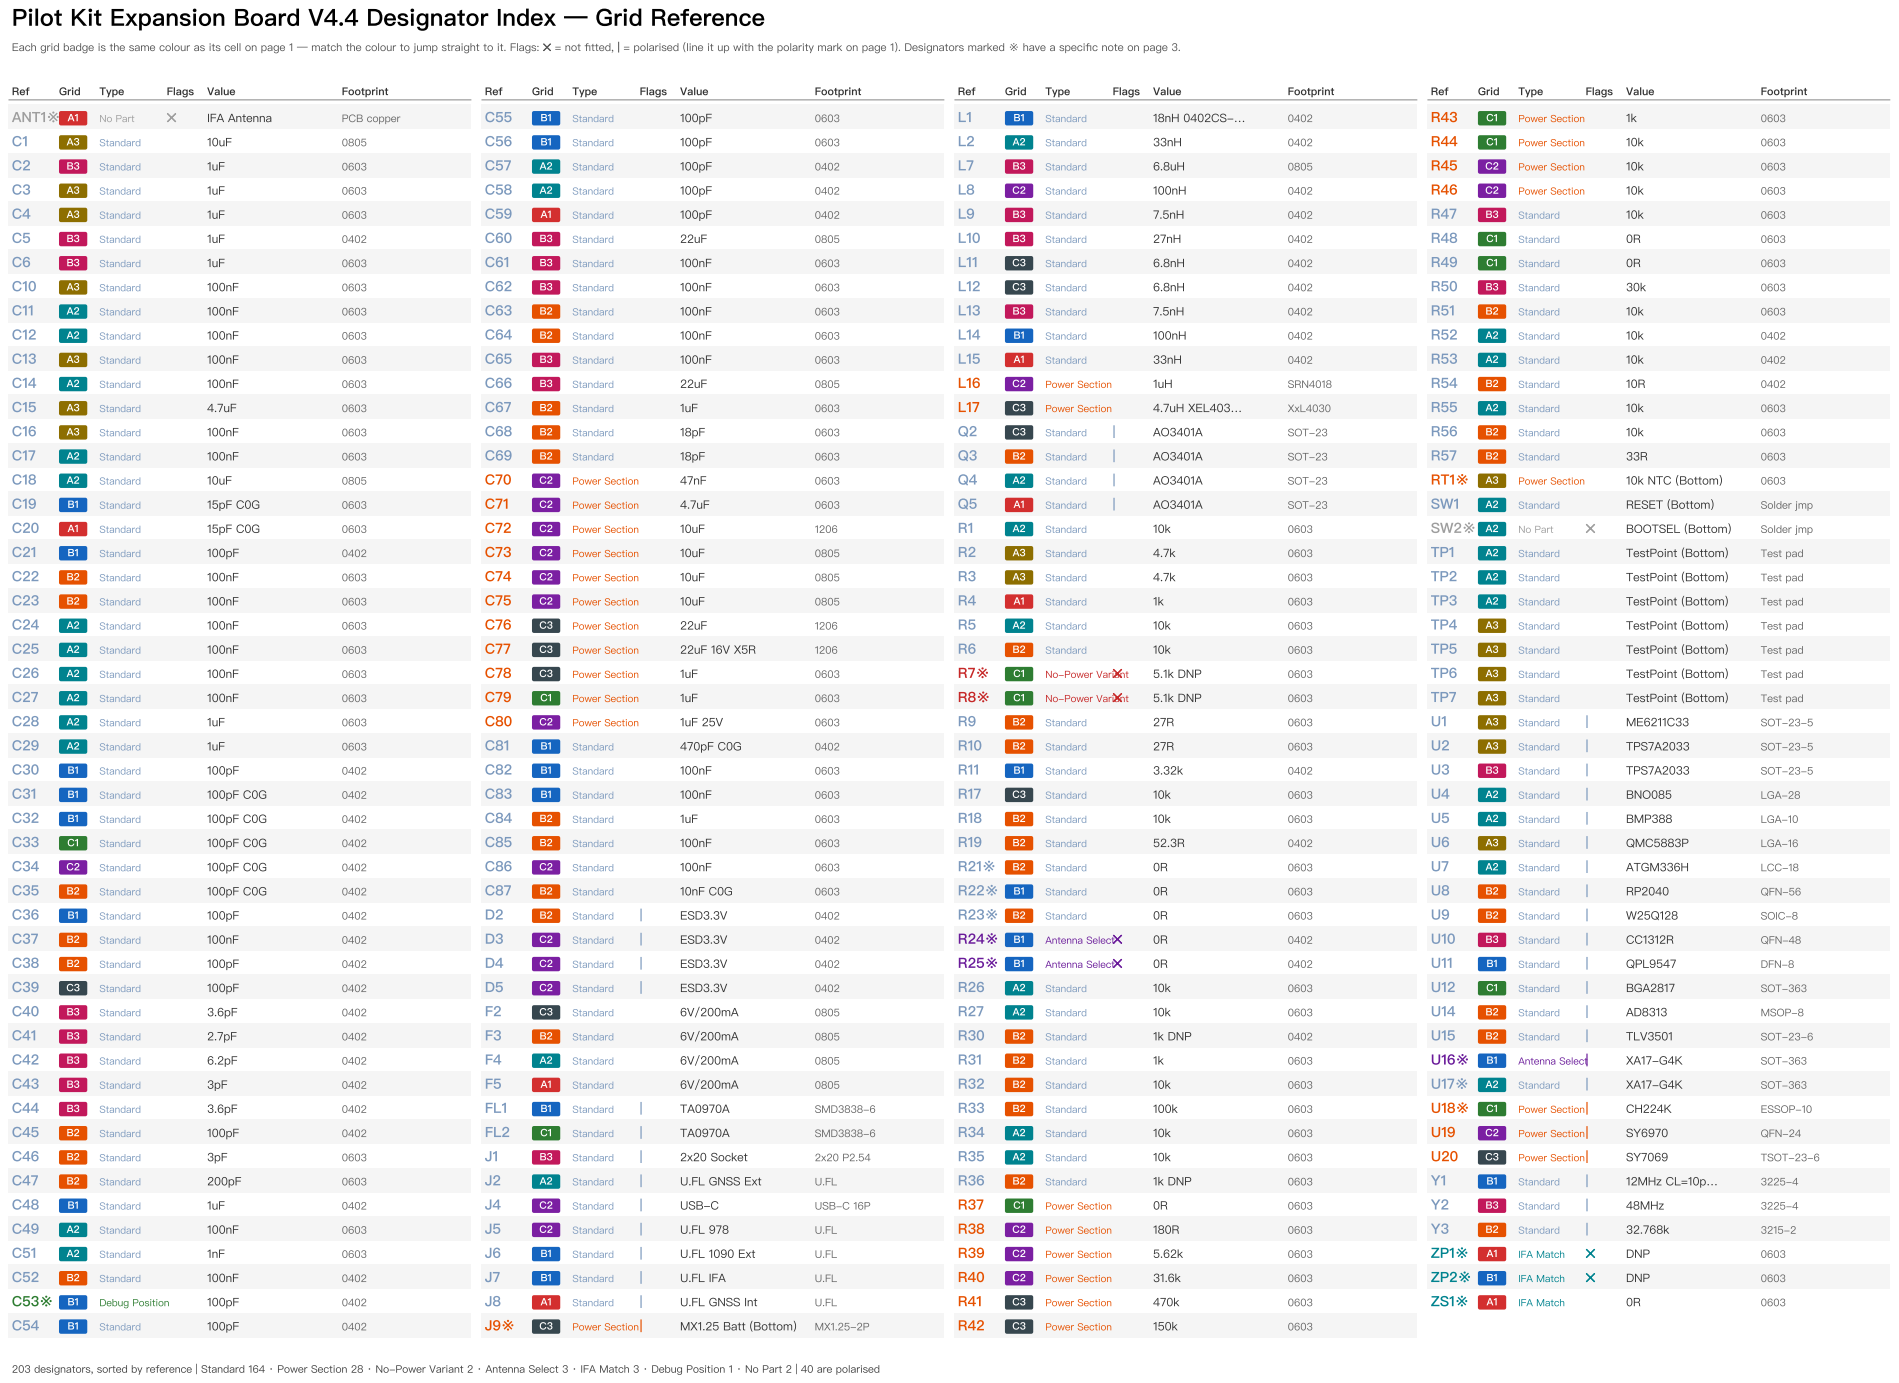
[picture p77: page 2]

Each grid badge is the same colour as its cell on page 1 — match the colour to jump straight to it. Flags: ✕ = not fitted, | = polarised (line it up with the polarity mark on page 1). Designators marked ※ have a specific note on page 3.

203 designators, sorted by reference | Standard 164 · Power Section 28 · No-Power Variant 2 · Antenna Select 3 · IFA Match 3 · Debug Position 1 · No Part 2 | 40 are polarised

# Pilot Kit Expansion Board V4.4 Selective Placement Notes

Standard parts are fitted unconditionally and are not listed here. Every class below carries a precondition; getting it wrong breaks the function or the board — full reasoning in SELECTIVE_PLACEMENT-zh_CN.md.

### No-Power Variant (2 parts, default here: DNP)

5.1k CC pull-downs, fitted on the no-power variant only. Together with U18 (CH224K) they skew the CC resistance, so PD negotiation may request 9V/12V into a board designed for 5V. Both sit i nside a NO-PWR VER silkscreen box.

### R7 5.1k DNP [DNP] Not fitted on this (powered) variant R8 5.1k DNP [DNP] Not fitted on this (powered) variant

### Antenna Select (3 parts, default here: See notes)

Three mutually exclusive ways to route the 1090 antenna path — fit at most one. R24+R25 together short the external antenna to the on-board IFA; U16 plus either bypass shorts a switch port.

### R24 0R [DNP] 0R bypass → hard-wires the external antenna; not fitted here R25 0R [DNP] 0R bypass → hard-wires the on-board IFA; not fitted here U16 XA17-G4K [Fit] RF switch (default option) — this is the one to fit

### IFA Match (3 parts, default here: See notes)

Pi matching network for the on-board IFA. The three positions combine freely into an L or pi network and are not exclusive. The default ZS1=0R is a straight-through link, not a tuned match — final values come from a VNA sweep with the enclosure fitted.

### ZP1 DNP [DNP] Shunt, antenna side; not fitted by default ZP2 DNP [DNP] Shunt, radio side; not fitted by default. First sweep starts at 3.3pF ZS1 0R [Fit] Series position, default 0R link; start the first sweep at 3.6nH

### Debug Position (1 parts, default here: Fit)

Normally fitted; removed only for one specific measurement.
C53 100pF [Fit] Remove before sweeping the IFA through J7, otherwise the VNA sees the switch and everything behind it instead of the antenna. Refit after

### Power Section (28 parts, default here: Fit)

Fitted on the powered variant only. On the no-power variant this whole group is omitted and R7/R8 are fitted instead.

### J9 MX1.25 Batt [Fit] Battery connector, on the bottom side RT1 10k NTC [Fit] NTC for battery temperature sensing, on the bottom side U18 CH224K [Fit] CH224K USB-C PD sink controller; it provides the CC pull-down internally

Others in this class: C70, C71, C72, C73, C74, C75, C76, C77, C78, C79, C80, L16, L17, R37, R38, R39, R40, R41, R42, R43, R44, R45, R46, U19, U20

### No Part (2 parts, default here: —)

Bare copper or a solder-bridge jumper — there is no part to fit.

### ANT1 IFA Antenna [DNP] The on-board IFA — it is the PCB copper itself SW2 BOOTSEL [DNP] BOOTSEL solder bridge, short it with tweezers; on the bottom side

### Standard (164 parts, default here: Fit)

This whole class is fitted unconditionally; only the few with an extra caveat are listed. The remaining 160 just get fitted.

### R21 0R [Fit] 0R link; open it to probe the AD8313 detector output on its own R22 0R [Fit] 0R link; open it to drive the 1090 switch A pin by hand R23 0R [Fit] 0R link; open it to drive the 1090 switch B pin by hand

U17 XA17-G4K [Fit] GNSS-side RF switch. There is no bypass resistor on this side, so leaving it out means no signal path at all

### Rules: SELECTIVE_PLACEMENT-zh_CN.md | This board: powered variant
