naizhao/Pilot-Kit-Box-ESP32-P4/hardware/expansion-board-v4/ASSEMBLY_MAP-V4.4-zh_CN.pdf

## Pilot Kit 扩展板 V4.4 装配图 —— 带电源版（顶层视角）

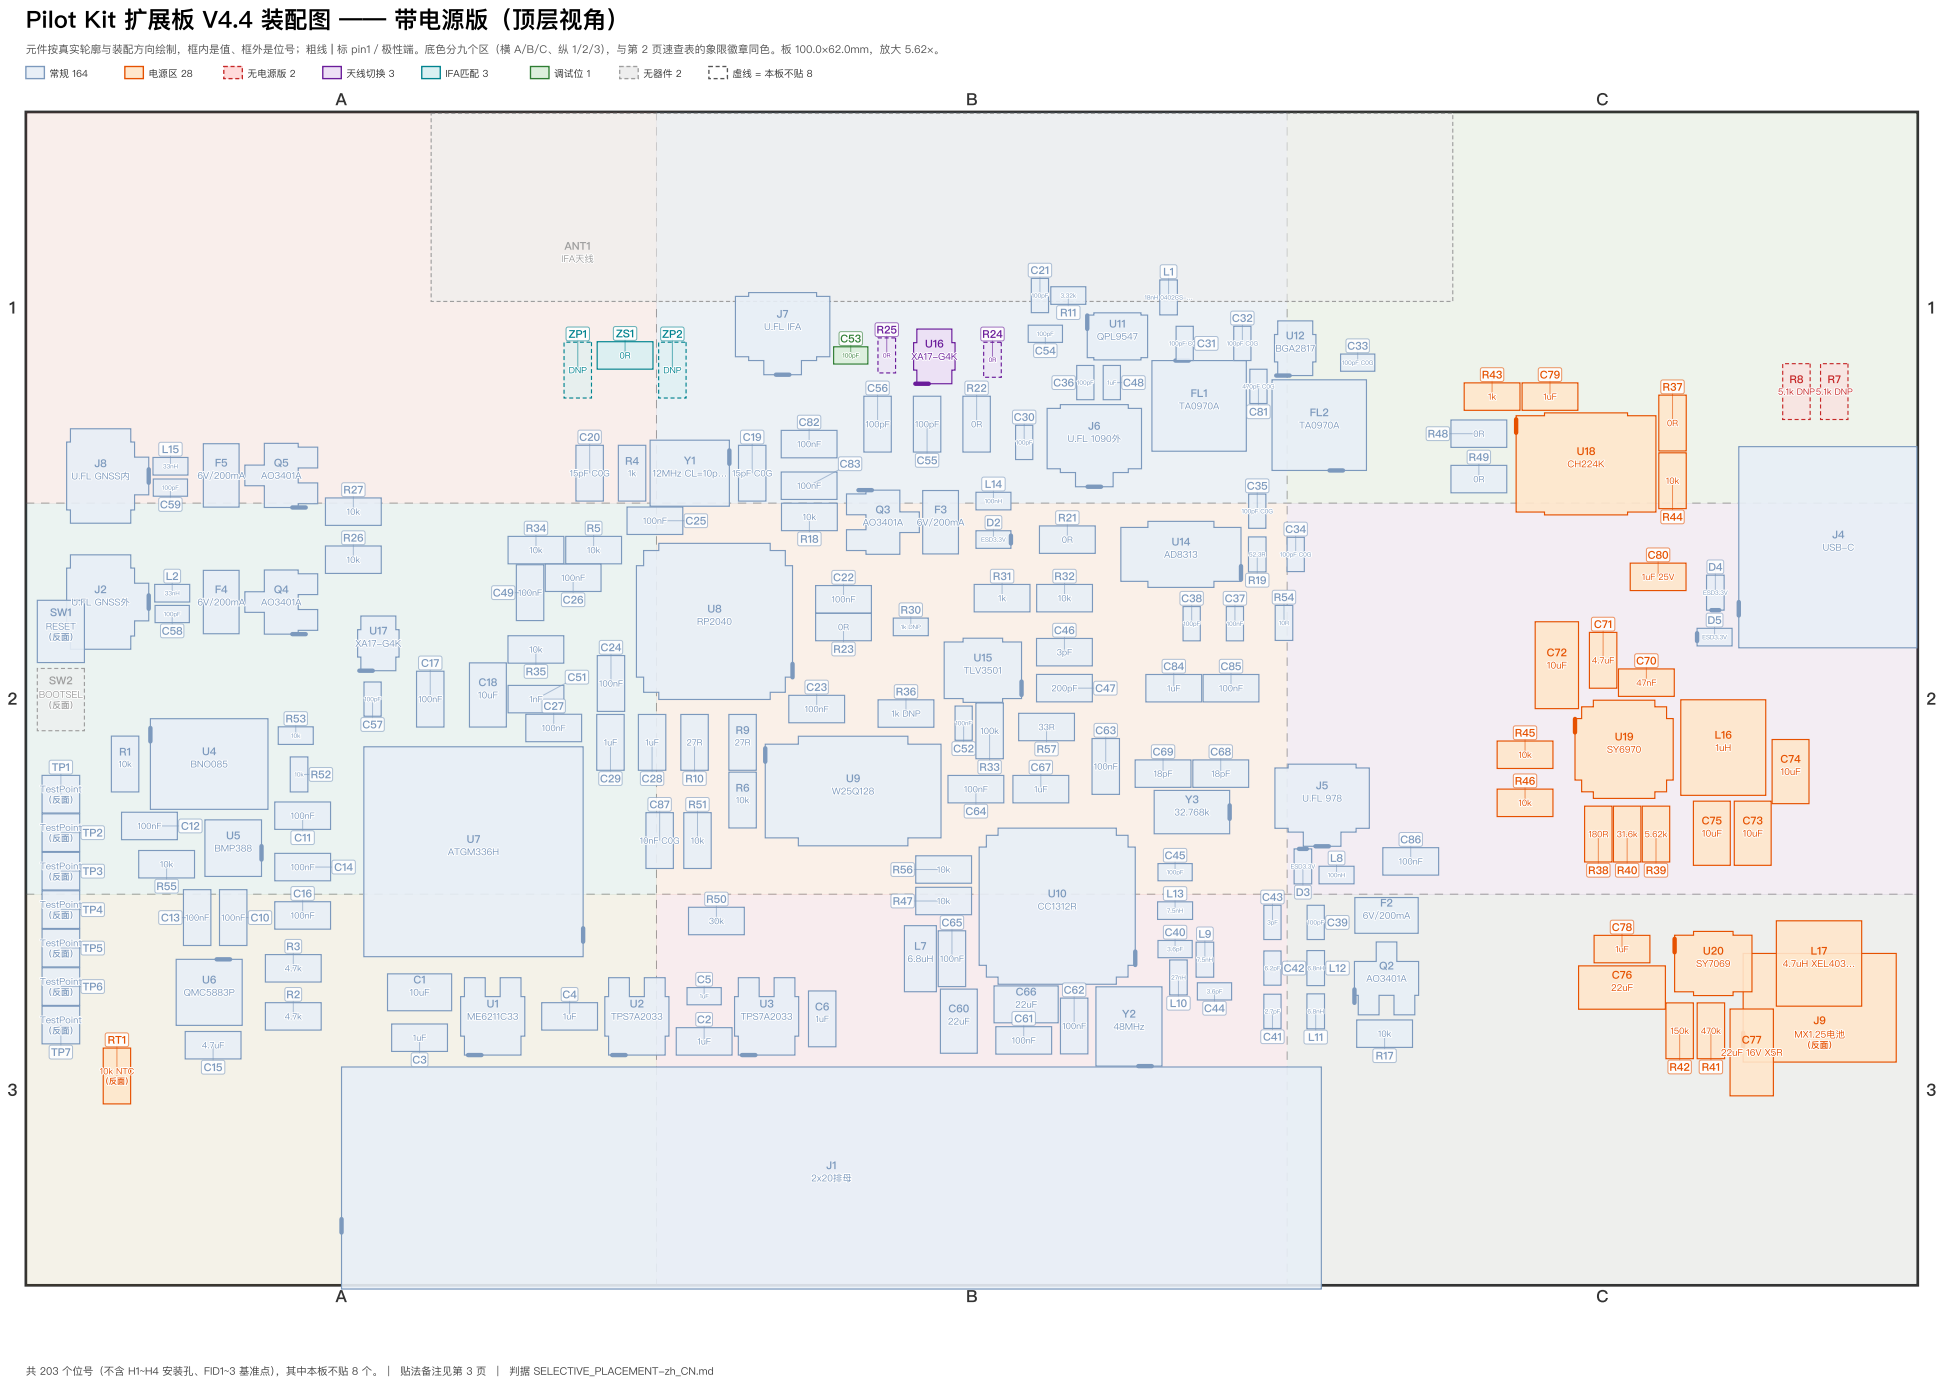
[picture p94: page 1]

元件按真实轮廓与装配方向绘制，框内是值、框外是位号；粗线 | 标 pin1／极性端。底色分九个区（横 A/B/C、纵 1/2/3），与第 2 页速查表的象限徽章同色。板 100.0×62.0mm，放大 5.62×。

## Pilot Kit 扩展板 V4.4 位号速查表 —— 象限对照

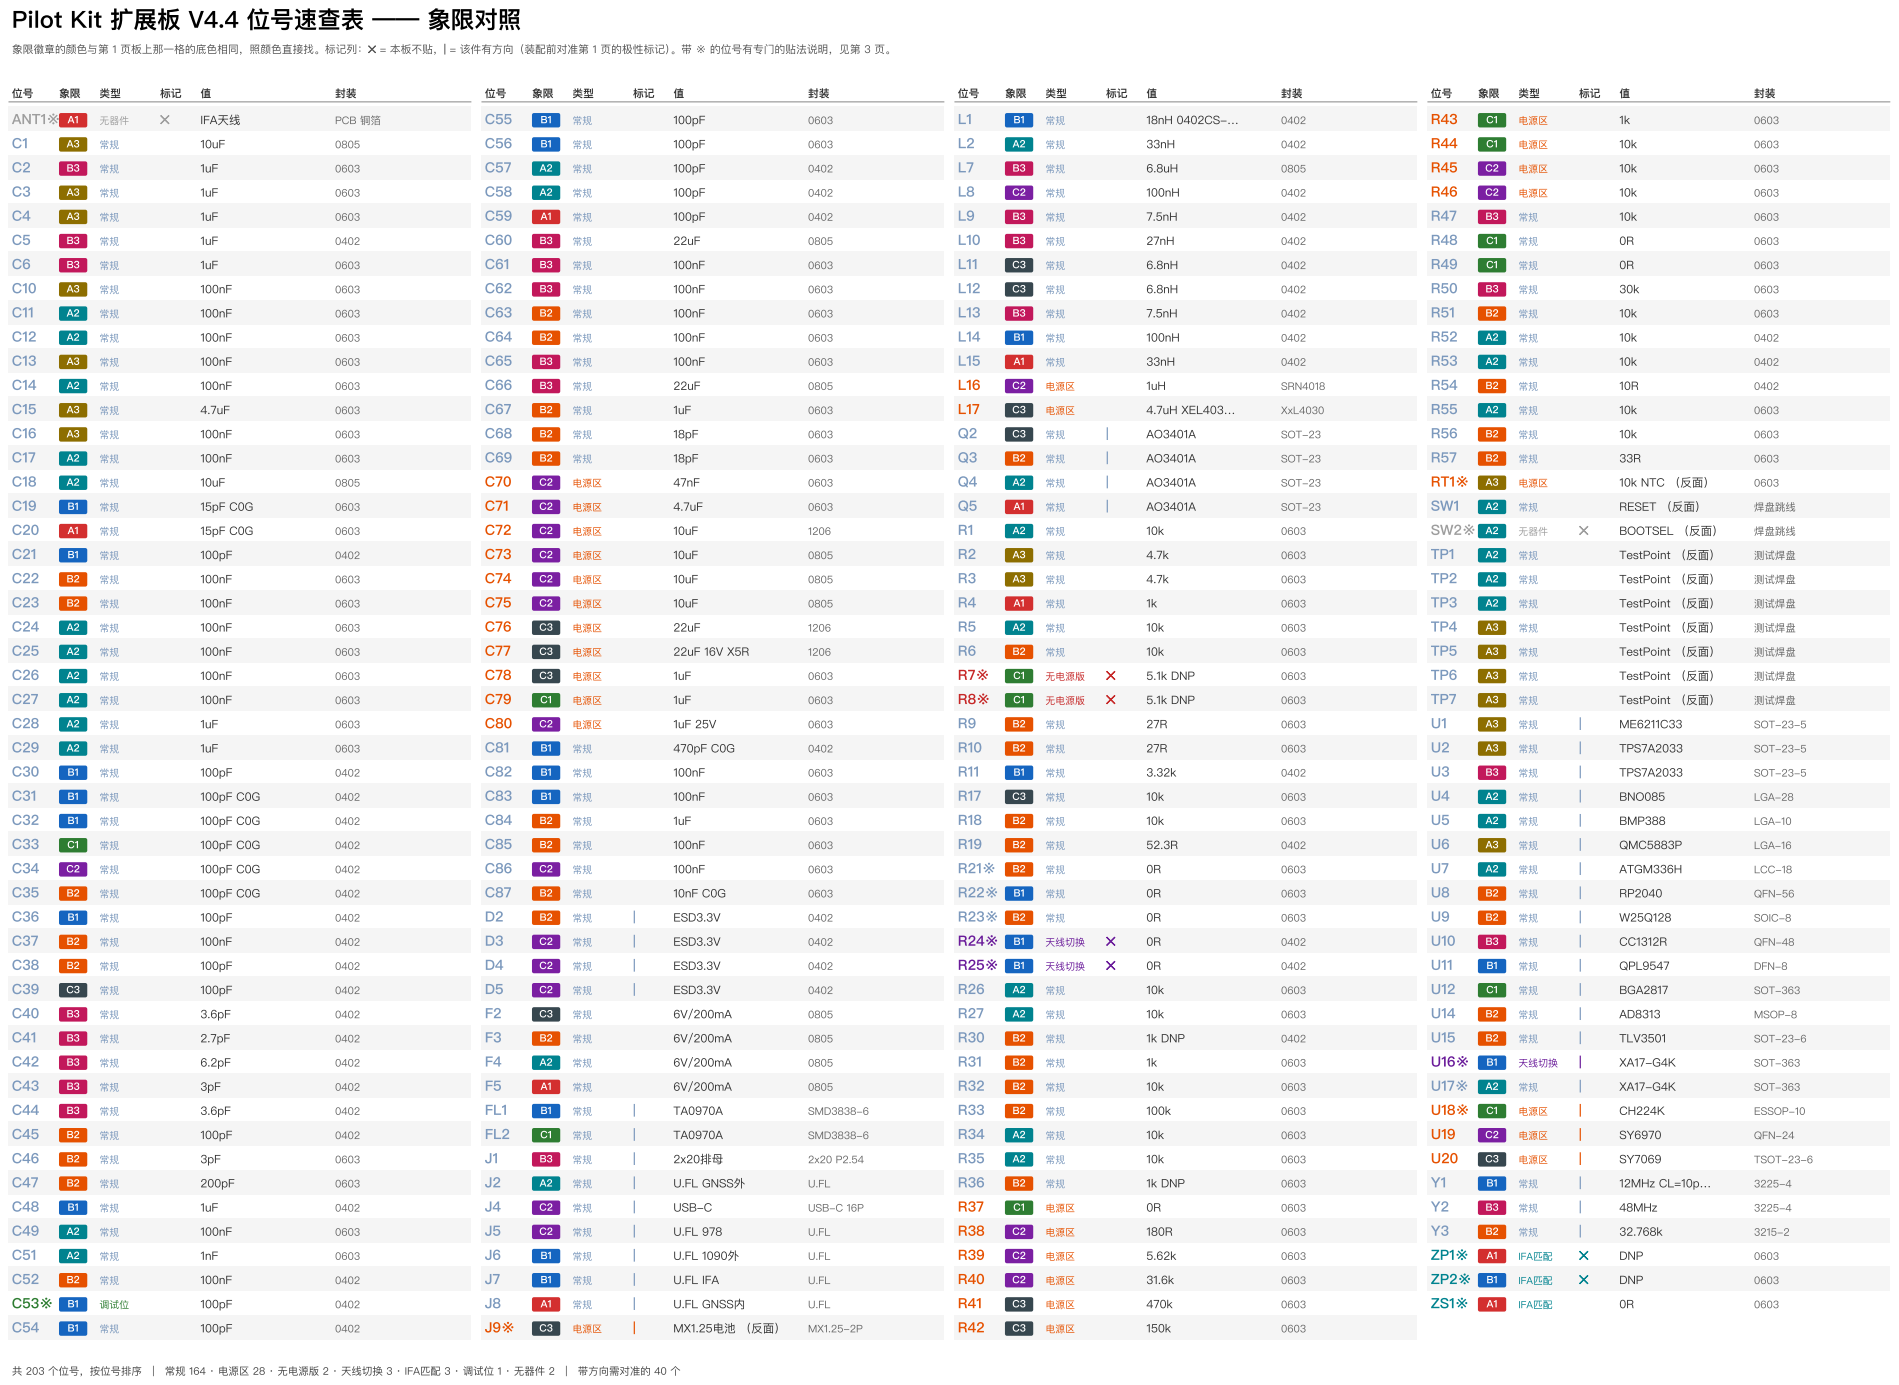
[picture p95: page 2]

象限徽章的颜色与第 1 页板上那一格的底色相同，照颜色直接找。标记列：✕ = 本板不贴，| = 该件有方向（装配前对准第 1 页的极性标记）。带 ※ 的位号有专门的贴法说明，见第 3 页。

共 203 个位号，按位号排序 | 常规 164 · 电源区 28 · 无电源版 2 · 天线切换 3 · IFA匹配 3 · 调试位 1 · 无器件 2 | 带方向需对准的 40 个

## Pilot Kit 扩展板 V4.4 特殊贴装说明

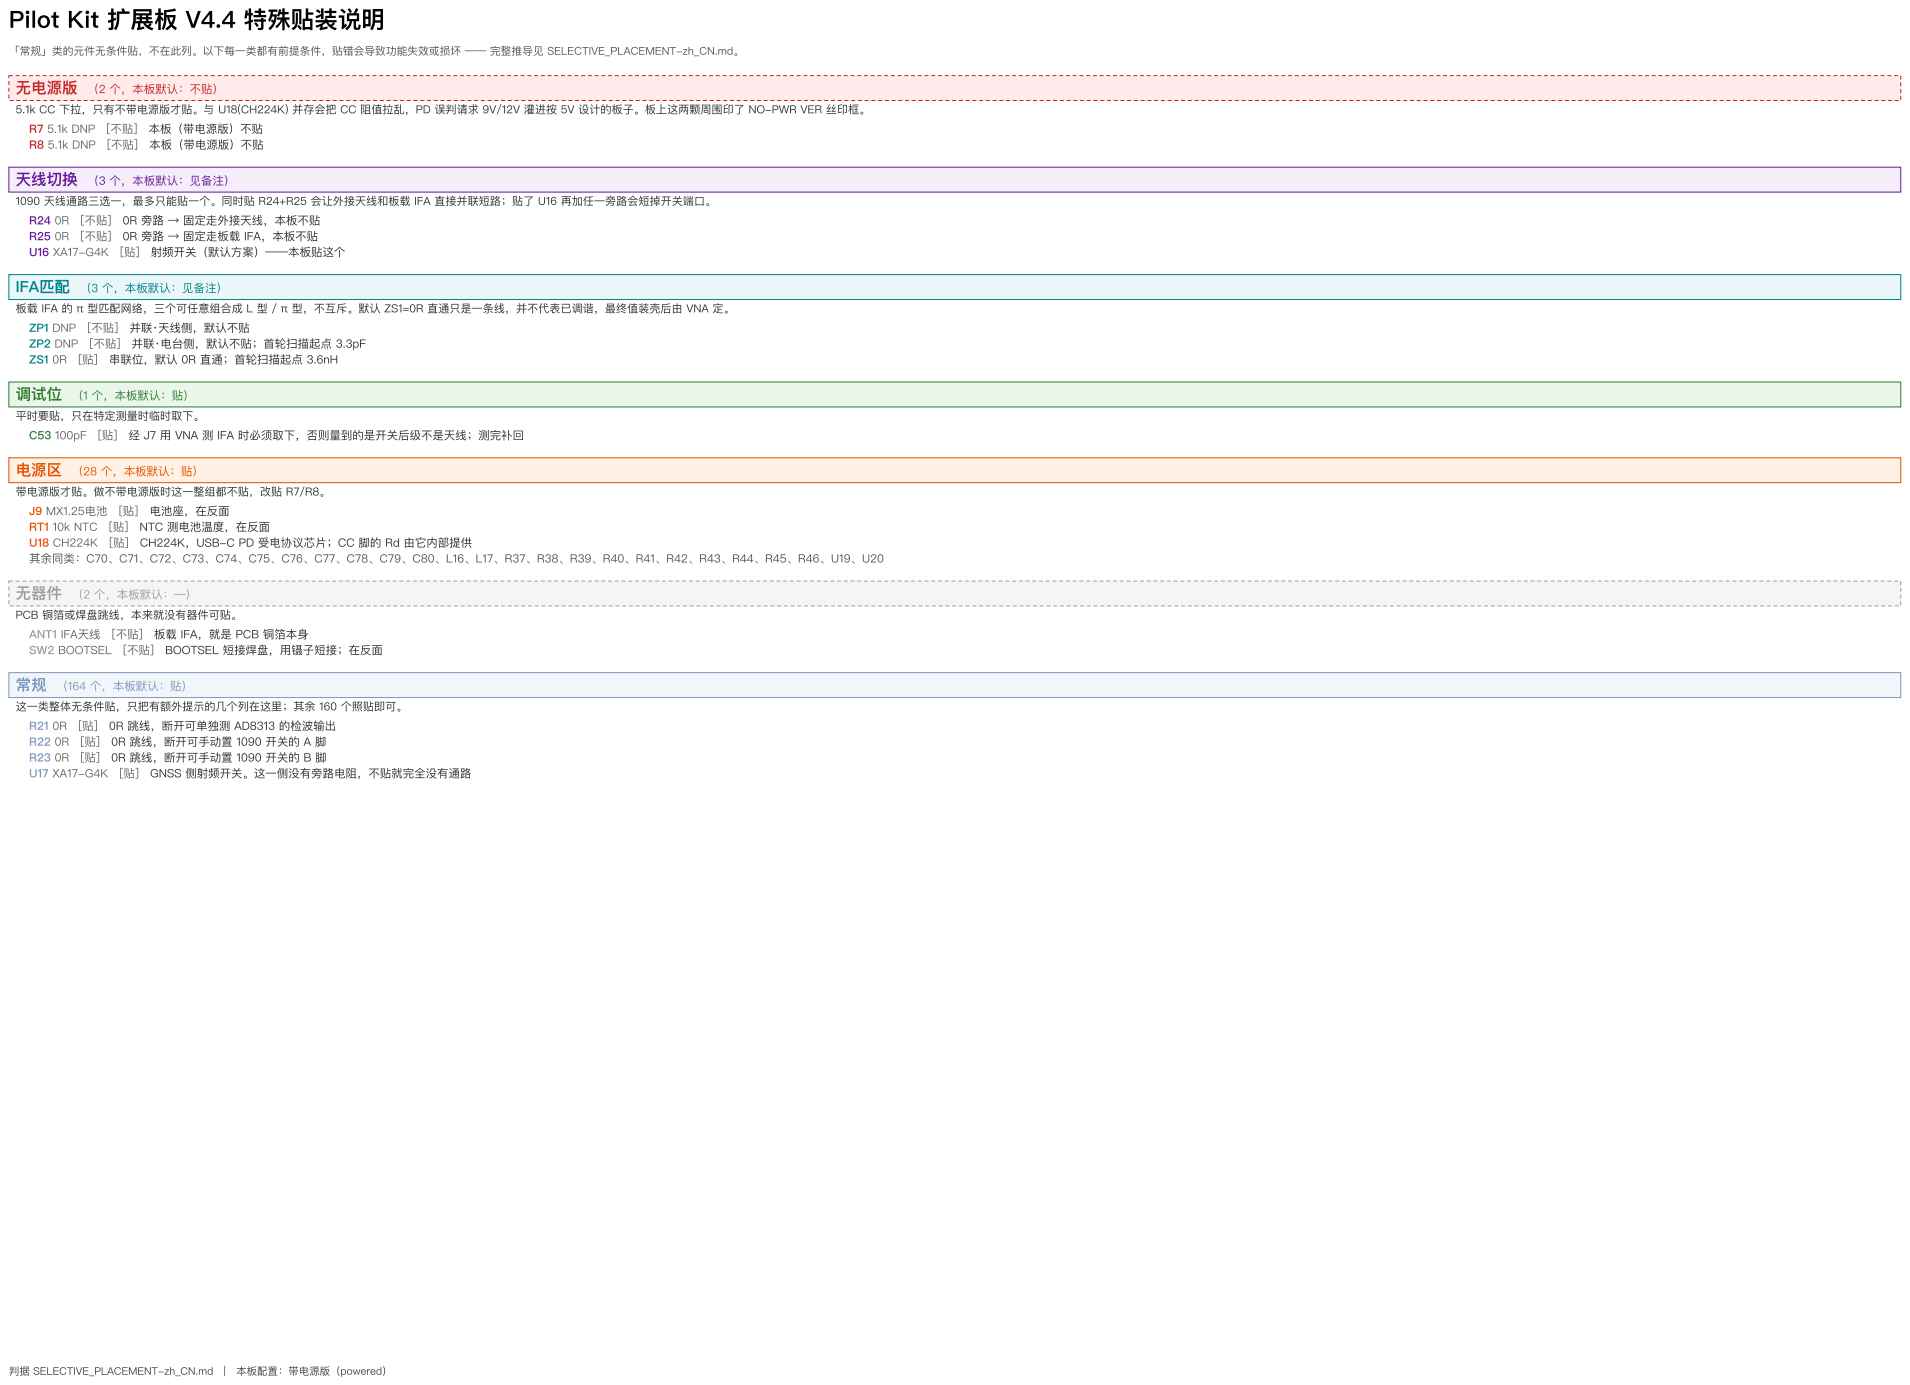
[picture p96: page 3]

5.1k CC 下拉，只有不带电源版才贴。与 U18(CH224K) 并存会把 CC 阻值拉乱，PD 误判请求 9V/12V 灌进按 5V 设计的板子。板上这两颗周围印了 NO-PWR VER 丝印框。
R7 5.1k DNP [不贴] 本板（带电源版）不贴
R8 5.1k DNP [不贴] 本板（带电源版）不贴

1090 天线通路三选一，最多只能贴一个。同时贴 R24+R25 会让外接天线和板载 IFA 直接并联短路；贴了 U16 再加任一旁路会短掉开关端口。
R24 0R [不贴] 0R 旁路 → 固定走外接天线，本板不贴
R25 0R [不贴] 0R 旁路 → 固定走板载 IFA，本板不贴
U16 XA17-G4K [贴] 射频开关（默认方案）——本板贴这个

板载 IFA 的 π 型匹配网络，三个可任意组合成 L 型 / π 型，不互斥。默认 ZS1=0R 直通只是一条线，并不代表已调谐，最终值装壳后由 VNA 定。
ZP1 DNP [不贴] 并联·天线侧，默认不贴
ZP2 DNP [不贴] 并联·电台侧，默认不贴；首轮扫描起点 3.3pF
ZS1 0R [贴] 串联位，默认 0R 直通；首轮扫描起点 3.6nH

平时要贴，只在特定测量时临时取下。
C53 100pF [贴] 经 J7 用 VNA 测 IFA 时必须取下，否则量到的是开关后级不是天线；测完补回

带电源版才贴。做不带电源版时这一整组都不贴，改贴 R7/R8。
J9 MX1.25电池 [贴] 电池座，在反面
RT1 10k NTC [贴] NTC 测电池温度，在反面
U18 CH224K [贴] CH224K，USB-C PD 受电协议芯片；CC 脚的 Rd 由它内部提供
其余同类：C70、C71、C72、C73、C74、C75、C76、C77、C78、C79、C80、L16、L17、R37、R38、R39、R40、R41、R42、R43、R44、R45、R46、U19、U20

PCB 铜箔或焊盘跳线，本来就没有器件可贴。
ANT1 IFA天线 [不贴] 板载 IFA，就是 PCB 铜箔本身
SW2 BOOTSEL [不贴] BOOTSEL 短接焊盘，用镊子短接；在反面

这一类整体无条件贴，只把有额外提示的几个列在这里；其余 160 个照贴即可。
R21 0R [贴] 0R 跳线，断开可单独测 AD8313 的检波输出
R22 0R [贴] 0R 跳线，断开可手动置 1090 开关的 A 脚
R23 0R [贴] 0R 跳线，断开可手动置 1090 开关的 B 脚
U17 XA17-G4K [贴] GNSS 侧射频开关。这一侧没有旁路电阻，不贴就完全没有通路

判据 SELECTIVE_PLACEMENT-zh_CN.md | 本板配置：带电源版（powered）
