naizhao/Pilot-Kit-Box-ESP32-P4/hardware/expansion-board-v3/render/assembly-top.pdf

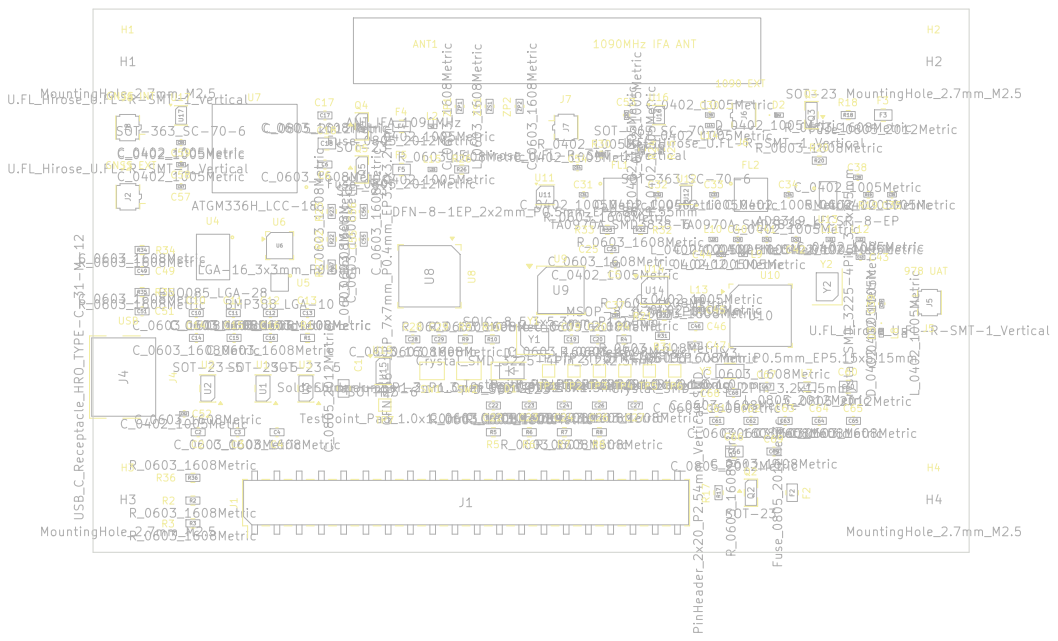
[picture p98: page 1]

Size: A4 | Rev:
KiCad E.D.A. 10.0.4 | Id: 1/1
