naizhao/Pilot-Kit-Box-ESP32-P4/firmware/main/imu_task.c

/*
 * imu_task.c — BNO085 minimal SH-2 client + 100 Hz attitude polling.
 *
 * SH-2 / SHTP framing summary (for the I²C transport):
 *
 *   ┌──────────┬──────────┬─────────┬──────┬────────────┐
 *   │ len LSB  │ len MSB  │ channel │ seq# │   cargo …  │
 *   └──────────┴──────────┴─────────┴──────┴────────────┘
 *      0           1           2        3        4..
 *
 *   - length is total frame size including the 4 header bytes
 *   - bit 15 of len MSB is the "continuation" flag (we don't see it
 *     for any reports we use, so it's safe to mask off)
 *   - channels we care about:
 *       0: command (advertisement / reset on boot)
 *       1: executable (reset complete, etc.)
 *       2: control   (Set/Get Feature Command, Feature Response)
 *       3: sensorhub (input reports — the actual sensor data)
 *
 * We send exactly one Set Feature Command on channel 2 (enable
 * Rotation Vector at 100 Hz) and then drain reports off channel 3.
 * Everything else BNO085 sends is logged at DEBUG and dropped.
 *
 * References:
 *   - Hillcrest / CEVA SH-2 Reference Manual (Sensor Hub Protocol)
 *   - SparkFun BNO080_Arduino_Library (MIT licensed reference)
 *   - Bosch / Hillcrest BNO080 datasheet 1000-3251 rev 1.10
 */

#include "imu_task.h"

#include "config_demo.h"   /* pk_demo_enabled —— 演示模式接管姿态数据源 */
#include "demo_data.h"
#include "pk_i2c0_bus.h"      /* I²C0 总线已上移为板级模块（bus handle 来源） */
#include "pk_i2c0_recover.h"  /* 总线级恢复：坏的是总线时 bno_bring_up 救不回来 */
#include "pk_bringup_retry.h" /* 必装器件的开机 bring-up 退避重试（见该头文件的病因） */
#include "pk_board.h"      /* 板型 profile：V3.9/V4.3 的 BNO085 安装变换不同 */
#include "pk_vib.h"        /* vib_level：加速度模长滑动窗口 RMS */

#include <math.h>
#include <string.h>

#include "freertos/FreeRTOS.h"
#include "freertos/task.h"
#include "freertos/semphr.h"
#include "esp_attr.h"      /* EXT_RAM_BSS_ATTR */
#include "esp_log.h"
#include "esp_timer.h"
#include "driver/i2c_master.h"
#include "driver/gpio.h"
#include "nvs.h"
#include "nvs_flash.h"

static const char *TAG = "imu";

/* --- Hardware wiring (mirrors docs/hardware/board_pinout.md) --------- */
/* I²C0 总线（SDA GPIO7 / SCL GPIO8，400 kHz）的创建已上移到板级模块
 * pk_i2c0_bus.c；这里只剩器件自己的地址与 RST/INT 引脚。 */
#define IMU_I2C_HZ               400000
#define IMU_I2C_ADDR             0x4A
#define IMU_PIN_INT              34    /* J3 Pin 28 = GPIO34 (JLC PCB net IMU_INT); current driver polls, INT unused */
#define IMU_PIN_RST              28    /* moved to J3 Pin 16 (upper) for PCB routing */

/* --- SH-2 constants -------------------------------------------------- */
#define SHTP_CH_COMMAND          0
#define SHTP_CH_EXECUTABLE       1
#define SHTP_CH_CONTROL          2
#define SHTP_CH_SENSORHUB        3
#define SHTP_HEADER_LEN          4
#define SHTP_MAX_PAYLOAD         128   /* plenty for Rotation Vector + slack */

#define SH2_CMD_SET_FEATURE      0xFD
#define SH2_CMD_REQUEST          0xF2
#define SH2_CMD_RESPONSE         0xF1   /* 芯片对 0xF2 的回执，走控制通道 */
#define SH2_REPORT_ROTATION_VECTOR      0x05
#define SH2_REPORT_LINEAR_ACCELERATION  0x04  /* gravity already removed by SH-2 */
#define SH2_REPORT_MAGNETIC_FIELD       0x03  /* calibrated mag field, Q16 (µT = raw/16) */

/* SH-2 Command Request codes (sent inside a 0xF2 report on the
 * control channel). See SH-2 Reference Manual §6.4. */
#define SH2_COMMAND_TARE         0x03
#define SH2_COMMAND_SAVE_DCD     0x06
#define SH2_COMMAND_CLEAR_DCD    0x0B   /* "Clear Persistent DCD" —
                                           wipes mag/gyro/accel
                                           calibration data from
                                           BNO085 internal flash so
                                           the fusion engine starts
                                           fresh on the next
                                           initialisation. */

/* Tare command (0x03) p0 subcommand values. */
#define SH2_TARE_SUB_NOW         0x00
#define SH2_TARE_SUB_PERSIST     0x01

/* Tare Now (subcommand 0x00) p1 axes mask — OR these together. */
#define SH2_TARE_AXIS_X          0x01
#define SH2_TARE_AXIS_Y          0x02
#define SH2_TARE_AXIS_Z          0x04
#define SH2_TARE_AXIS_ALL        (SH2_TARE_AXIS_X | SH2_TARE_AXIS_Y | SH2_TARE_AXIS_Z)

/* Tare Now (subcommand 0x00) p2 basis rotation vector to tare against. */
#define SH2_TARE_BASIS_ROT_VEC   0x00

/* Set Feature Command payload layout — 17 bytes (see SH-2 ref §6.5.4). */
typedef struct __attribute__((packed)) {
    uint8_t  report_id;          /* 0xFD */
    uint8_t  feature_id;         /* 0x05 = Rotation Vector */
    uint8_t  feature_flags;      /* 0 */
    int16_t  change_sensitivity; /* 0 */
    uint32_t report_interval_us; /* 10000 = 100 Hz */
    uint32_t batch_interval_us;  /* 0 */
    uint32_t sensor_specific;    /* 0 */
} sh2_set_feature_t;

/* 罗盘航向固定修正（度）。
 *
 * 2026-09-11 用户实机四点标定（V4 竖放，各指向已知朝向读屏上 yaw）：
 *   加 +90 修正后：东90→170(+80)、南180→245(+65)、西270→345(+75)
 * 三点误差均值 +73°、散差 ±8° → 真实固定偏差 ≈ -17°（接近磁偏/硬铁偏置，
 * 不是 90/180 的整倍数，排除安装轴错误）。故取 +17 居中；残余 ±8° 散差
 * 是磁场干扰，需从磁源/位置解决（见日志 |B|，地球 ~45uT）。
 *
 * 待办：这是固定补偿，不是真校准；磁校准能落盘后应改回 0 并靠 DCD。 */
#define IMU_YAW_OFFSET_DEG  17.0f

/* --- Module state ---------------------------------------------------- */
static i2c_master_dev_handle_t    s_dev;
static SemaphoreHandle_t          s_sample_lock;
static pk_imu_sample_t            s_sample;
static uint8_t                    s_tx_seq[6];   /* per-channel SHTP sequence */
static uint8_t                    s_cmd_seq;     /* SH-2 Command Request sequence */

/* 芯片握过手、并且真的出过一条 Rotation Vector 才算 ready。
 *
 * 这面旗的含义在 2026-09-09 收紧过：bring-up 挪进 imu 任务之后，
 * pk_imu_init() 返回 ESP_OK 只证明"任务建起来了"，不证明 BNO085 回话。若
 * 仍拿 init 成功当 ready，退避重试期间按 TARE 会把默认单位四元数当成"当前
 * 姿态"存进 NVS（下次开机地平线偏着），FACTORY RESET 更会在另一个任务里发
 * SH-2 命令，与 imu 任务正在跑的 bring-up 并发写 s_dev / s_tx_seq / s_cmd_seq。
 * 判据因此改成"收到过有效姿态"，置位点在 parse_rotation_vector()。
 *
 * 置 true 之后不再清零：瞬时 stall 期间用户按 TARE 仍然应该有效（下一帧就
 * 生效），把按键做成时灵时不灵比拒绝一次更糟。
 * volatile：写在 imu 任务，读在 UI 任务。 */
static volatile bool              s_imu_ready;

/* Vibration-RMS sliding window — fed from parse_linear_acceleration(),
 * consumed via pk_vib_level() into s_sample.vib_level. Only the 50
 * floats actually used cost anything at runtime, but the struct itself
 * (PK_VIB_BUF_CAP=64 floats + bookkeeping, ~264 B) still goes to PSRAM:
 * internal DRAM headroom on this target is thin (see aircraft_state.c /
 * aircraft_db.c for the same convention). */
static EXT_RAM_BSS_ATTR pk_vib_state_t s_vib;

/* Last raw quaternion from the BNO — stashed for the 1 Hz diagnostic
 * log only. Volatile because the 1 Hz logger reads it from the imu
 * task itself; torn reads only cause a one-frame skew in the printout,
 * not a correctness issue. */
static volatile float             s_last_raw_qw, s_last_raw_qi, s_last_raw_qj, s_last_raw_qk;

/* Last post-sandwich, pre-tare-offset aircraft quaternion. Captured
 * every frame so pk_imu_tare_now() can snapshot "current attitude"
 * without rerunning the sandwich math. Protected by s_sample_lock. */
static float                      s_last_aircraft_qw = 1.0f,
                                  s_last_aircraft_qi = 0.0f,
                                  s_last_aircraft_qj = 0.0f,
                                  s_last_aircraft_qk = 0.0f;

/* Software tare offset — LEFT-multiplied onto the post-sandwich
 * quaternion every frame (q_displayed = s_tare · q_aircraft).
 * Identity = no offset. Set by pk_imu_tare_now() /
 * pk_imu_tare_persist() to the conjugate (= inverse, for a unit
 * quaternion) of the current post-sandwich attitude, so the
 * displayed quaternion is identity at the moment of tare. Left-mul
 * decomposes the differential in the tare-time aircraft body frame,
 * matching the aerospace convention for ZYX roll/pitch/yaw — see the
 * detailed rationale in parse_rotation_vector() at the multiplication
 * call site. Protected by s_sample_lock. */
static float                      s_tare_qw = 1.0f,
                                  s_tare_qi = 0.0f,
                                  s_tare_qj = 0.0f,
                                  s_tare_qk = 0.0f;

/* NVS keys — namespace + blob key for the persisted software tare.
 * Blob layout: 4 little-endian IEEE 754 floats in (w, x, y, z) order. */
#define IMU_NVS_NAMESPACE   "pk_imu"
#define IMU_NVS_KEY_TARE    "tare_quat"

/* Forward declarations for NVS helpers used by pk_imu_init() before
 * the definitions further down. */
static esp_err_t imu_nvs_load_tare(float *w, float *x, float *y, float *z);
static esp_err_t imu_nvs_save_tare(float w, float x, float y, float z);
static esp_err_t imu_nvs_erase_tare(void);

/* --- I²C device attach ------------------------------------------------ *
 *
 * 总线本身由板级模块 pk_i2c0_bus 在 app_main 最前面创建（所有权移交见
 * pk_i2c0_bus.h）——IMU init 失败不再连带总线消失，optional 器件缺失 ≠
 * 总线故障。这里只把 BNO085 挂上去；bus == NULL 说明启动次序被人动过
 * （pk_i2c0_bus_init 没跑或失败了），报错给人看。 */
static esp_err_t i2c_add_device(void)
{
    i2c_master_bus_handle_t bus = pk_i2c0_bus_get();
    if (bus == NULL) return ESP_ERR_INVALID_STATE;

    const i2c_device_config_t dev_cfg = {
        .dev_addr_length = I2C_ADDR_BIT_LEN_7,
        .device_address = IMU_I2C_ADDR,
        .scl_speed_hz = IMU_I2C_HZ,
    };
    return i2c_master_bus_add_device(bus, &dev_cfg, &s_dev);
}

/* --- BNO085 hard reset ----------------------------------------------- */
static void bno_reset_pulse(void)
{
    const gpio_config_t io = {
        .pin_bit_mask = (1ULL << IMU_PIN_RST),
        .mode = GPIO_MODE_OUTPUT,
        .pull_up_en = GPIO_PULLUP_DISABLE,
        .pull_down_en = GPIO_PULLDOWN_DISABLE,
        .intr_type = GPIO_INTR_DISABLE,
    };
    gpio_config(&io);
    gpio_set_level(IMU_PIN_RST, 0);
    vTaskDelay(pdMS_TO_TICKS(10));
    gpio_set_level(IMU_PIN_RST, 1);
    /* BNO085 boot takes ~200 ms; SH-2 advertisement follows. */
    vTaskDelay(pdMS_TO_TICKS(250));
}

/* --- SHTP I/O -------------------------------------------------------- */
static esp_err_t shtp_send(uint8_t channel, const uint8_t *cargo, size_t cargo_len)
{
    if (cargo_len > SHTP_MAX_PAYLOAD) return ESP_ERR_INVALID_SIZE;
    uint8_t  frame[SHTP_HEADER_LEN + SHTP_MAX_PAYLOAD];
    uint16_t total = (uint16_t)(SHTP_HEADER_LEN + cargo_len);
    frame[0] = total & 0xFF;
    frame[1] = (total >> 8) & 0x7F;   /* clear continuation bit */
    frame[2] = channel;
    frame[3] = s_tx_seq[channel]++;
    if (cargo_len > 0) memcpy(frame + SHTP_HEADER_LEN, cargo, cargo_len);
    return pk_i2c0_bus_transmit(s_dev, frame, total, 100);
}

/* Read one SHTP frame. *out_channel and *out_cargo_len are populated;
 * cargo bytes are copied into `out_cargo`. Returns ESP_ERR_NOT_FOUND if
 * the sensor reported no data (length == 0 in the header). */
static esp_err_t shtp_recv(uint8_t *out_cargo, size_t out_cap,
                           uint8_t *out_channel, size_t *out_cargo_len)
{
    uint8_t hdr[SHTP_HEADER_LEN];
    esp_err_t err = pk_i2c0_bus_receive(s_dev, hdr, sizeof(hdr), 100);
    if (err != ESP_OK) return err;

    uint16_t length = ((uint16_t)hdr[1] & 0x7F) << 8 | hdr[0];
    if (length == 0 || length == 0xFFFF) return ESP_ERR_NOT_FOUND;
    if (length < SHTP_HEADER_LEN) return ESP_ERR_INVALID_RESPONSE;

    size_t cargo_len = (size_t)(length - SHTP_HEADER_LEN);
    if (cargo_len > out_cap) cargo_len = out_cap;

    /* Re-issue an I²C read of the full frame; BNO085 wants the whole
     * thing in one transaction, header included, so we read length
     * bytes and skip the header in-place. */
    uint8_t scratch[SHTP_MAX_PAYLOAD + SHTP_HEADER_LEN];
    if (length > sizeof(scratch)) length = sizeof(scratch);
    err = pk_i2c0_bus_receive(s_dev, scratch, length, 100);
    if (err != ESP_OK) return err;

    *out_channel = scratch[2];
    *out_cargo_len = (size_t)(length - SHTP_HEADER_LEN);
    if (*out_cargo_len > out_cap) *out_cargo_len = out_cap;
    memcpy(out_cargo, scratch + SHTP_HEADER_LEN, *out_cargo_len);
    return ESP_OK;
}

/* --- SH-2 Command Request helper ------------------------------------- *
 *
 * A Command Request is a 12-byte cargo on the control channel:
 *
 *   byte 0:  0xF2  (report ID)
 *   byte 1:  command-request sequence (incrementing, separate from SHTP)
 *   byte 2:  command code (0x03 Tare, 0x06 Save DCD, ...)
 *   byte 3-11: P0..P8 (9 command-specific parameter bytes)
 *
 * BNO085 replies with a 0xF1 Command Response on the same channel,
 * carrying the same sequence number. We don't read it — the user-visible
 * confirmation is the change in attitude reports a moment later. */
static esp_err_t sh2_send_command(uint8_t command, const uint8_t params[9])
{
    uint8_t cargo[12];
    cargo[0] = SH2_CMD_REQUEST;
    cargo[1] = s_cmd_seq++;
    cargo[2] = command;
    if (params) memcpy(&cargo[3], params, 9);
    else        memset(&cargo[3], 0, 9);
    return shtp_send(SHTP_CH_CONTROL, cargo, sizeof(cargo));
}

/* --- Set Feature: Rotation Vector at 100 Hz -------------------------- */
static esp_err_t bno_enable_rotation_vector(void)
{
    sh2_set_feature_t cmd = {
        .report_id           = SH2_CMD_SET_FEATURE,
        .feature_id          = SH2_REPORT_ROTATION_VECTOR,
        .feature_flags       = 0,
        .change_sensitivity  = 0,
        .report_interval_us  = 10000,    /* 100 Hz */
        .batch_interval_us   = 0,
        .sensor_specific     = 0,
    };
    return shtp_send(SHTP_CH_CONTROL, (const uint8_t *)&cmd, sizeof(cmd));
}

/* --- Set Feature: Linear Acceleration at 50 Hz ----------------------- *
 *
 * 50 Hz (not 100 Hz to match Rotation Vector): this feed is destined for
 * a vibration-RMS window (next step, not this change), which doesn't
 * need 100 Hz resolution — halving the rate here halves the extra SHTP
 * traffic and I²C polling load this feature adds on top of the existing
 * Rotation Vector stream. */
static esp_err_t bno_enable_linear_acceleration(void)
{
    sh2_set_feature_t cmd = {
        .report_id           = SH2_CMD_SET_FEATURE,
        .feature_id          = SH2_REPORT_LINEAR_ACCELERATION,
        .feature_flags       = 0,
        .change_sensitivity  = 0,
        .report_interval_us  = 20000,    /* 50 Hz */
        .batch_interval_us   = 0,
        .sensor_specific     = 0,
    };
    return shtp_send(SHTP_CH_CONTROL, (const uint8_t *)&cmd, sizeof(cmd));
}

/* --- Set Feature: Magnetic Field at 10 Hz ---------------------------- *
 *
 * 诊断用（R6）：BNO085 自己的三轴磁力计读数。加它的唯一目的是回答
 * "085 处的磁场到底有多大" —— 罗盘航向不对时，必须在 085 自己身上量，
 * 不能拿同板 QMC5883P 的读数外推（两者间距 12mm，源可能只影响其中一个）。
 * 1 Hz 日志里打印模长，与地球磁场（~25–65 µT）对比即知是否有强磁源。 */
static esp_err_t bno_enable_magnetic_field(void)
{
    sh2_set_feature_t cmd = {
        .report_id           = SH2_CMD_SET_FEATURE,
        .feature_id          = SH2_REPORT_MAGNETIC_FIELD,
        .feature_flags       = 0,
        .change_sensitivity  = 0,
        .report_interval_us  = 100000,   /* 10 Hz */
        .batch_interval_us   = 0,
        .sensor_specific     = 0,
    };
    return shtp_send(SHTP_CH_CONTROL, (const uint8_t *)&cmd, sizeof(cmd));
}

/* --- Hamilton quaternion product: out = a · b ----------------------- *
 *
 * Used to apply the board-profile mounting rotation to the BNO085's
 * Rotation Vector before Euler extraction — see the sandwich section
 * in imu_task.h and the derivation in pk_board.h.
 *
 * When the mounting quaternion is identity (1,0,0,0), this function
 * is invoked with W=1, X=Y=Z=0 and the compiler's constant
 * propagation collapses the body to `*out = a`, so the no-remap
 * build path pays nothing for this hook. */
static inline void quat_mul(float aw, float ax, float ay, float az,
                            float bw, float bx, float by, float bz,
                            float *ow, float *ox, float *oy, float *oz)
{
    *ow = aw * bw - ax * bx - ay * by - az * bz;
    *ox = aw * bx + ax * bw + ay * bz - az * by;
    *oy = aw * by - ax * bz + ay * bw + az * bx;
    *oz = aw * bz + ax * by - ay * bx + az * bw;
}

/* --- Board-profile mounting term ------------------------------------- *
 *
 * q_body_fix = R_aircraft→chip for the board this firmware is built
 * for. V3.9 mounts U4 at 0°, V4.3 at +90°, so this is NOT a compile-
 * time constant of imu_task — pk_board owns the derivation.
 *
 * Cached once in pk_imu_init(), which is the only entry point that
 * creates the IMU task, so every reader below runs after the store.
 * Never written again. */
static float s_body_fix[4] = { 1.0f, 0.0f, 0.0f, 0.0f };

static void load_board_mount(void)
{
    pk_board_imu_body_fix_quat(pk_board_profile(), s_body_fix);
    ESP_LOGI(TAG, "board profile %s: q_body_fix = %.7f %.7f %.7f %.7f",
             pk_board_profile_name(pk_board_profile()),
             (double)s_body_fix[0], (double)s_body_fix[1],
             (double)s_body_fix[2], (double)s_body_fix[3]);
}

/* --- Rotate a body-frame vector chip→aircraft ------------------------ *
 *
 * Linear Acceleration is a vector in the BNO's chip body frame, NOT a
 * world-referenced orientation — so unlike parse_rotation_vector()'s
 * quaternion sandwich, only the body-frame remap applies here;
 * PK_IMU_WORLD_FIX_* (ENU→NED) is irrelevant to a body-frame vector
 * and must NOT be applied.
 *
 * s_body_fix is q_body_fix = R_aircraft→chip, i.e. it rotates AIRCRAFT
 * vectors into the CHIP frame. We need the inverse direction
 * (chip→aircraft), which for a unit quaternion is the conjugate:
 * v_aircraft = q* · v_chip · q, where q* = conj(q_body_fix).
 *
 * Standard vector-rotation-by-quaternion formula: treat v as a pure
 * quaternion (0, vx, vy, vz) and compute p · v · conj(p) with
 * p = conj(q_body_fix). Cross-checked against
 * pk_board_imu_chip_vec_to_body() — firmware/test/test_pk_board_mount.c
 * asserts the matrix form for both profiles, and
 * firmware/test/test_imu_mount.c re-derives this quaternion path for
 * V3.9 from the physical axis mapping. */
static inline void quat_rotate_vec_body_fix(float vx, float vy, float vz,
                                            float *ox, float *oy, float *oz)
{
    const float pw =  s_body_fix[0];
    const float px = -s_body_fix[1];
    const float py = -s_body_fix[2];
    const float pz = -s_body_fix[3];

    float tw, tx, ty, tz;
    quat_mul(pw, px, py, pz, 0.0f, vx, vy, vz, &tw, &tx, &ty, &tz);

    float rw, rx, ry, rz;
    quat_mul(tw, tx, ty, tz, pw, -px, -py, -pz, &rw, &rx, &ry, &rz);
    (void)rw;
    *ox = rx;
    *oy = ry;
    *oz = rz;
}

/* --- Quaternion → Euler (ZYX Tait-Bryan, aerospace convention) ------ */
static void quat_to_euler(float qi, float qj, float qk, float qw,
                          float *roll_deg, float *pitch_deg, float *yaw_deg)
{
    /* All formulas below assume a right-handed coordinate frame where
     * +X is forward, +Y is right, +Z is down (aerospace NED). The
     * BNO085 in default orientation reports a quaternion in NED, so
     * this is direct. */
    float sinr_cosp = 2.0f * (qw * qi + qj * qk);
    float cosr_cosp = 1.0f - 2.0f * (qi * qi + qj * qj);
    *roll_deg = atan2f(sinr_cosp, cosr_cosp) * (180.0f / (float)M_PI);

    float sinp = 2.0f * (qw * qj - qk * qi);
    if (sinp >  1.0f) sinp =  1.0f;
    if (sinp < -1.0f) sinp = -1.0f;
    *pitch_deg = asinf(sinp) * (180.0f / (float)M_PI);

    float siny_cosp = 2.0f * (qw * qk + qi * qj);
    float cosy_cosp = 1.0f - 2.0f * (qj * qj + qk * qk);
    float y = atan2f(siny_cosp, cosy_cosp) * (180.0f / (float)M_PI);
    if (y < 0) y += 360.0f;
    *yaw_deg = y;
}

/* --- Rotation Vector report parser ---------------------------------- *
 *
 * BNO085 prefixes every channel-3 frame with a 5-byte "Sensor Hub
 * Timestamp Reference" (report ID 0xFB) header, then the actual report
 * follows. For Rotation Vector (0x05) the layout is:
 *
 *   Byte 0:  reportID = 0x05
 *   Byte 1:  sequence
 *   Byte 2:  status (bits 0-1 = accuracy)
 *   Byte 3:  delay
 *   Byte 4-5:  i quaternion (Q14 LE)
 *   Byte 6-7:  j quaternion (Q14 LE)
 *   Byte 8-9:  k quaternion (Q14 LE)
 *   Byte 10-11: real quaternion (Q14 LE)
 *   Byte 12-13: accuracy estimate (Q12 LE radians) — optional
 *
 * If the report we get doesn't have the timestamp ref preamble (some
 * SH-2 firmwares omit it for stream reports), we'll find the report ID
 * at offset 0; otherwise it's at offset 5. We tolerate both.
 */
static bool parse_rotation_vector(const uint8_t *cargo, size_t cargo_len)
{
    const uint8_t *p = cargo;
    size_t remaining = cargo_len;

    /* Strip the 5-byte timestamp ref if present (reportID 0xFB). */
    if (remaining >= 5 && p[0] == 0xFB) {
        p += 5;
        remaining -= 5;
    }
    if (remaining < 12) return false;
    if (p[0] != SH2_REPORT_ROTATION_VECTOR) return false;

    int16_t qi_raw = (int16_t)((uint16_t)p[5] << 8 | p[4]);
    int16_t qj_raw = (int16_t)((uint16_t)p[7] << 8 | p[6]);
    int16_t qk_raw = (int16_t)((uint16_t)p[9] << 8 | p[8]);
    int16_t qw_raw = (int16_t)((uint16_t)p[11] << 8 | p[10]);
    uint8_t status = p[2];

    const float Q14 = 1.0f / (float)(1 << 14);
    float qi = (float)qi_raw * Q14;
    float qj = (float)qj_raw * Q14;
    float qk = (float)qk_raw * Q14;
    float qw = (float)qw_raw * Q14;

    /* TEMPORARY: stash raw quaternion for the 1 Hz diagnostic log. */
    s_last_raw_qw = qw;
    s_last_raw_qi = qi;
    s_last_raw_qj = qj;
    s_last_raw_qk = qk;

    /* Sandwich transform: q_aircraft = q_world_fix · q_bno · q_body_fix.
     * Left mul re-expresses the world reference from BNO's ENU to the
     * aerospace NED that quat_to_euler() expects; right mul re-expresses
     * the body frame from chip axes to aircraft axes (the mounting
     * remap). See imu_task.h for the geometric derivation. */
    float tw, ti, tj, tk;
    quat_mul(PK_IMU_WORLD_FIX_W, PK_IMU_WORLD_FIX_X,
             PK_IMU_WORLD_FIX_Y, PK_IMU_WORLD_FIX_Z,
             qw, qi, qj, qk,
             &tw, &ti, &tj, &tk);
    float aqw, aqi, aqj, aqk;
    quat_mul(tw, ti, tj, tk,
             s_body_fix[0], s_body_fix[1], s_body_fix[2], s_body_fix[3],
             &aqw, &aqi, &aqj, &aqk);

    /* Snapshot the post-sandwich attitude under the lock so
     * pk_imu_tare_now() can read a torn-free copy when the user
     * triggers a tare; then apply the software tare offset by
     * LEFT-multiplying s_tare_* onto the current aircraft attitude.
     *
     * Left-mul (not right-mul) matters: with s_tare_* = conjugate of
     * the tare-time aircraft attitude, s_tare · q_now decomposes the
     * differential rotation in the TARE-TIME aircraft body frame, so
     * Euler extraction yields roll-around-body-X, pitch-around-body-Y,
     * yaw-around-body-Z — the aerospace convention. (We consume only
     * roll/pitch from this tared quaternion; yaw is taken from the raw
     * attitude below so the compass survives a tare.) Right-mul instead
     * expresses the differential in world NED, which produces correct
     * results only when the tare-time aircraft pose happens to be
     * level/facing-N (q_at_tare ≈ identity); for any tilted mounting
     * the world-frame decomposition tangles roll/pitch/yaw, especially
     * near pitch = ±90° gimbal lock. */
    float dqw, dqi, dqj, dqk;
    xSemaphoreTake(s_sample_lock, portMAX_DELAY);
    s_last_aircraft_qw = aqw;
    s_last_aircraft_qi = aqi;
    s_last_aircraft_qj = aqj;
    s_last_aircraft_qk = aqk;
    float tare_w = s_tare_qw, tare_x = s_tare_qi,
          tare_y = s_tare_qj, tare_z = s_tare_qk;
    xSemaphoreGive(s_sample_lock);
    quat_mul(tare_w, tare_x, tare_y, tare_z,
             aqw, aqi, aqj, aqk,
             &dqw, &dqi, &dqj, &dqk);

    /* roll/pitch come from the TARED quaternion — the software tare cages
     * the artificial horizon to the tare-time reference. yaw (heading),
     * however, is sourced from the RAW post-sandwich aircraft attitude,
     * NOT the tared one: a TARE press must cage the horizon WITHOUT
     * touching the compass. If yaw came from the tared quaternion it
     * would collapse to 0 at the tare pose (conj(q)·q = identity) and the
     * HSI/HDG would thereafter show only heading *relative* to the tare
     * reference instead of the true magnetic heading. Decoupling yaw also
     * makes the compass immune to any NVS-persisted tare offset restored
     * at boot. The tared-quaternion yaw is intentionally discarded. */
    float roll, pitch, yaw;
    float discard_yaw, discard_roll, discard_pitch;
    quat_to_euler(dqi, dqj, dqk, dqw, &roll, &pitch, &discard_yaw);
    quat_to_euler(aqi, aqj, aqk, aqw, &discard_roll, &discard_pitch, &yaw);
    (void)discard_yaw; (void)discard_roll; (void)discard_pitch;

    /* 罗盘航向固定修正（见 IMU_YAW_OFFSET_DEG）。只加在航向，不碰 roll/pitch。 */
    yaw = fmodf(yaw + IMU_YAW_OFFSET_DEG, 360.0f);
    if (yaw < 0.0f) yaw += 360.0f;

    /* 这里曾经有一组 invert roll / invert pitch / invert yaw /
     * yaw offset 的手工修正旋钮（旧 breakout 时代的遗留）。2026-09-03 删除：
     * 它们在 profile 变换**之后**再改欧拉角，构成第二套全局安装修正入口，
     * 而且欧拉角后处理并不等价于三维安装旋转——"把 pitch 取反"不对应任何
     * 真实的安装姿态，用它凑出来的 PFD 在复合姿态下必然是错的，还会和走
     * pk_board 的磁力计各说各话。安装方向的唯一来源是 pk_board 的 profile；
     * 真机上如果哪个轴不对，改的是 pk_board.c 里对应那一段判据。
     * hardware/test_firmware_board_profile_contract.py 会阻止它们复活。 */

    xSemaphoreTake(s_sample_lock, portMAX_DELAY);
    s_sample.ts_us     = esp_timer_get_time();
    s_sample.roll_deg  = roll;
    s_sample.pitch_deg = pitch;
    s_sample.yaw_deg   = yaw;
    s_sample.accuracy  = status & 0x03;
    s_sample.valid     = true;
    xSemaphoreGive(s_sample_lock);
    /* 第一条真实姿态到手 = tare / factory reset 的门禁打开（见 s_imu_ready）。 */
    s_imu_ready = true;
    return true;
}

/* --- Linear Acceleration report parser -------------------------------- *
 *
 * Same 5-byte timestamp-ref preamble handling as parse_rotation_vector()
 * (see its comment). For Linear Acceleration (0x04) the SH-2 3-axis
 * report layout (SH-2 Reference Manual §6.5.9) is:
 *
 *   Byte 0:  reportID = 0x04
 *   Byte 1:  sequence
 *   Byte 2:  status (bits 0-1 = accuracy)
 *   Byte 3:  delay
 *   Byte 4-5:  x (Q8 LE)
 *   Byte 6-7:  y (Q8 LE)
 *   Byte 8-9:  z (Q8 LE)
 *
 * Q8 fixed point (1 LSB = 1/256 m/s²) — NOT Q14 like Rotation Vector;
 * different SH-2 reports use different Q points per §5.1. Gravity is
 * already subtracted by the SH-2 fusion engine, so this is genuine
 * linear (dynamic) acceleration, chip body frame. */
static bool parse_linear_acceleration(const uint8_t *cargo, size_t cargo_len)
{
    const uint8_t *p = cargo;
    size_t remaining = cargo_len;

    if (remaining >= 5 && p[0] == 0xFB) {
        p += 5;
        remaining -= 5;
    }
    if (remaining < 10) return false;
    if (p[0] != SH2_REPORT_LINEAR_ACCELERATION) return false;

    int16_t ax_raw = (int16_t)((uint16_t)p[5] << 8 | p[4]);
    int16_t ay_raw = (int16_t)((uint16_t)p[7] << 8 | p[6]);
    int16_t az_raw = (int16_t)((uint16_t)p[9] << 8 | p[8]);

    const float Q8 = 1.0f / (float)(1 << 8);
    float ax = (float)ax_raw * Q8;
    float ay = (float)ay_raw * Q8;
    float az = (float)az_raw * Q8;

    /* Chip→aircraft body-frame rotation — see quat_rotate_vec_body_fix()
     * for why this uses only the mount (body) quaternion, not the
     * world fix used by parse_rotation_vector(). */
    float bx, by, bz;
    quat_rotate_vec_body_fix(ax, ay, az, &bx, &by, &bz);

    /* Feed the vibration-RMS window before taking s_sample_lock — pk_vib
     * is its own module, doesn't touch s_sample, no reason to hold the
     * mutex across it. */
    pk_vib_push(&s_vib, bx, by, bz);
    uint8_t vib = pk_vib_level(&s_vib);

    xSemaphoreTake(s_sample_lock, portMAX_DELAY);
    s_sample.accel_x_mps2 = bx;
    s_sample.accel_y_mps2 = by;
    s_sample.accel_z_mps2 = bz;
    s_sample.have_accel   = true;
    s_sample.vib_level    = vib;
    xSemaphoreGive(s_sample_lock);
    return true;
}

/* --- Magnetic Field report parser (diagnostic, R6) ------------------- *
 *
 * SH-2 磁力计报文 0x03，布局同其它 3 轴报文（SH-2 §6.5.8）：
 *   byte 0 reportID=0x03 / 1 seq / 2 status / 3 delay / 4-9 x,y,z (Q16 LE)
 * Q16：1 LSB = 1/16 µT。仅存最近值供 1 Hz 日志，不参与姿态解算。 */
static volatile float s_last_mag_ut[3];
static volatile float s_last_mag_norm_ut;

static bool parse_magnetic_field(const uint8_t *cargo, size_t cargo_len)
{
    const uint8_t *p = cargo;
    size_t remaining = cargo_len;
    if (remaining >= 5 && p[0] == 0xFB) { p += 5; remaining -= 5; }
    if (remaining < 10) return false;
    if (p[0] != SH2_REPORT_MAGNETIC_FIELD) return false;

    int16_t mx_raw = (int16_t)((uint16_t)p[5] << 8 | p[4]);
    int16_t my_raw = (int16_t)((uint16_t)p[7] << 8 | p[6]);
    int16_t mz_raw = (int16_t)((uint16_t)p[9] << 8 | p[8]);
    const float Q16 = 1.0f / 16.0f;
    float mx = (float)mx_raw * Q16;
    float my = (float)my_raw * Q16;
    float mz = (float)mz_raw * Q16;
    s_last_mag_ut[0] = mx;
    s_last_mag_ut[1] = my;
    s_last_mag_ut[2] = mz;
    s_last_mag_norm_ut = sqrtf(mx * mx + my * my + mz * mz);
    return true;
}

/* --- Bring-up sequence (used both at boot and by the watchdog) ------- *
 *
 * Pulses RST, drains the boot-time SHTP advertisement, and re-enables
 * the Rotation Vector and Linear Acceleration reports. Safe to call
 * from any task. Resets the SHTP per-channel sequence counters too —
 * BNO085 starts back at seq=0 after a reset and would reject our
 * frames if our side kept counting. */
/* 本次开机是否已经存过 DCD。定义提前到 bno_bring_up 之前：硬复位会丢掉
 * 芯片 RAM 里的校准，复位后必须允许重新落盘，否则形成"复位→掉精度→
 * 重校准→不落盘"的死循环（2026-09-10）。volatile：置位/清零跨任务，
 * 单字节读写原子，最坏多存/少存一次，不值得引锁。 */
static volatile bool s_dcd_saved;

static esp_err_t bno_bring_up(void)
{
    bno_reset_pulse();
    s_dcd_saved = false;   /* 芯片 RAM 校准已被复位丢弃，允许重新落盘 */

    /* SHTP and command-request sequence numbers restart at 0 on the
     * BNO085 side after a hard reset. Mirror that on our side. */
    memset(s_tx_seq, 0, sizeof(s_tx_seq));
    s_cmd_seq = 0;

    /* Drain whatever SH-2 sent us during boot (advertisement + Reset
     * Complete + a couple of internal acks). 500 ms is plenty even on
     * slow firmware revisions. */
    uint8_t  scratch[SHTP_MAX_PAYLOAD];
    uint8_t  ch;
    size_t   clen;
    int64_t  deadline = esp_timer_get_time() + 500000;
    while (esp_timer_get_time() < deadline) {
        if (shtp_recv(scratch, sizeof(scratch), &ch, &clen) != ESP_OK) {
            vTaskDelay(pdMS_TO_TICKS(20));
        }
    }

    esp_err_t err = bno_enable_rotation_vector();
    if (err != ESP_OK) return err;
    err = bno_enable_linear_acceleration();
    if (err != ESP_OK) return err;
    return bno_enable_magnetic_field();
}

/* --- DCD 落盘（磁场动态校准数据 → BNO085 内部 flash） ----------------- *
 *
 * 为什么必须显式存：融合引擎运行时一直在更新 DCD（磁力计硬铁偏置等），
 * 但**只在收到 Save DCD 命令时**才写进芯片自己的 flash。此前固件从来没发
 * 过这条命令（0x06 只有宏定义、没有调用点），于是每次上电磁场融合都从零
 * 开始。2026-08-03 真机日志：盒子静止放桌上 48 秒 acc 全程 0，校准页照样
 * 在 t=31.7s 弹出——磁力计静止时物理上就无法自校准，不给它一份开机就能
 * 恢复的校准，用户永远在等一个等不来的收敛。
 *
 * 注意跟 pk_imu_tare_persist() 不是一回事：那个存的是软件 tare 四元数、
 * 落在 ESP32 的 NVS，明确不碰 DCD（见 imu_task.h 的说明）。这里存的是芯片
 * 自己的校准数据、落在芯片自己的 flash。 */

/* acc 连续这么多秒 >= 2（中档及以上）才落盘。
 *
 * 2026-09-10 由 `== 3` 放宽到 `>= 2`：原判据要求顶档，但真实环境（机坪/
 * 机库/含铁结构附近）磁场融合常常只到中档，于是**永远不落盘**——每次开机
 * 都从 0 收敛，校准页反复弹。存一份中档校准、开机即恢复，远好于反复从零
 * 收敛；DCD 本就是可继续演进的运行时数据，不是一次性终值。
 *
 * 5 秒这个时长取自真机日志（acc 逐档爬升、每档约 2 秒），连续 5 秒 >= 2
 * 说明已越过爬升过程稳定下来，而不是路过。 */
#define IMU_DCD_SAVE_DWELL_S     5

/* s_dcd_saved 的语义与并发说明见文件上方（定义已提前到 bno_bring_up 之前，
 * 因为硬复位路径要清零它）。BNO08x 的 FRS flash 有写入寿命，判据是"每次
 * 开机最多一次"，而不是"只要 acc>=2 就周期性存"。 */

static esp_err_t bno_save_dcd(void)
{
    /* SH-2 Command 0x06 "Save DCD Now" 不带参数，9 个参数字节全 0——
     * 写法与 bno_clear_persisted_dcd() 一致。 */
    uint8_t p[9] = {0};
    return sh2_send_command(SH2_COMMAND_SAVE_DCD, p);
}

/* --- Save DCD 的 Command Response 观察点 ------------------------------ *
 *
 * sh2_send_command() 的返回值只能证明那 12 个字节被 I²C 发出去了，证明不了
 * 芯片真的把 DCD 写进了 flash；而 flash 里有什么在盒子上没有任何可见现象。
 * 所以多看一眼芯片的回执。Command Response 走控制通道，布局见 SH-2
 * Reference Manual §6.4：
 *
 *   byte 0:  0xF1（report ID）
 *   byte 1:  SHTP 序号
 *   byte 2:  command —— 回显我们发的命令码；用它过滤掉芯片复位后自己发的
 *            那些响应（Initialize 等），否则每次 bring-up 都要刷一片日志
 *   byte 3:  command sequence（回显 sh2_send_command 里的 s_cmd_seq）
 *   byte 4:  response sequence
 *   byte 5+: R0..R10；对 0x06 而言 R0 = status，0 = 成功
 *
 * 只打日志，不参与任何判据：万一 R0 的语义与手册理解有出入，代价也只是一行
 * 多余的日志，落盘逻辑与节流都不受影响。 */
static void imu_note_save_dcd_response(const uint8_t *cargo, size_t len)
{
    if (len < 6) return;
    if (cargo[0] != SH2_CMD_RESPONSE)      return;
    if (cargo[2] != SH2_COMMAND_SAVE_DCD)  return;

    uint8_t r0 = cargo[5];
    if (r0 == 0) {
        ESP_LOGI(TAG, "BNO: Save DCD 回执 R0=%u（0 = 芯片已写入 flash）", r0);
    } else {
        ESP_LOGW(TAG, "BNO: Save DCD 回执 R0=%u（非 0 = 芯片拒绝写入）", r0);
    }
}

/* --- IMU polling task ------------------------------------------------ *
 *
 * Polls SHTP at 200 Hz, parses Rotation Vector reports, logs a 1 Hz
 * summary with classified recv counters, and runs a watchdog that
 * re-inits the BNO085 if no valid report has arrived in IMU_STALL_TIMEOUT_US.
 *
 * Why a watchdog is needed: the BNO085 occasionally hangs mid-stream
 * (chip firmware bug or I²C bus glitch). Once that happens the chip
 * stops emitting reports entirely and there's no spontaneous recovery
 * without a hard reset on the RST line. We catch it by tracking the
 * last successful parse and pulsing RST + replaying init when the gap
 * crosses a threshold. */

#define IMU_STALL_TIMEOUT_US      (5 * 1000000LL)   /* 5 s with no valid RV report → re-init */
#define IMU_REINIT_MIN_GAP_US     (3 * 1000000LL)   /* don't retry sooner than this after a re-init attempt */

/* --- 开机 bring-up 的退避重试 ---------------------------------------- *
 *
 * 过去 bno_bring_up() 跑在 pk_imu_init() 里、**在任务被创建之前**，失败就
 * return：整次开机没有 imu 任务，于是下面那条 5 s stall watchdog、总线
 * generation 重放、RST 自愈全都没有执行者，只能重启整机。而开机那一瞬恰恰
 * 最不可靠（2026-08-03 真机日志里的总线塌陷就在开机阶段）。现在任务先存在，
 * 握手是它循环里的第一步，失败就退避重试到成功为止。 */

/* 退避涨到这一档才把失败升级成**总线级**恢复请求。判据与节流的论证同
 * baro_task.c 的 BARO_UP_RECOVER_MIN_BACKOFF_MS：总线复位会打扰同一条总线
 * 上的 baro / touch / codec，开机头几秒的失败多半是别人还没让开，那种瞬态
 * 自己会好。 */
#define IMU_UP_RECOVER_MIN_BACKOFF_MS  8000

typedef struct {
    bool    ever_recovered;   /* 请求过总线恢复没有（区分"从没请求过"与 t=0） */
    int64_t last_recover_us;
} imu_up_ctx_t;

static bool imu_bring_up_attempt(void *ctx)
{
    (void)ctx;
    esp_err_t err = bno_bring_up();
    if (err != ESP_OK) {
        ESP_LOGW(TAG, "BNO085 bring-up 失败: %s", esp_err_to_name(err));
        return false;
    }
    ESP_LOGI(TAG, "BNO085 rotation vector @ 100 Hz + linear accel @ 50 Hz enabled");
    return true;
}

static void imu_on_failed_bring_up(void *ctx, uint32_t attempt_no, uint32_t backoff_ms)
{
    imu_up_ctx_t *up = (imu_up_ctx_t *)ctx;

    /* 没握上手就别对外冒充有姿态：PFD 宁可画"无姿态"，也不能拿默认的单位
     * 四元数当成一个水平的地平线（那在飞行中是致命的谎）。 */
    xSemaphoreTake(s_sample_lock, portMAX_DELAY);
    s_sample.valid      = false;
    s_sample.have_accel = false;
    xSemaphoreGive(s_sample_lock);

    ESP_LOGW(TAG, "BNO085 bring-up 第 %u 次失败 — %u ms 后重试",
             (unsigned)attempt_no, (unsigned)backoff_ms);

    if (backoff_ms < IMU_UP_RECOVER_MIN_BACKOFF_MS) return;

    const int64_t now = esp_timer_get_time();
    if (up->ever_recovered &&
        now - up->last_recover_us < (int64_t)IMU_UP_RECOVER_MIN_BACKOFF_MS * 1000) {
        return;
    }
    up->ever_recovered  = true;
    up->last_recover_us = now;
    /* 拉了 RST 还是一个字节都发不出去 —— 这是**总线**级故障的直接证据，
     * 不是 BNO085 挂了（芯片挂了会 NACK，不会让主控发不出去）。和 stall
     * watchdog 里那条 "bring-up after stall failed" 是同一个判据。 */
    (void)pk_i2c0_recover_request("imu/bring-up");
}

static void imu_task(void *arg)
{
    (void)arg;
    ESP_LOGI(TAG, "imu_task running (polling @ 200 Hz, stall watchdog @ 5 s)");

    uint8_t cargo[SHTP_MAX_PAYLOAD];
    int64_t last_log_us    = 0;
    int64_t last_valid_us  = 0;
    int64_t last_reinit_us = 0;

    /* 总线级故障的上报口。门槛 2 次、不看时长：这里的"一次失败"已经是
     * 「stall watchdog 等了 5 秒 + 拉 RST 重放了一遍 SH-2 init 仍然没流」，
     * 上游天然带了 5 秒去抖，再等两轮（约 8 秒一轮）就够保守了。
     * bring-up 自己都失败的那条路径不走这个门槛，见下面的调用点。 */
    pk_i2c0_client_t i2c_client;
    pk_i2c0_client_init(&i2c_client, "imu", 2, 0);

    /* 总线恢复代数（住在板级总线模块里）。别的任务（baro）把总线救回来
     * 之后，这里要跟着把 BNO085 重新初始化一遍——总线复位只是把线放开了，
     * 芯片那侧的 SH-2 会话已经断了，不重放 init 就永远收不到报文。 */
    uint32_t bus_gen = pk_i2c0_bus_generation();

    /* Per-second counters (zeroed in the 1 Hz dump). */
    uint32_t valid_count        = 0;   /* successfully parsed RV reports */
    uint32_t parse_fail         = 0;   /* SHTP frame on CH3 but not an RV report */
    uint32_t recv_not_found     = 0;   /* shtp_recv returned ESP_ERR_NOT_FOUND (no data this tick) */
    uint32_t recv_i2c_err       = 0;   /* shtp_recv returned a real I²C bus error */
    uint32_t recv_wrong_channel = 0;   /* SHTP frame received but channel != 3 (CH 0/1/2/4 etc.) */

    /* acc 已经连续读到 3 多少秒（在 1 Hz 那一段累加，掉档即清零）。
     * 攒够 IMU_DCD_SAVE_DWELL_S 就落盘一次，见下面的调用点。 */
    uint32_t dcd_dwell_s = 0;

    /* --- 开机 bring-up：退避重试到芯片回话为止，永不放弃、永不删任务 --- */
    imu_up_ctx_t up_ctx = { .ever_recovered = false, .last_recover_us = 0 };
    const pk_bringup_retry_t up_cfg = {
        .name              = "bno085",
        .attempt           = imu_bring_up_attempt,
        .on_failed_attempt = imu_on_failed_bring_up,
        .ctx               = &up_ctx,
    };
    pk_bringup_retry_run(&up_cfg);

    /* 重试期间总线可能被谁复位过（也可能是我们自己请求的）。握上手用的就是
     * 复位之后的总线，所以把代数对齐，免得下面第一轮就判"代数变了"再白重放
     * 一次 bring-up。失败计数同理清零。 */
    bus_gen = pk_i2c0_bus_generation();
    pk_i2c0_client_reset(&i2c_client);

    /* stall 时钟从**握手成功**那一刻起算：从任务创建起算的话，一次几十秒的
     * bring-up 重试之后一进循环就会立刻判 stall，白拉一次 RST。 */
    last_valid_us = esp_timer_get_time();

    while (1) {
        /* --- 总线被别人救回来了？先把自己重新初始化，再谈轮询 --- */
        {
            const uint32_t gen = pk_i2c0_bus_generation();
            if (gen != bus_gen) {
                bus_gen = gen;
                ESP_LOGW(TAG, "I²C0 总线已复位（第 %lu 轮）— 重放 BNO085 初始化",
                         (unsigned long)gen);
                xSemaphoreTake(s_sample_lock, portMAX_DELAY);
                s_sample.valid = false;
                s_sample.have_accel = false;
                xSemaphoreGive(s_sample_lock);

                esp_err_t bu = bno_bring_up();
                last_reinit_us = esp_timer_get_time();
                last_valid_us  = last_reinit_us;   /* 给芯片时间重新出流 */
                pk_i2c0_client_reset(&i2c_client);
                if (bu != ESP_OK) {
                    ESP_LOGW(TAG, "总线恢复后 bring-up 仍失败: %s",
                             esp_err_to_name(bu));
                } else {
                    ESP_LOGI(TAG, "总线恢复后 BNO085 重新初始化完成");
                }
            }
        }

        uint8_t channel;
        size_t  cargo_len = 0;
        esp_err_t err = shtp_recv(cargo, sizeof(cargo), &channel, &cargo_len);
        if (err == ESP_OK) {
            if (channel == SHTP_CH_SENSORHUB) {
                /* Channel 3 carries both report types we've enabled;
                 * each parser checks the report ID and returns false
                 * (no side effects) if it's not the one it handles. */
                if (parse_rotation_vector(cargo, cargo_len)) {
                    valid_count++;
                    last_valid_us = esp_timer_get_time();
                } else if (parse_linear_acceleration(cargo, cargo_len)) {
                    /* Only feeds have_accel/accel_*; doesn't count toward
                     * the attitude-stream watchdog's last_valid_us. */
                } else if (parse_magnetic_field(cargo, cargo_len)) {
                    /* Diagnostic only (R6): stores the latest field for the
                     * 1 Hz log. Doesn't count toward the RV watchdog either. */
                } else {
                    parse_fail++;
                }
            } else {
                recv_wrong_channel++;
                /* 控制通道上唯一还关心的东西：Save DCD 的回执。其余照旧
                 * 只计数、DEBUG 一行然后丢掉。 */
                if (channel == SHTP_CH_CONTROL) {
                    imu_note_save_dcd_response(cargo, cargo_len);
                }
                ESP_LOGD(TAG, "shtp ch=%u cargo=%u (ignored)",
                         channel, (unsigned)cargo_len);
            }
        } else if (err == ESP_ERR_NOT_FOUND) {
            recv_not_found++;
        } else {
            recv_i2c_err++;
        }

        int64_t now = esp_timer_get_time();

        /* --- Watchdog: re-init if no valid RV report in N seconds --- */
        if (now - last_valid_us > IMU_STALL_TIMEOUT_US &&
            now - last_reinit_us > IMU_REINIT_MIN_GAP_US) {
            ESP_LOGW(TAG, "no valid RV report for %.1fs — re-init BNO085",
                     (double)(now - last_valid_us) / 1e6);

            /* Mark sample invalid so PFD knows we lost the stream. */
            xSemaphoreTake(s_sample_lock, portMAX_DELAY);
            s_sample.valid = false;
            s_sample.have_accel = false;
            xSemaphoreGive(s_sample_lock);

            esp_err_t bu = bno_bring_up();
            last_reinit_us = esp_timer_get_time();
            /* Reset the stall clock so we give the chip time to start
             * producing reports again before retrying. */
            last_valid_us = last_reinit_us;
            if (bu != ESP_OK) {
                ESP_LOGW(TAG, "bring-up after stall failed: %s",
                         esp_err_to_name(bu));
                /* 升级路径 a：bring-up 里那几笔 i2c_master_transmit 自己就
                 * 超时了 —— 这是**总线**级故障的直接证据，不是 BNO085 挂了
                 * （芯片挂了会 NACK 或给出乱码，不会让主控发不出去）。
                 * 2026-08-03 真机日志的最后一行就是这条：
                 *     W (19440) imu: bring-up after stall failed: ESP_ERR_TIMEOUT
                 * 走到这里说明再拉几次 RST 也没意义，直接请求总线级恢复。 */
                (void)pk_i2c0_recover_request("imu/bring-up-timeout");
            } else {
                ESP_LOGI(TAG, "BNO085 re-init complete; waiting for reports");
                /* 升级路径 b：命令发得出去、芯片也复位了，可流就是不回来。
                 * 单轮可能只是 BNO085 自己启动慢，所以连着两轮 stall 都这样
                 * 才升级（门槛见 i2c_client 的初始化）。总线半死不活时正是
                 * 这个形态：写能 ACK，读回来全是 0 长度帧。 */
                (void)pk_i2c0_client_report(&i2c_client, false);
            }
        }

        /* --- 1 Hz summary log --- */
        if (now - last_log_us >= 1000000) {
            /* 这一秒收到过有效报文 = 流是通的，把总线失败计数清零。放在
             * 1 Hz 这里而不是 parse 成功那一刻，是为了不给 100 Hz 的热路径
             * 加调用；判据完全等价（stall 的定义就是 5 秒没有有效报文）。 */
            if (valid_count > 0) pk_i2c0_client_reset(&i2c_client);

            pk_imu_sample_t s;
            pk_imu_sample_get(&s);
            /* vib 也一起打出来：下一步要做"盒子静止时不提示校准"，而判静止
             * 的阈值只能用真机实测值定——pk_vib.h 只保证 0=不可用、真正静止
             * 是一个小的非零值，到底是 1 还是 5 谁也没量过。有了这个观测点，
             * 烧一次就能顺带把静止/运动两种状态的基线采下来。 */
            ESP_LOGI(TAG, "rpy = %+7.2f / %+7.2f / %7.2f  "
                          "raw_q(w,i,j,k) = %+0.4f %+0.4f %+0.4f %+0.4f  "
                          "mag=(%+7.1f,%+7.1f,%+7.1f)uT |B|=%6.1f  "
                          "(acc=%u valid=%lu parse_fail=%lu "
                          "nf=%lu i2c_err=%lu wrong_ch=%lu vib=%u)",
                     s.roll_deg, s.pitch_deg, s.yaw_deg,
                     s_last_raw_qw, s_last_raw_qi, s_last_raw_qj, s_last_raw_qk,
                     (double)s_last_mag_ut[0], (double)s_last_mag_ut[1],
                     (double)s_last_mag_ut[2], (double)s_last_mag_norm_ut,
                     s.accuracy,
                     (unsigned long)valid_count,
                     (unsigned long)parse_fail,
                     (unsigned long)recv_not_found,
                     (unsigned long)recv_i2c_err,
                     (unsigned long)recv_wrong_channel,
                     s.vib_level);

            /* --- acc 稳定到顶档就把 DCD 存进芯片 flash（每次开机一次） --- *
             *
             * 落点选在这里而不是 parse_rotation_vector()：那边跑在 100 Hz 的
             * 轮询回路里、而且正持着 s_sample_lock，在锁内做一笔阻塞的
             * i2c_master_transmit 会把所有 pk_imu_sample_get() 的消费者
             * （PFD、交通页、看板…）一起卡住。这里既没持锁，1 Hz 的节奏又
             * 天然就是 dwell 计数器要的刻度；而且和收发 SHTP 的是同一个任务，
             * s_tx_seq / s_cmd_seq 这些没有互斥保护的序号不会被并发写。 */
            if (!s_dcd_saved) {
                /* 判据必须取**芯片真实状态**，不能复用上面那份 s：演示模式下
                 * pk_imu_sample_get() 整个被 demo_data 接管、accuracy 硬编码
                 * 成 3（demo_data.c 的 pk_demo_imu_sample），拿它当判据会在
                 * 根本没插 IMU 的演示机上白烧掉一次 flash 写入。 */
                uint8_t hw_acc;
                bool    hw_valid;
                xSemaphoreTake(s_sample_lock, portMAX_DELAY);
                hw_acc   = s_sample.accuracy;
                hw_valid = s_sample.valid;
                xSemaphoreGive(s_sample_lock);

                if (hw_valid && hw_acc >= 2) dcd_dwell_s++;
                else                         dcd_dwell_s = 0;

                if (dcd_dwell_s >= IMU_DCD_SAVE_DWELL_S) {
                    /* 先置位再发：发失败也不重试。失败要么是总线坏了（stall
                     * watchdog 会去修，修完芯片一复位 acc 归零、这轮校准本来
                     * 就没了），要么是芯片状态不对——两种情况下反复重发都只是
                     * 在消耗 flash 写入寿命。 */
                    s_dcd_saved = true;
                    esp_err_t derr = bno_save_dcd();
                    if (derr == ESP_OK) {
                        ESP_LOGI(TAG, "BNO: 已发出 Save DCD（acc>=2 连续 %u s）"
                                      "— 磁场校准写入芯片 flash，下次开机应直接高 acc",
                                 (unsigned)IMU_DCD_SAVE_DWELL_S);
                    } else {
                        ESP_LOGW(TAG, "BNO: Save DCD 发送失败: %s "
                                      "— 本次开机不再重试，下次开机磁场仍需重新收敛",
                                 esp_err_to_name(derr));
                    }
                }
            }

            valid_count        = 0;
            parse_fail         = 0;
            recv_not_found     = 0;
            recv_i2c_err       = 0;
            recv_wrong_channel = 0;
            last_log_us        = now;
        }
        vTaskDelay(pdMS_TO_TICKS(5));   /* 200 Hz polling */
    }
}

/* --- Public init ----------------------------------------------------- */
bool pk_imu_sample_get(pk_imu_sample_t *out)
{
    if (out == NULL) return false;
    /* 演示模式在**数据源**这一层接管，而不是在每个页面里加分支：姿态的消费者
     * 有 PFD、交通页、看板、诊断页、调平向导五处，逐处加 if 迟早漏一处，而漏
     * 掉的那一处就是"半真半假"的画面。接管点选在锁之外、最前面，硬件没接时
     * s_sample_lock 还是 NULL，照样能出数据。 */
    if (pk_demo_enabled()) return pk_demo_imu_sample(esp_timer_get_time(), out);
    if (s_sample_lock == NULL) return false;
    xSemaphoreTake(s_sample_lock, portMAX_DELAY);
    *out = s_sample;
    bool valid = s_sample.valid;
    xSemaphoreGive(s_sample_lock);
    return valid;
}

esp_err_t pk_imu_init(void)
{
    /* 先装安装变换：s_body_fix 必须在 IMU 任务被创建之前就位，否则第一批
     * Rotation Vector 会按单位四元数解算，PFD 会闪一下错误姿态。 */
    load_board_mount();

    s_sample_lock = xSemaphoreCreateMutex();
    if (s_sample_lock == NULL) return ESP_ERR_NO_MEM;
    pk_vib_reset(&s_vib);

    /* NVS bring-up. Idempotent: returns ESP_ERR_INVALID_STATE if some
     * other subsystem (BLE / esp_hosted) already initialised it, which
     * is fine — we just want to make sure it's up before opening our
     * namespace below. ESP_ERR_NVS_NO_FREE_PAGES / NEW_VERSION_FOUND
     * is the standard "first boot or partition layout changed" path:
     * erase and try again. */
    esp_err_t nvs_err = nvs_flash_init();
    if (nvs_err == ESP_ERR_NVS_NO_FREE_PAGES ||
        nvs_err == ESP_ERR_NVS_NEW_VERSION_FOUND) {
        ESP_LOGW(TAG, "NVS partition needs erase (%s) — wiping and retrying",
                 esp_err_to_name(nvs_err));
        ESP_ERROR_CHECK(nvs_flash_erase());
        nvs_err = nvs_flash_init();
    }
    if (nvs_err != ESP_OK && nvs_err != ESP_ERR_INVALID_STATE) {
        ESP_LOGW(TAG, "nvs_flash_init: %s — tare persistence disabled",
                 esp_err_to_name(nvs_err));
        /* Non-fatal: software tare in RAM still works, just no
         * cross-reboot persistence. */
    } else {
        /* Try to restore a previously-persisted software tare. Missing
         * key on a fresh install is the normal path, not an error. */
        float w, x, y, z;
        esp_err_t load_err = imu_nvs_load_tare(&w, &x, &y, &z);
        if (load_err == ESP_OK) {
            s_tare_qw = w; s_tare_qi = x; s_tare_qj = y; s_tare_qk = z;
            ESP_LOGI(TAG, "loaded persisted software tare from NVS: "
                          "(w,i,j,k) = %+0.4f %+0.4f %+0.4f %+0.4f",
                     w, x, y, z);
        } else if (load_err == ESP_ERR_NVS_NOT_FOUND) {
            ESP_LOGI(TAG, "no persisted software tare in NVS — "
                          "starting with identity (TARE long-press to save)");
        } else {
            ESP_LOGW(TAG, "load persisted software tare failed (%s) — "
                          "starting with identity",
                     esp_err_to_name(load_err));
        }
    }

    esp_err_t err = i2c_add_device();
    if (err != ESP_OK) {
        ESP_LOGE(TAG, "i2c_add_device: %s", esp_err_to_name(err));
        vSemaphoreDelete(s_sample_lock);
        s_sample_lock = NULL;
        return err;
    }

    /* 这里**不**跑 bno_bring_up()：握手是 imu_task 循环里的第一步，失败就在
     * 任务里退避重试（见 imu_bring_up_attempt）。过去在这里同步握手、失败即
     * return，任务从来没被创建，整次开机再没有姿态——那正是要修的病。
     * 于是本函数只做"装配"：装不上（内存/总线）才返回错误。 */
    BaseType_t ok = xTaskCreatePinnedToCore(
        imu_task, "imu", 4096, NULL, 5, NULL, 0);
    if (ok != pdTRUE) {
        /* 建不起任务就没人去摘器件、没人去还锁：这里必须自己收干净，否则
         * 上层若重试一次 init，i2c device 会被挂第二遍、mutex 漏第二把。 */
        ESP_LOGE(TAG, "imu task create failed");
        i2c_master_bus_rm_device(s_dev);
        s_dev = NULL;
        vSemaphoreDelete(s_sample_lock);
        s_sample_lock = NULL;
        return ESP_ERR_NO_MEM;
    }
    return ESP_OK;
}

/* --- Tare API (software-side) --------------------------------------- *
 *
 * The user-facing tare functions don't talk to the BNO at all (with
 * one exception: factory_reset, which has to clean up legacy persisted
 * state inside BNO flash). Instead, "tare" means "set s_tare_* to the
 * conjugate of the current post-sandwich attitude" so that next frame
 * the displayed quaternion is identity.
 *
 * Why not the BNO's own SH-2 Tare command: the world-frame fix
 * (ENU→NED) and the body-frame remap (chip→aircraft) are applied as
 * a sandwich around the BNO output in parse_rotation_vector(). When
 * BNO Tare zeroes its internal output to identity, the sandwich math
 * turns that identity into q_world_fix · q_body_fix ≠ identity — the
 * decoded Euler angles hit gimbal lock at pitch = -90°. A pure-software
 * tare sidesteps that entirely. */

/* Conjugate of a unit quaternion = (w, -x, -y, -z) — represents the
 * inverse rotation. */
static inline void quat_conj(float w, float x, float y, float z,
                             float *ow, float *ox, float *oy, float *oz)
{
    *ow =  w;
    *ox = -x;
    *oy = -y;
    *oz = -z;
}

/* --- NVS load/save for the persisted software tare ------------------ */
static esp_err_t imu_nvs_load_tare(float *w, float *x, float *y, float *z)
{
    nvs_handle_t h;
    esp_err_t err = nvs_open(IMU_NVS_NAMESPACE, NVS_READONLY, &h);
    if (err != ESP_OK) return err;

    float buf[4];
    size_t len = sizeof(buf);
    err = nvs_get_blob(h, IMU_NVS_KEY_TARE, buf, &len);
    nvs_close(h);
    if (err != ESP_OK) return err;
    if (len != sizeof(buf)) return ESP_ERR_INVALID_SIZE;

    *w = buf[0]; *x = buf[1]; *y = buf[2]; *z = buf[3];
    return ESP_OK;
}

static esp_err_t imu_nvs_save_tare(float w, float x, float y, float z)
{
    nvs_handle_t h;
    esp_err_t err = nvs_open(IMU_NVS_NAMESPACE, NVS_READWRITE, &h);
    if (err != ESP_OK) return err;

    const float buf[4] = { w, x, y, z };
    err = nvs_set_blob(h, IMU_NVS_KEY_TARE, buf, sizeof(buf));
    if (err == ESP_OK) err = nvs_commit(h);
    nvs_close(h);
    return err;
}

static esp_err_t imu_nvs_erase_tare(void)
{
    nvs_handle_t h;
    esp_err_t err = nvs_open(IMU_NVS_NAMESPACE, NVS_READWRITE, &h);
    if (err != ESP_OK) return err;

    err = nvs_erase_key(h, IMU_NVS_KEY_TARE);
    if (err == ESP_ERR_NVS_NOT_FOUND) err = ESP_OK; /* already absent — fine */
    if (err == ESP_OK) err = nvs_commit(h);
    nvs_close(h);
    return err;
}

/* --- Legacy BNO state cleanup (factory reset only) ------------------- *
 *
 * Old firmware revisions wrote a persistent Tare and Save-DCD into BNO
 * internal flash via SH-2 commands. Those writes can survive a
 * software upgrade, so on factory_reset we still need to wipe them or
 * they leak into the new software-tare regime. Neither of these is
 * exposed in the public API anymore — they're internal helpers for
 * pk_imu_factory_reset() only. */

static esp_err_t bno_clear_persisted_tare(void)
{
    ESP_LOGI(TAG, "BNO: clearing persisted reorientation (identity quat + persist)");

    /* Tare Set Reorientation (subcommand 2) with identity quaternion
     * (qi=qj=qk=0, qw=1.0). The four components are signed 16-bit
     * Q14, little-endian, packed into P1..P8:
     *   P1/P2 = qi (LSB/MSB)   → 0x00 0x00
     *   P3/P4 = qj             → 0x00 0x00
     *   P5/P6 = qk             → 0x00 0x00
     *   P7/P8 = qw             → 0x00 0x40   (16384 in Q14 = 1.0) */
    uint8_t p[9] = {0};
    p[0] = 0x02;       /* Tare Set Reorientation */
    p[7] = 0x00;       /* qw LSB */
    p[8] = 0x40;       /* qw MSB → 0x4000 = 16384 = 1.0 in Q14 */
    esp_err_t err = sh2_send_command(SH2_COMMAND_TARE, p);
    if (err != ESP_OK) return err;
    vTaskDelay(pdMS_TO_TICKS(50));

    memset(p, 0, sizeof(p));
    p[0] = SH2_TARE_SUB_PERSIST;
    return sh2_send_command(SH2_COMMAND_TARE, p);
}

static esp_err_t bno_clear_persisted_dcd(void)
{
    ESP_LOGI(TAG, "BNO: clearing persisted DCD (mag/gyro/accel zero offsets)");

    /* SH-2 Command 0x0B "Clear Persistent DCD" takes no parameters.
     * BNO085 wipes its internal flash DCD region and continues running
     * with the in-memory calibration unchanged — the wipe only takes
     * effect after the next power-cycle or soft reset, which the
     * caller (pk_imu_factory_reset) performs via bno_bring_up(). */
    uint8_t p[9] = {0};
    return sh2_send_command(SH2_COMMAND_CLEAR_DCD, p);
}

/* --- Public Tare API ------------------------------------------------- */

esp_err_t pk_imu_tare_now(void)
{
    if (!s_imu_ready) return ESP_ERR_INVALID_STATE;

    /* Snapshot the latest post-sandwich attitude under the lock,
     * compute its conjugate, and stash that as the new offset. Next
     * frame, parse_rotation_vector() will multiply (aircraft attitude)
     * by (conjugate of attitude at tare moment), which collapses to
     * identity here and to the differential rotation as the chip moves
     * away from the tared pose. */
    xSemaphoreTake(s_sample_lock, portMAX_DELAY);
    float aw = s_last_aircraft_qw, ax = s_last_aircraft_qi,
          ay = s_last_aircraft_qj, az = s_last_aircraft_qk;
    quat_conj(aw, ax, ay, az,
              &s_tare_qw, &s_tare_qi, &s_tare_qj, &s_tare_qk);
    float ow = s_tare_qw, oi = s_tare_qi, oj = s_tare_qj, ok = s_tare_qk;
    xSemaphoreGive(s_sample_lock);

    ESP_LOGI(TAG, "software tare: captured (w,i,j,k) = "
                  "%+0.4f %+0.4f %+0.4f %+0.4f (PFD horizon now reads "
                  "roll/pitch 0/0; heading/HDG unchanged)",
             ow, oi, oj, ok);
    return ESP_OK;
}

esp_err_t pk_imu_tare_persist(void)
{
    esp_err_t err = pk_imu_tare_now();
    if (err != ESP_OK) return err;

    err = imu_nvs_save_tare(s_tare_qw, s_tare_qi, s_tare_qj, s_tare_qk);
    if (err != ESP_OK) {
        ESP_LOGW(TAG, "software tare persisted in RAM but NVS write "
                      "failed: %s — value lost on next reboot",
                 esp_err_to_name(err));
    } else {
        ESP_LOGI(TAG, "software tare persisted to NVS (survives reboot)");
    }
    return err;
}

esp_err_t pk_imu_factory_reset(void)
{
    if (!s_imu_ready) return ESP_ERR_INVALID_STATE;
    ESP_LOGW(TAG, "factory reset: wipe SW tare + NVS + BNO persisted "
                  "state + reinit chip");

    /* Step 1: in-RAM software tare → identity. From this point the
     * PFD reverts to raw mounting-corrected attitude. */
    xSemaphoreTake(s_sample_lock, portMAX_DELAY);
    s_tare_qw = 1.0f;
    s_tare_qi = 0.0f;
    s_tare_qj = 0.0f;
    s_tare_qk = 0.0f;
    xSemaphoreGive(s_sample_lock);

    /* Step 2: erase the persisted tare key so the next boot doesn't
     * restore a stale one. */
    esp_err_t err = imu_nvs_erase_tare();
    if (err != ESP_OK) {
        ESP_LOGW(TAG, "factory reset: NVS tare erase failed (%s) — "
                      "continuing", esp_err_to_name(err));
    }

    /* Step 3: scrub BNO's own persisted reorientation matrix (legacy
     * firmware may have written one via SH-2 Tare Persist). Belt and
     * braces: even if we never write it again, leaving it stale could
     * silently bias the raw output. */
    err = bno_clear_persisted_tare();
    if (err != ESP_OK) {
        ESP_LOGW(TAG, "factory reset: BNO clear-reorient failed (%s) — "
                      "continuing", esp_err_to_name(err));
    }
    vTaskDelay(pdMS_TO_TICKS(100));

    /* Step 4: wipe the persisted DCD so mag/gyro/accel calibration
     * re-learns on next fusion start. */
    err = bno_clear_persisted_dcd();
    if (err != ESP_OK) {
        ESP_LOGW(TAG, "factory reset: BNO clear-DCD failed (%s) — "
                      "continuing", esp_err_to_name(err));
    }
    vTaskDelay(pdMS_TO_TICKS(100));

    /* 重新武装 DCD 落盘：刚把 flash 里的 DCD 擦掉，用户接下来做 8 字校准把
     * acc 重新跑到 3，那份新校准值得存。不清这个标志的话，"每次开机最多存
     * 一次"的节流会把 factory reset 之后的重新校准挡在门外——用户白做一遍
     * 8 字，还得再重启一次才能生效。 */
    s_dcd_saved = false;

    /* Step 5: hard reset + replay init so the chip rebuilds fusion
     * state from now-clean flash. */
    err = bno_bring_up();
    if (err != ESP_OK) {
        ESP_LOGW(TAG, "factory reset: chip reinit failed (%s) — "
                      "watchdog will retry within 5 s",
                 esp_err_to_name(err));
    } else {
        ESP_LOGI(TAG, "factory reset complete — start figure-8 motion "
                      "to let BNO085 re-learn magnetometer calibration");
    }
    return err;
}
