naizhao/Pilot-Kit-Box-ESP32-P4/firmware/main/traffic_page.c

/*
 * traffic_page.c — 360° 交通雷达页。
 *
 * 数据获取照 pfd.c 的 PFD 分支：own_ship 取位置、IMU yaw 取机头磁航向、
 * aircraft_state_snapshot 取目标。相对高度的本机基准走
 * pk_traffic_own_press_alt()——舱内 BMP388 **不是**合法基准（增压座舱里它
 * 读到的是座舱高度），所以本页不再读 baro。几何用纯函数
 * pk_traffic_rel_calc（全程磁北系，含磁偏角修正）。绘制用 pfd_draw /
 * pfd_font 原语。像素布局参照原型 traffic_radar_interactive.html。
 *
 * 朝向：
 *   HEADING-UP — 屏幕上方=机头，目标用 rel_bearing 投影，罗盘随 yaw 转。
 *   NORTH-UP   — 屏幕上方=磁北，目标用 abs_bearing 投影（本机三角随 yaw
 *                旋转标记朝向：Task8 完善，本版三角暂朝上）。
 */
#include "traffic_page.h"

#include <math.h>
#include <stdio.h>
#include <string.h>

#include "esp_attr.h"
#include "esp_timer.h"
#include "sdkconfig.h"

#include "display.h"
#include "i18n.h"
#include "pfd_layout.h"
#include "pfd_statusbar.h"   /* pk_ui_topbar_right_limit —— 给 DEMO 徽标让位 */
#include "pfd_aa_text.h"
#include "pfd_aa_font.h"
#include "pfd_icon_font.h"
#include "pfd_draw.h"
#include "pfd_font.h"

#include "aircraft_state.h"
#include "own_ship.h"
#include "imu_task.h"

#include "config_traffic.h"
#include "traffic_geom.h"
#include "mag_var.h"
#include "aircraft_db.h"
#include "pk_callsign.h"     /* pk_callsign_display —— 呼号/ICAO 回退，三页共用 */
#include "ui_state.h"
#include "pk_own_sampler.h"   /* pk_own_sampler_get_phase() —— 显著性跟随本机相位 */

/* ── 布局（800×480，spec §5.2）───────────────────────────────
 *
 *   0            520                800
 *   ├─────────────┼──────────────────┤
 *   │   雷达区     │  右栏 4 张卡片    │
 *   │  本机居中     │  方位/呼号/距离   │
 *   │             │  /高度/速度       │
 *
 * 半径受**高度**限制而不是宽度：顶栏之下只剩 432 px，而左栏有 520 px 宽。
 * 取 RMAX 200，上下各留 16 px 呼吸；水平仍居中在 520 的中线上。 */
#define TFC_RADAR_W   520
#define TFC_SIDE_X    TFC_RADAR_W          /* 右栏左边界 */
#define TFC_TOP       PFD_BAR_BOT          /* 顶栏与 PFD 等高 */

#define CX     (TFC_RADAR_W / 2)
#define CY     (TFC_TOP + (PK_DISPLAY_H - TFC_TOP) / 2)
#define RMAX   200

/* 文字统一走抗锯齿字体。原先满页 5×7 位图，在 217 PPI 上既小又糊，与已改好
 * 的其余页面也不是一套。
 * 2026-08-01：配套的 TFC_PUTS_XS 已删——卡片里的次要列直接调 pk_aa_puts(…,
 * PK_AA_XS)，那个宏从落地起就没有使用者。 */
#define TFC_PUTS(fb, x, y, s, col) \
        pk_aa_puts((fb), PK_DISPLAY_W, PK_DISPLAY_H, (x), (y), (s), (col), PK_AA_M)
/* 顶栏其余读数与标题同一条基线，所以直接取标题的纵坐标。 */
#define TFC_HDR_TY    PK_UI_TITLE_Y

/* ── 右栏（spec §5.2：280 px，4 张卡片可滚动）───────────────── */
#define SIDE_X        TFC_SIDE_X
/* 行高与内边距直接取 PFD 信息框的值（PFD_IB_ROW_H/_GAP/_PAD）。
 *
 * 一开始自己造了「卡片」：一张 76~97 px、三行内容、带边框。做出来又大又
 * 看不懂。PFD 右下角那三行（B / ALT / VS）早就把这类信息排明白了——一行一
 * 条、半透明底、左标签右数值，没有边框。同一台设备上不该有两套列表语言。 */
#define ROW_PAD       PFD_IB_PAD
#define ROW_GAP       PFD_IB_ROW_GAP
/* 两行一条：五个字段在 280 px 里排不进一行——试过，呼号会和距离撞上。
 * 主行放「在哪边 + 是谁 + 高度差」，次行放「多远 + 多快」。 */
#define ROW_H         (PK_AA_M_H + PK_AA_XS_H + 8)
#define ROW_N         ((PK_DISPLAY_H - PFD_BAR_BOT - 12) / (ROW_H + ROW_GAP))
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
